Big-Red-Sat/Perovskite-Curve-Tracer/paper/Curve Tracer Hardware.pdf

## An Open Source Perovskite Solar Cell Passive Curve Tracer

Walker S. Arce

University of Nebraska-Lincoln, Department of Electrical and Computer Engineering, Lincoln, 68588, United States

E-mail: wsarcera@gmail.com

September 2025

Abstract. When developing systems for perovskite solar cells, it’s important to have a testing platform that closely resembles your deployed systems. While developing a 1U CubeSat, the Big Red Sat-1, at the University of Nebraska-Lincoln, we found a lack of passive curve tracing instrumentation, which we needed for our mission. To that end, we developed a benchtop passive curve tracer that leverages the Ossila Solar Simulator as an AM1.0 light source. This device utilizes a ladder of switched resistors and a precision voltage and current measurement to achieve the curve tracing. It also integrates a common-anode multiplexer to switch through multi-pixel perovskite solar cells. Finally, the solar cell holder is separate from the main measurement system, so various substrates sizes and pixel counts can be supported. This system is tested using various perovskite solar cells. It has been open sourced to enable reuse in future systems that may benefit from the lower power consumption and flight heritage.

REFERENCES | 2
20 | Introduction
21 | Methods
22 | Results
23 | Discussion
24 | Conclusions
25 | Acknowledgments
26 | Author contributions statement
27 | Competing interests
28 | References
29 | [1] Walker Arce. “Unobtrusive Data Collection in Clinical Settings for Advanced
30 | Patient Monitoring and Machine Learning”. MA thesis. University of Nebraska-
31 | Lincoln, 2023.
32 | [2] Walker Arce and James Gehringer. “Biosensor framework: AC# library for
33 | affective computing”. In: Journal of Open Source Software 6.64 (2021), p. 3455.
34 | [3] Walker S Arce et al. “Detecting aggression in clinical treatment videos”. In:
35 | Machine Learning with Applications 14 (2023), p. 100515.
36 | [4] Mathias Benedek and Christian Kaernbach. “A continuous measure of phasic
37 | electrodermal activity”. In: Journal of neuroscience methods 190.1 (2010), pp. 80–
38 | 91.
39 | [5] Marc G Berman, John Jonides, and Stephen Kaplan. “The cognitive benefits of
40 | interacting with nature”. In: Psychological science 19.12 (2008), pp. 1207–1212.
41 | [6] L Breiman. “Random forests-random features Technical Report 576”. In: Statistical
42 | Department, UC Berkeley, USA (1999).
43 | [7] Leo Breiman and Ross Ihaka. Nonlinear discriminant analysis via scaling and
44 | ACE. Department of Statistics, University of California Davis One Shields
45 | Avenue . . ., 1984.
46 | [8] David F Cella and Samuel W Perry. “Reliability and concurrent validity of three
47 | visual-analogue mood scales”. In: Psychological reports 59.2 (1986), pp. 827–833.
48 | [9] Bernadine Cimprich. “Development of an intervention to restore attention in
49 | cancer patients”. In: Cancer nursing 16.2 (1993), pp. 83–92.
50 | [10] Jonathan D Cohen et al. “Activation of the prefrontal cortex in a nonspatial
51 | working memory task with functional MRI”. In: Human brain mapping 1.4 (1994),
52 | pp. 293–304.

REFERENCES | 3
[11] Christian Collet et al. “Autonomic nervous system response patterns specificity to basic emotions”. In: Journal of the autonomic nervous system 62.1-2 (1997), pp. 45–57.
[12] Sidney D’Mello, Arvid Kappas, and Jonathan Gratch. “The affective computing approach to affect measurement”. In: Emotion Review 10.2 (2018), pp. 174–183.
[13] Jia Deng et al. “Imagenet: A large-scale hierarchical image database”. In: 2009 IEEE conference on computer vision and pattern recognition. Ieee. 2009, pp. 248– 255.
[14] Deniz Ekiz et al. “Can a smartband be used for continuous implicit authentication in real life”. In: IEEE Access 8 (2020), pp. 59402–59411.
[15] Vahid Farrahi et al. “Evaluating and enhancing the generalization performance of machine learning models for physical activity intensity prediction from raw acceleration data”. In: IEEE journal of biomedical and health informatics 24.1 (2019), pp. 27–38.
[16] Simon Föll et al. “FLIRT: A feature generation toolkit for wearable data”. In: Computer Methods and Programs in Biomedicine 212 (2021), p. 106461.
[17] Martin Gjoreski et al. “Datasets for cognitive load inference using wearable sensors and psychological traits”. In: Applied Sciences 10.11 (2020), p. 3843.
[18] Matthew S Goodwin et al. “Predicting aggression to others in youth with autism using a wearable biosensor”. In: Autism research 12.8 (2019), pp. 1286–1296.
[19] Alberto Greco et al. “cvxEDA: A convex optimization approach to electrodermal activity processing”. In: IEEE transactions on biomedical engineering 63.4 (2015), pp. 797–804.
[20] Linda Handlin et al. “Short-term interaction between dogs and their owners: effects on oxytocin, cortisol, insulin and heart rate—an exploratory study”. In: Anthrozoös 24.3 (2011), pp. 301–315.
[21] Trevor Hastie et al. The elements of statistical learning: data mining, inference, and prediction. Vol. 2. Springer, 2009.
[22] Jennifer A Healey and Rosalind W Picard. “Detecting stress during real-world driving tasks using physiological sensors”. In: IEEE Transactions on intelligent transportation systems 6.2 (2005), pp. 156–166.
[23] Geoffrey E Hinton. “Connectionist learning procedures”. In: Machine learning. Elsevier, 1990, pp. 555–610.
[24] Seyedmajid Hosseini et al. “A multimodal sensor dataset for continuous stress detection of nurses in a hospital”. In: Scientific Data 9.1 (2022), p. 255.
[25] Palanisamy Karthikeyan, Murugappan Murugappan, and Sazali Yaacob. “Descriptive analysis of skin temperature variability of sympathetic nervous system activity in stress”. In: Journal of Physical Therapy Science 24.12 (2012), pp. 1341–1344.
[26] Diederik P Kingma and Jimmy Ba. “Adam: A method for stochastic optimization”. In: arXiv preprint arXiv:1412.6980 (2014).

REFERENCES | 4
93 | [27] Sylvia D Kreibig. “Autonomic nervous system activity in emotion: A review”. In:
94 | Biological psychology 84.3 (2010), pp. 394–421.
95 | [28] Qiang Li and Kunio Doi. “Reduction of bias and variance for evaluation of
96 | computer-aided diagnostic schemes”. In: Medical physics 33.4 (2006), pp. 868–
97 | 875.
98 | [29] Brian Mac Namee et al. “The problem of bias in training data in regression
99 | problems in medical decision support”. In: Artificial intelligence in medicine 24.1
100 | (2002), pp. 51–70.
101 | [30] Cathy L McEvoy, Douglas L Nelson, and Takako Komatsu. “What is the
102 | connection between true and false memories? The differential roles of interitem
103 | associations in recall and recognition.” In: Journal of Experimental Psychology:
104 | Learning, Memory, and Cognition 25.5 (1999), p. 1177.
105 | [31] J Orbach, Dan Ehrlich, and Helen A Heath. “Reversibility of the Necker cube: I.
106 | An examination of the concept of “satiation of orientation””. In: Perceptual and
107 | motor skills 17.2 (1963), pp. 439–458.
108 | [32] Fabian Pedregosa et al. “Scikit-learn: Machine learning in Python”. In: the Journal
109 | of machine Learning research 12 (2011), pp. 2825–2830.
110 | [33] Jonathan Peirce et al. “PsychoPy2: Experiments in behavior made easy”. In:
111 | Behavior research methods 51 (2019), pp. 195–203.
112 | [34] Laura E Phipps et al. “Assessing physiological arousal and emotional valence
113 | during behavioral intervention for pediatric feeding difficulties: A pilot study”.
114 | In: Mental Health Science (2024), e74.
115 | [35] Rosalind W Picard. Affective computing. MIT press, 2000.
116 | [36] Ming-Zher Poh, Nicholas C Swenson, and Rosalind W Picard. “A wearable
117 | sensor for unobtrusive, long-term assessment of electrodermal activity”. In: IEEE
118 | transactions on Biomedical engineering 57.5 (2010), pp. 1243–1252.
119 | [37] Society for Psychophysiological Research Ad Hoc Committee on Electrodermal
120 | Measures et al. “Publication recommendations for electrodermal measurements”.
121 | In: Psychophysiology 49.8 (2012), pp. 1017–1034.
122 | [38] Nishkam Ravi et al. “Activity recognition from accelerometer data”. In: Aaai.
123 | Vol. 5. Pittsburgh, PA. 2005, pp. 1541–1546.
124 | [39] Debra Lynn Rich. “Effects of exposure to nature and plants on cognition and
125 | mood: A cognitive psychology perspective”. PhD thesis. Cornell University, 2007.
126 | [40] Henry L Roediger and Kathleen B McDermott. “Creating false memories:
127 | Remembering words not presented in lists.” In: Journal of experimental psychology:
128 | Learning, Memory, and Cognition 21.4 (1995), p. 803.
129 | [41] Eva Sahlin et al. “The influence of the environment on directed attention, blood
130 | pressure and heart rate—An experimental study using a relaxation intervention”.
131 | In: Landscape Research 41.1 (2016), pp. 7–25.

REFERENCES | 5
[42] E Salazar-López et al. “The mental and subjective skin: Emotion, empathy, feelings and thermography”. In: Consciousness and cognition 34 (2015), pp. 149–162.
[43] Philip Schmidt et al. “Introducing wesad, a multimodal dataset for wearable stress and affect detection”. In: Proceedings of the 20th ACM international conference on multimodal interaction. 2018, pp. 400–408.
[44] Fred Shaffer and Jay P Ginsberg. “An overview of heart rate variability metrics and norms”. In: Frontiers in public health 5 (2017), p. 258.
[45] Karan Sharma et al. “A dataset of continuous affect annotations and physiological signals for emotion analysis”. In: Scientific data 6.1 (2019), p. 196.
[46] Dimitris Spathis et al. “Learning generalizable physiological representations from large-scale wearable data”. In: arXiv preprint arXiv:2011.04601 (2020).
[47] Charles D Spielberger et al. Measuring anxiety and anger with the State-Trait Anxiety Inventory (STAI) and the State-Trait Anger Expression Inventory (STAXI). Lawrence Erlbaum Associates Publishers, 1999.
[48] Jeffrey R. Stevens and Elise R. Thayer. “Effects of human-animal interactions on affect and cognition”. In: Human-animal interaction bulletin (2020). url: https: //api.semanticscholar.org/CorpusID:225526352.
[49] Mohammed Taj-Eldin et al. “A review of wearable solutions for physiological and emotional monitoring for use by people with autism spectrum disorder and their caregivers”. In: Sensors 18.12 (2018), p. 4271.
[50] Hoang Minh Thang et al. “Gait identification using accelerometer on mobile phone”. In: 2012 International Conference on Control, Automation and Information Sciences (ICCAIS). IEEE. 2012, pp. 344–348.
[51] Elise R Thayer and Jeffrey R Stevens. “Effects of human-animal interactions on affect and cognition”. In: Human-Animal Interaction Bulletin 2022 (2022).
[52] Paul Van Gent et al. “HeartPy: A novel heart rate algorithm for the analysis of noisy signals”. In: Transportation research part F: traffic psychology and behaviour 66 (2019), pp. 368–378.
[53] David Watson, Lee Anna Clark, and Auke Tellegen. “Development and validation of brief measures of positive and negative affect: the PANAS scales.” In: Journal of personality and social psychology 54.6 (1988), p. 1063.
[54] Debra Wetcher-Hendricks. Analyzing quantitative data: An introduction for social researchers. John Wiley & Sons, 2011.
