Big-Red-Sat/Perovskite-Curve-Tracer/software/curves/1. Round One/1763_Again2/1763_Again2_plotted.png

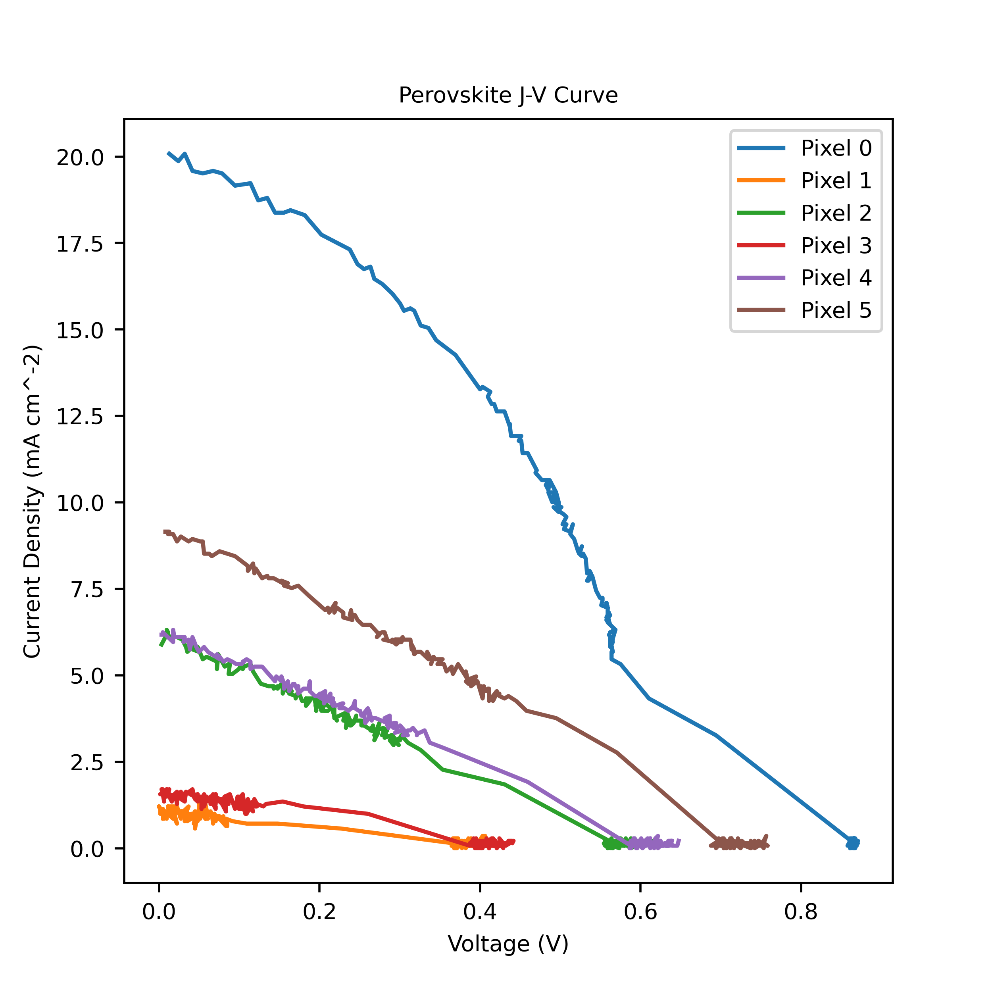
software/curves/1. Round One/1763_Again2/1763_Again2_plotted.png
