Big-Red-Sat/Perovskite-Curve-Tracer/software/curves/1. Round One/1763_Again/1763_Again_plotted.png

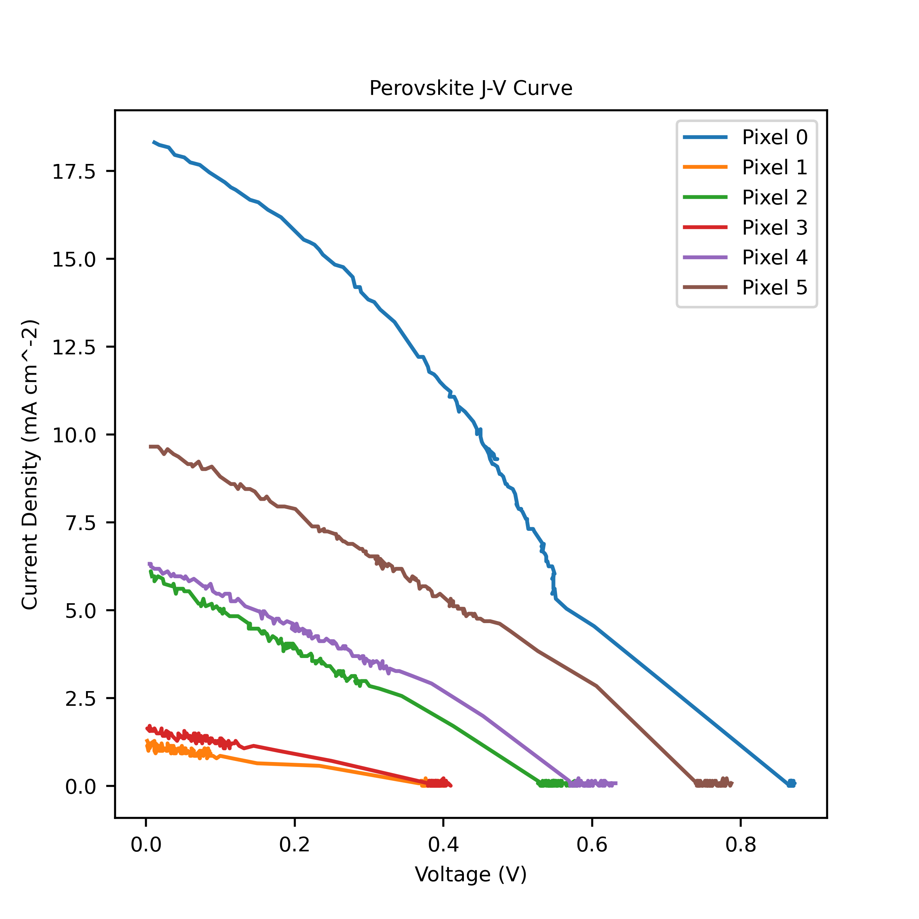
software/curves/1. Round One/1763_Again/1763_Again_plotted.png
