Big-Red-Sat/Perovskite-Curve-Tracer/software/curves/1. Round One/1764_Degradation/1764_08222023/1764_08222023_plotted.png

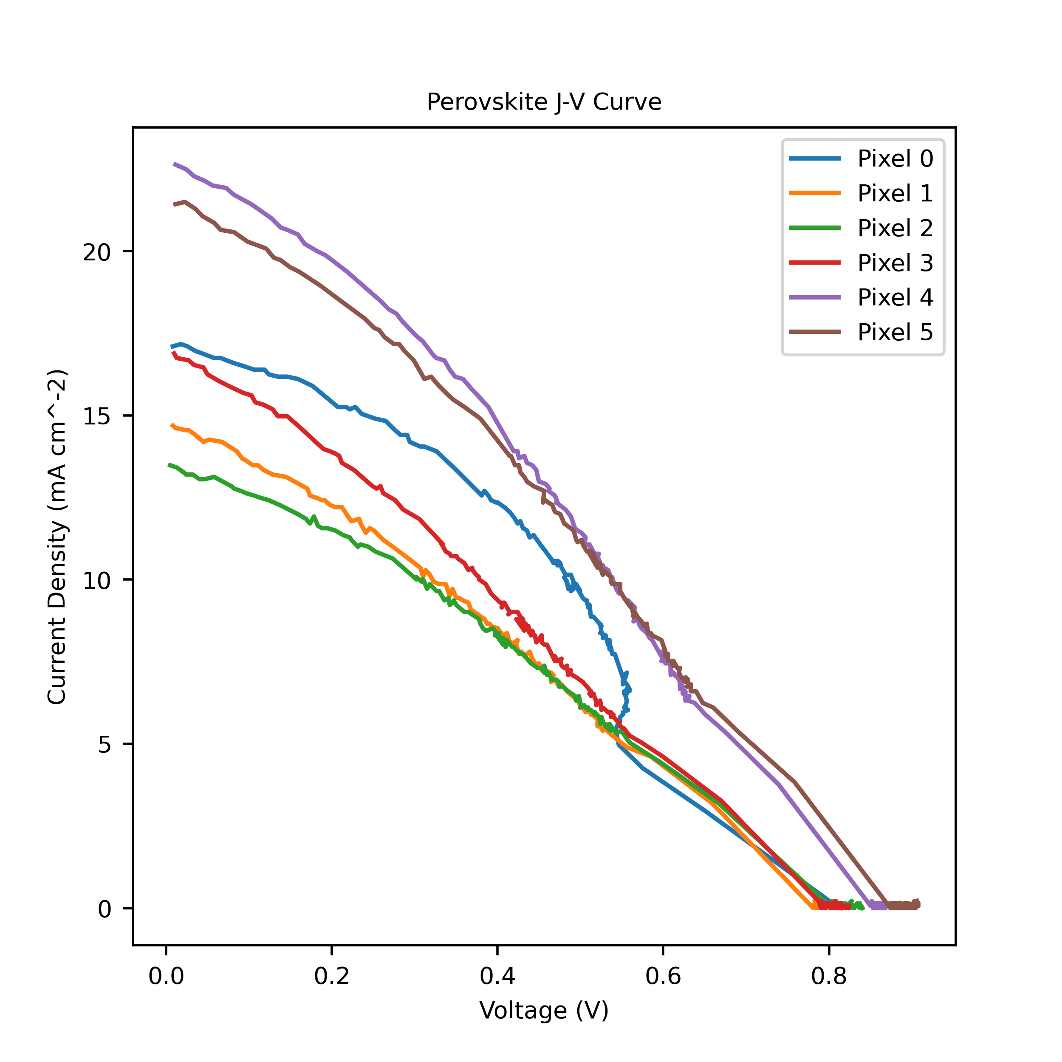
software/curves/1. Round One/1764_Degradation/1764_08222023/1764_08222023_plotted.png
