Big-Red-Sat/Perovskite-Curve-Tracer/software/curves/1. Round One/1764_Degradation/1764_08232023_2/1764_08232023_2_plotted.png

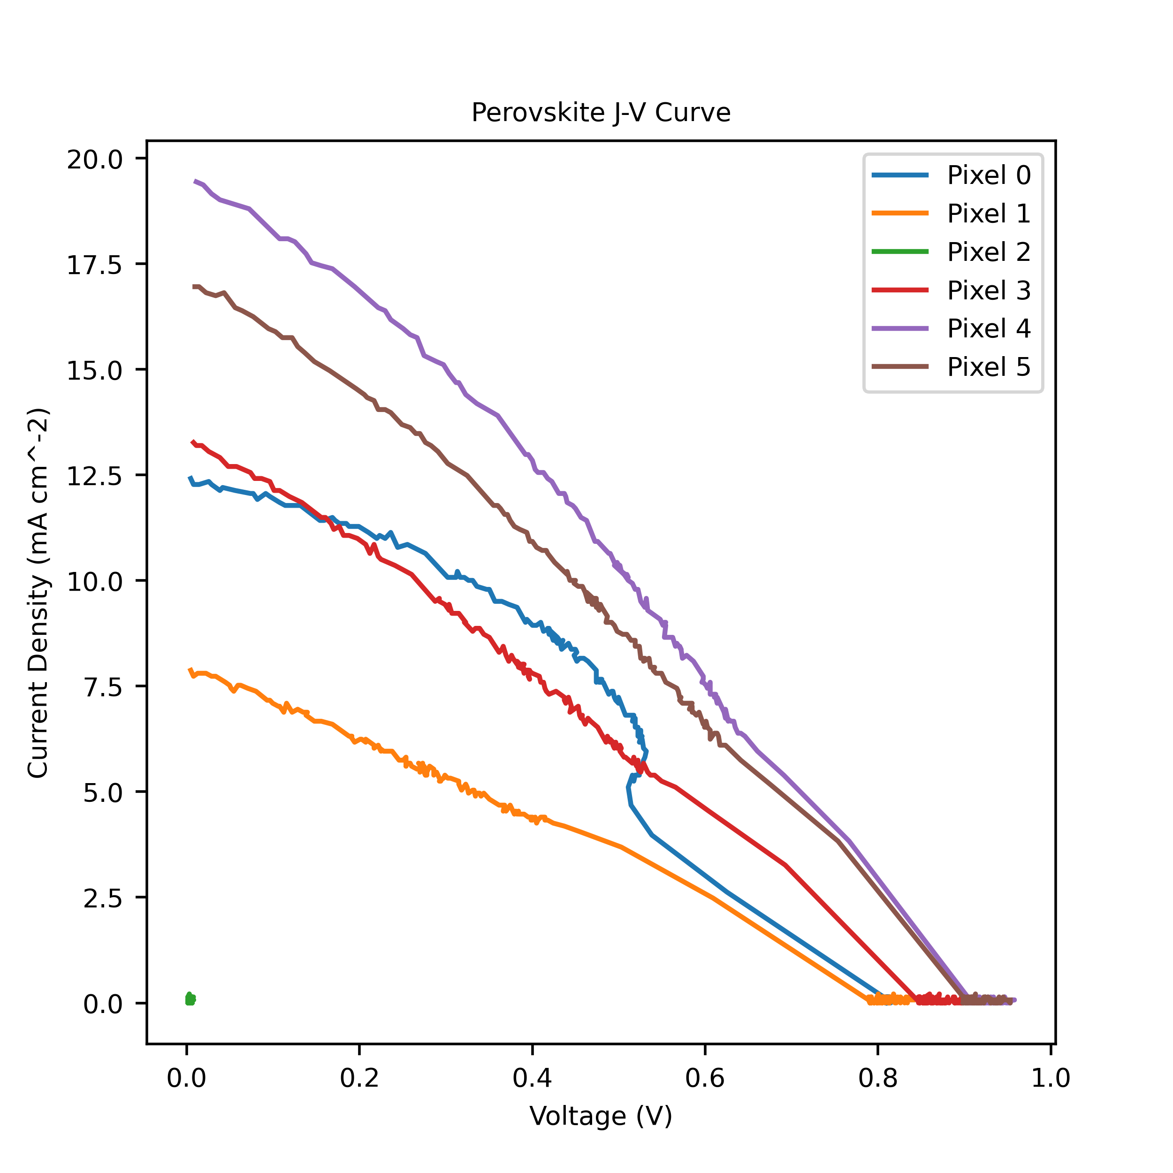
software/curves/1. Round One/1764_Degradation/1764_08232023_2/1764_08232023_2_plotted.png
