Big-Red-Sat/Perovskite-Curve-Tracer/software/curves/1. Round One/1764_Degradation/1764_08242023_LM/1764_08242023_LM_plotted.png

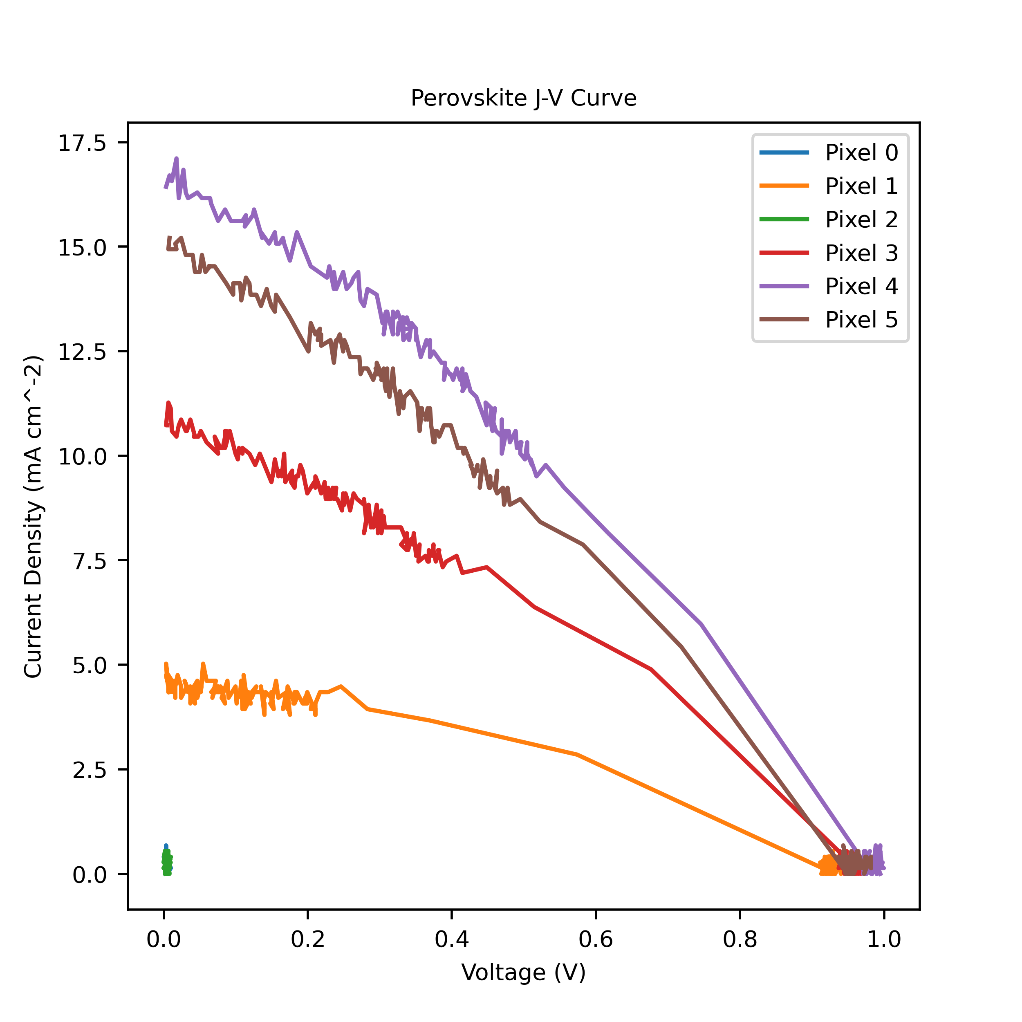
software/curves/1. Round One/1764_Degradation/1764_08242023_LM/1764_08242023_LM_plotted.png
