Big-Red-Sat/Perovskite-Curve-Tracer/software/curves/1. Round One/1764_Degradation/1764_Again/1764_Again_plotted.png

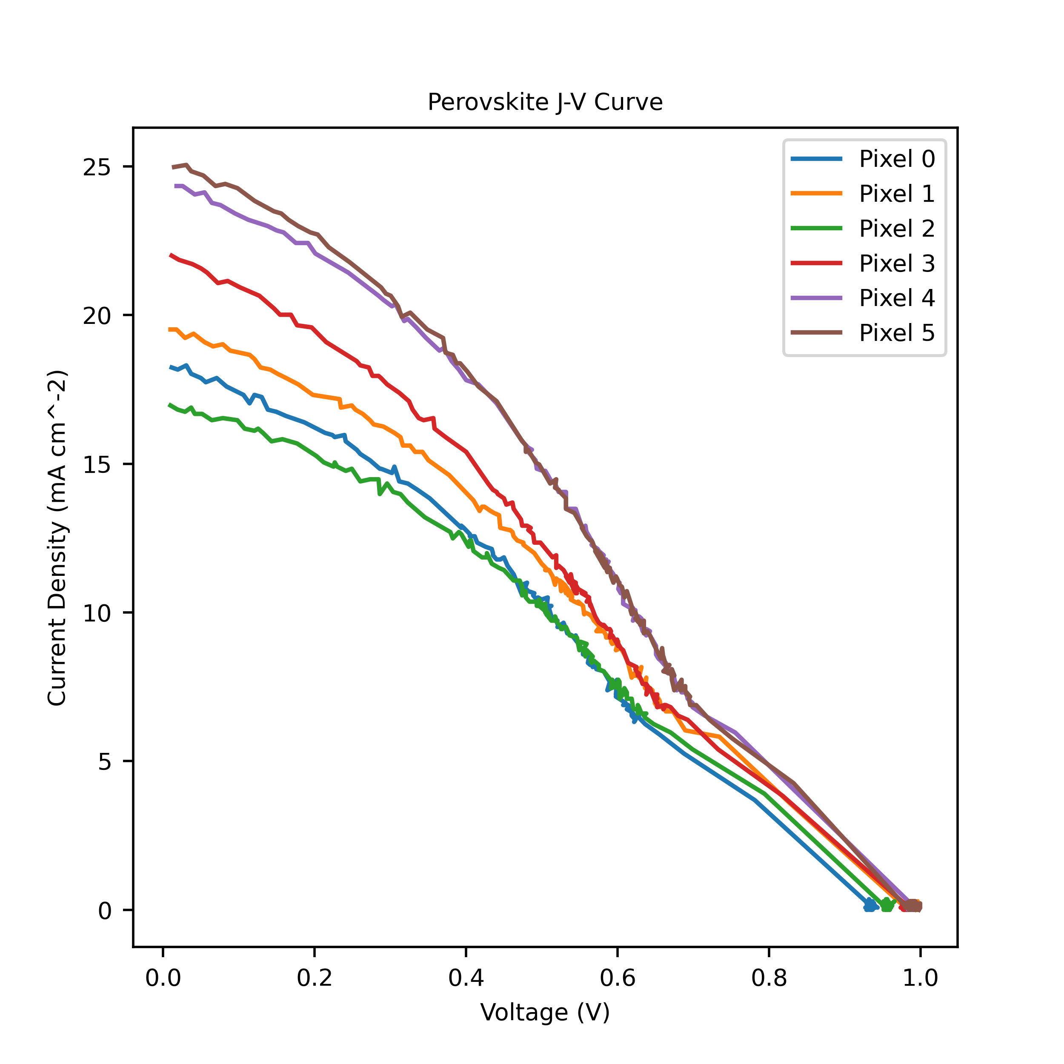
software/curves/1. Round One/1764_Degradation/1764_Again/1764_Again_plotted.png
