Big-Red-Sat/Perovskite-Curve-Tracer/software/curves/1. Round One/1765_Again/1765_Again_plotted.png

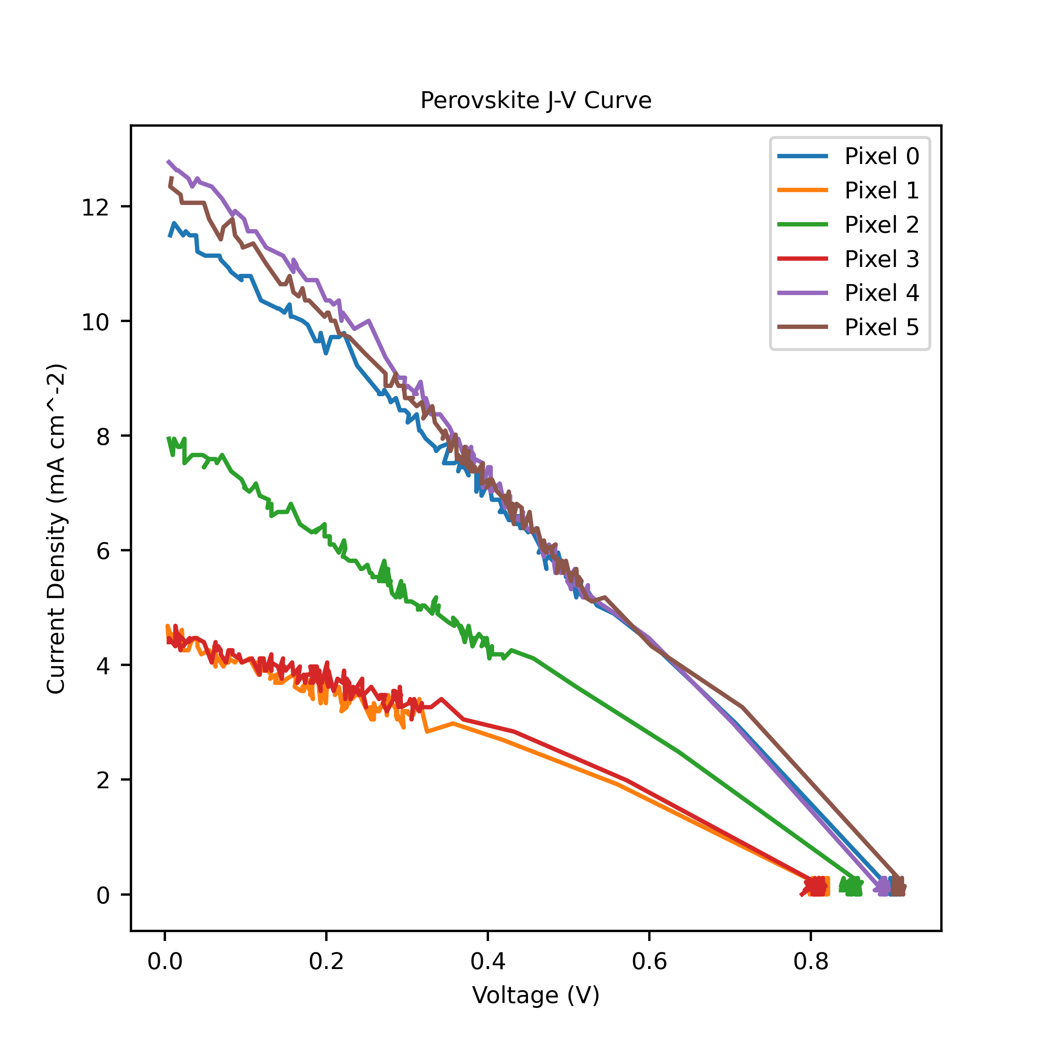
software/curves/1. Round One/1765_Again/1765_Again_plotted.png
