Big-Red-Sat/Perovskite-Curve-Tracer/software/curves/1. Round One/1770_Again/1770_Again_plotted.png

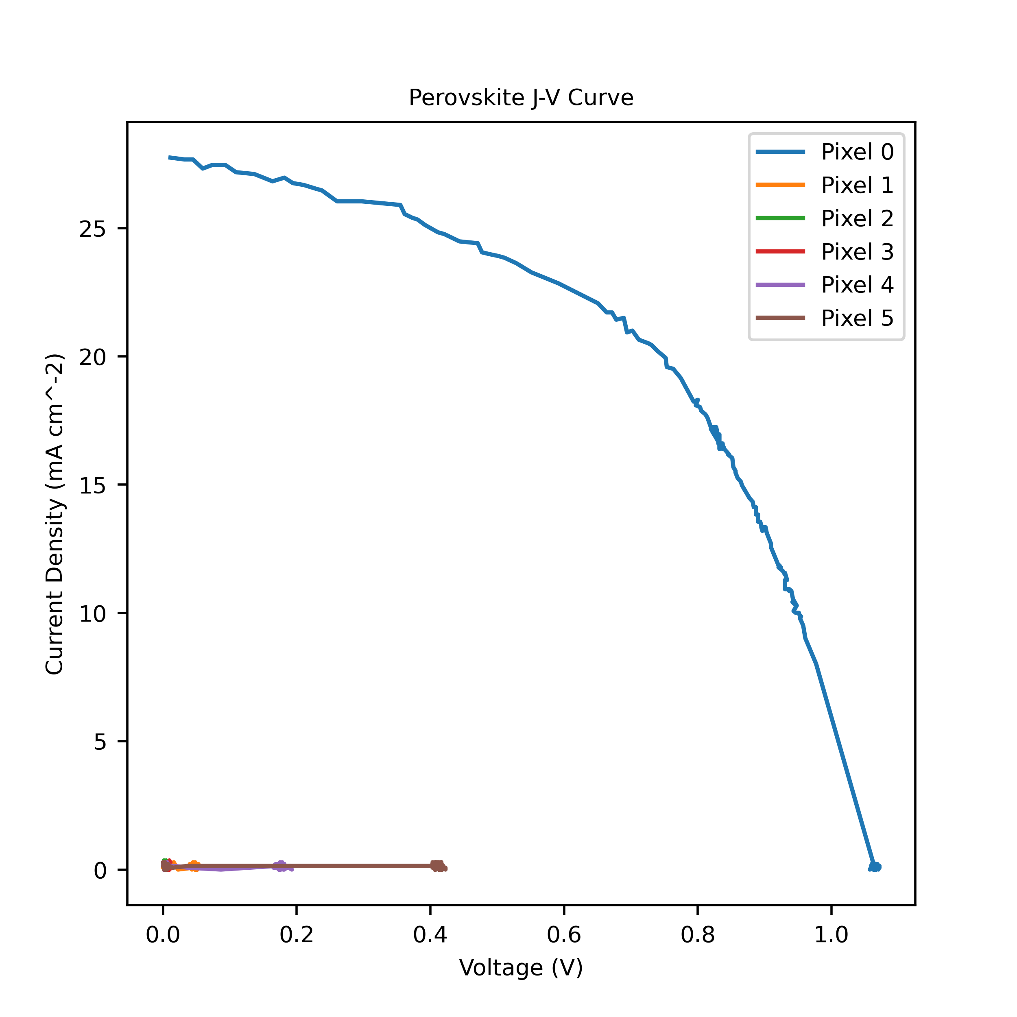
software/curves/1. Round One/1770_Again/1770_Again_plotted.png
