Big-Red-Sat/Perovskite-Curve-Tracer/software/curves/1. Round One/1773_Again/1773_Again_plotted.png

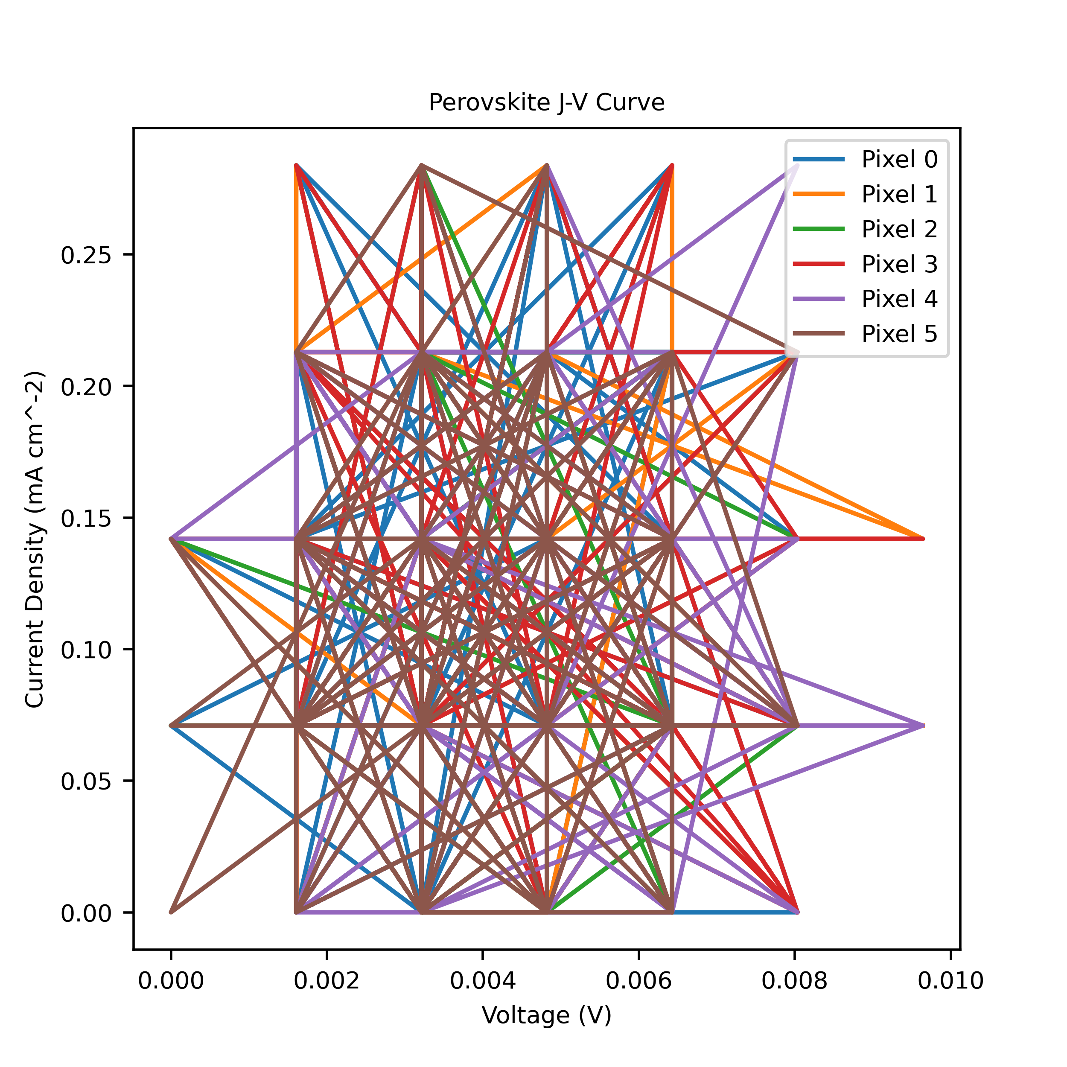
software/curves/1. Round One/1773_Again/1773_Again_plotted.png
