Big-Red-Sat/Perovskite-Curve-Tracer/software/curves/1. Round One/1775_Again/1775_Again_plotted.png

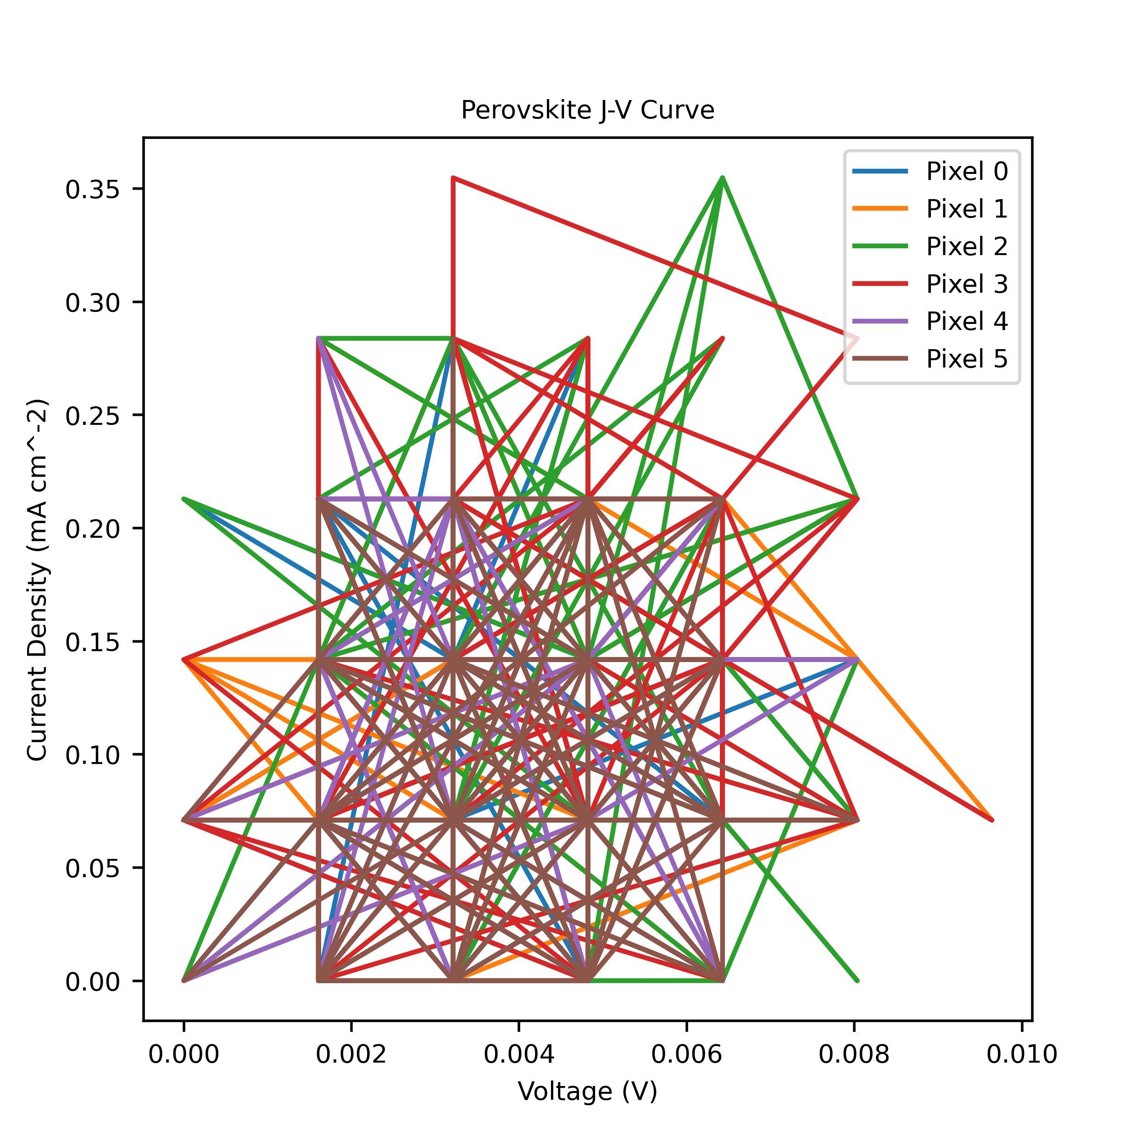
software/curves/1. Round One/1775_Again/1775_Again_plotted.png
