Big-Red-Sat/Perovskite-Curve-Tracer/software/curves/1. Round One/1776 Degradation/1776_08192023/1776_08192023.png

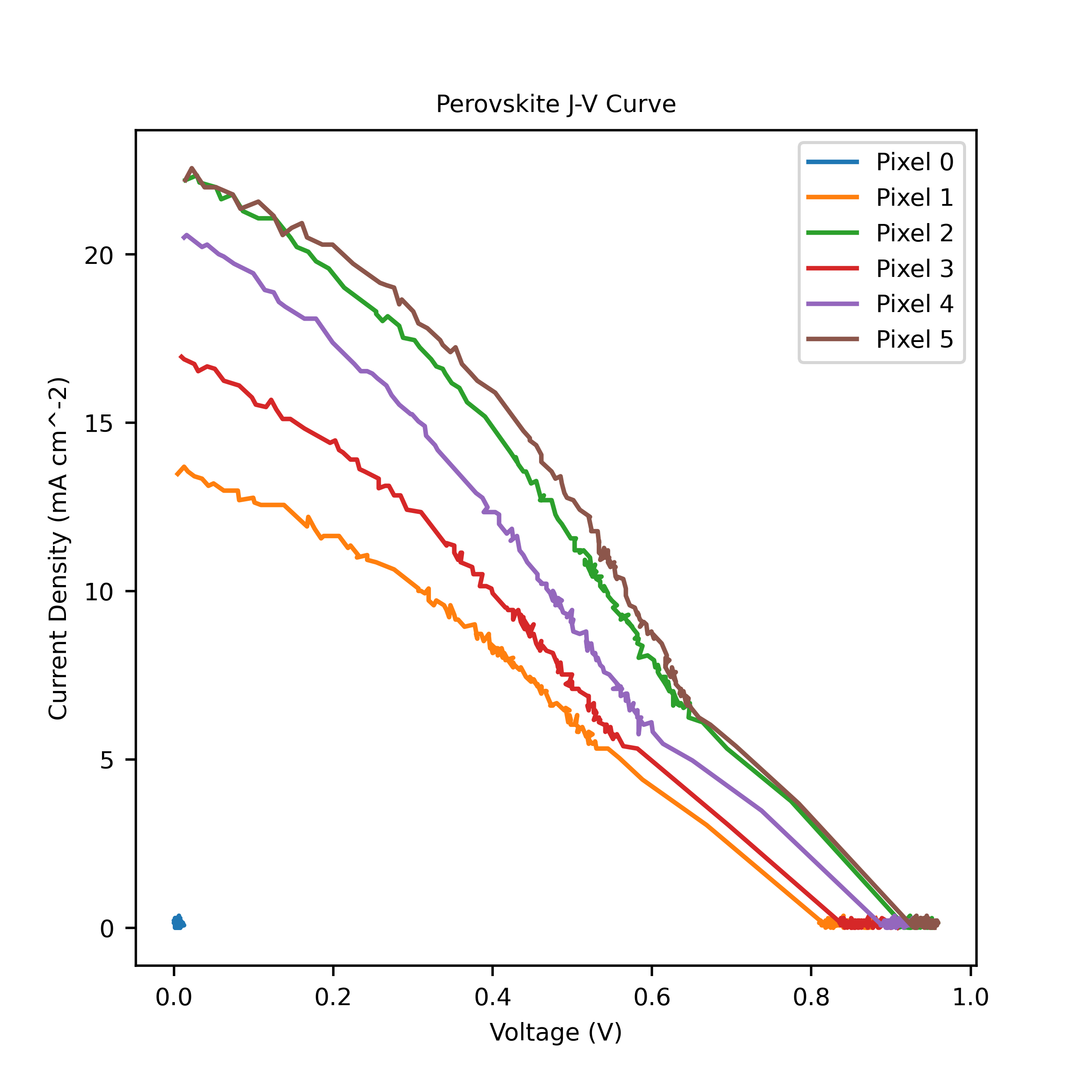
software/curves/1. Round One/1776 Degradation/1776_08192023/1776_08192023.png
