Big-Red-Sat/Perovskite-Curve-Tracer/software/curves/1. Round One/1776 Degradation/1776_08192023_2/1776_Again2_plotted.png

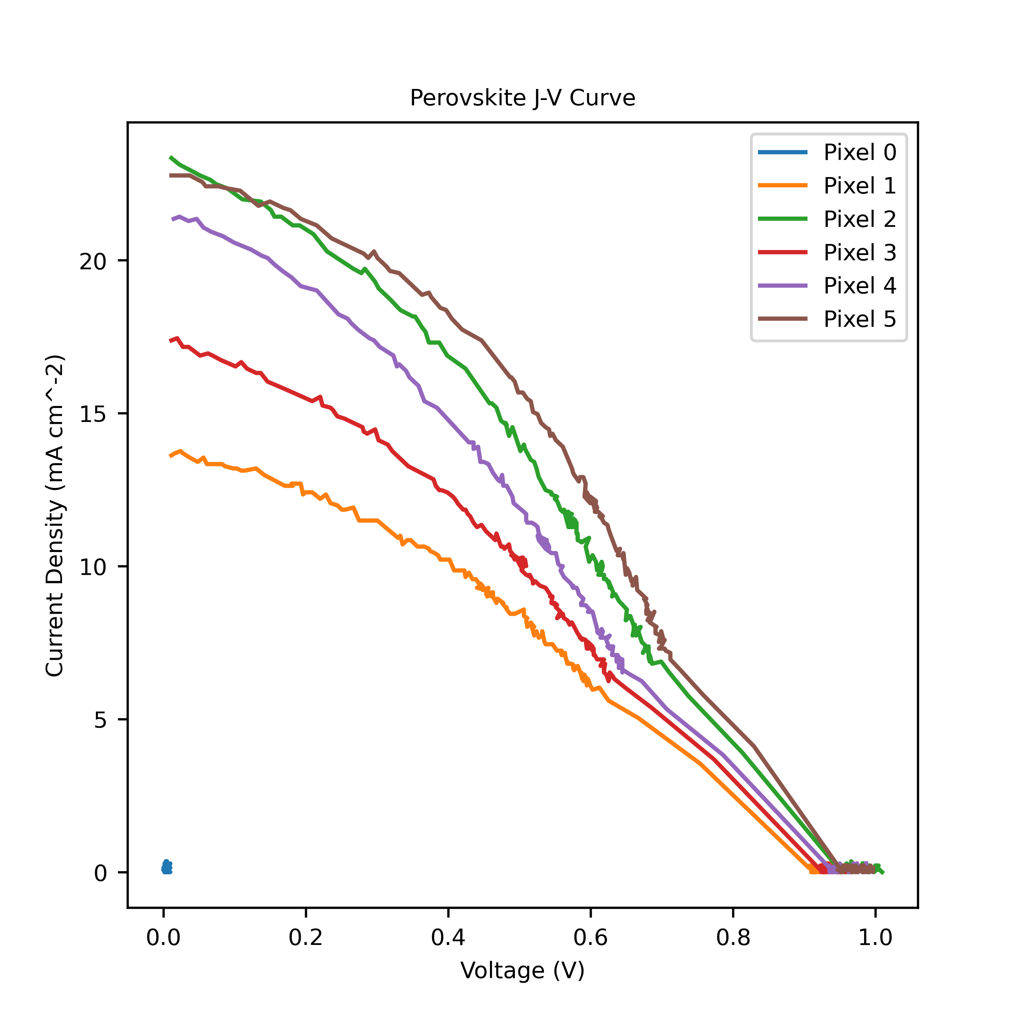
software/curves/1. Round One/1776 Degradation/1776_08192023_2/1776_Again2_plotted.png
