Big-Red-Sat/Perovskite-Curve-Tracer/software/curves/1. Round One/1776 Degradation/1776_08212023_3/1776_08212023_plotted.png

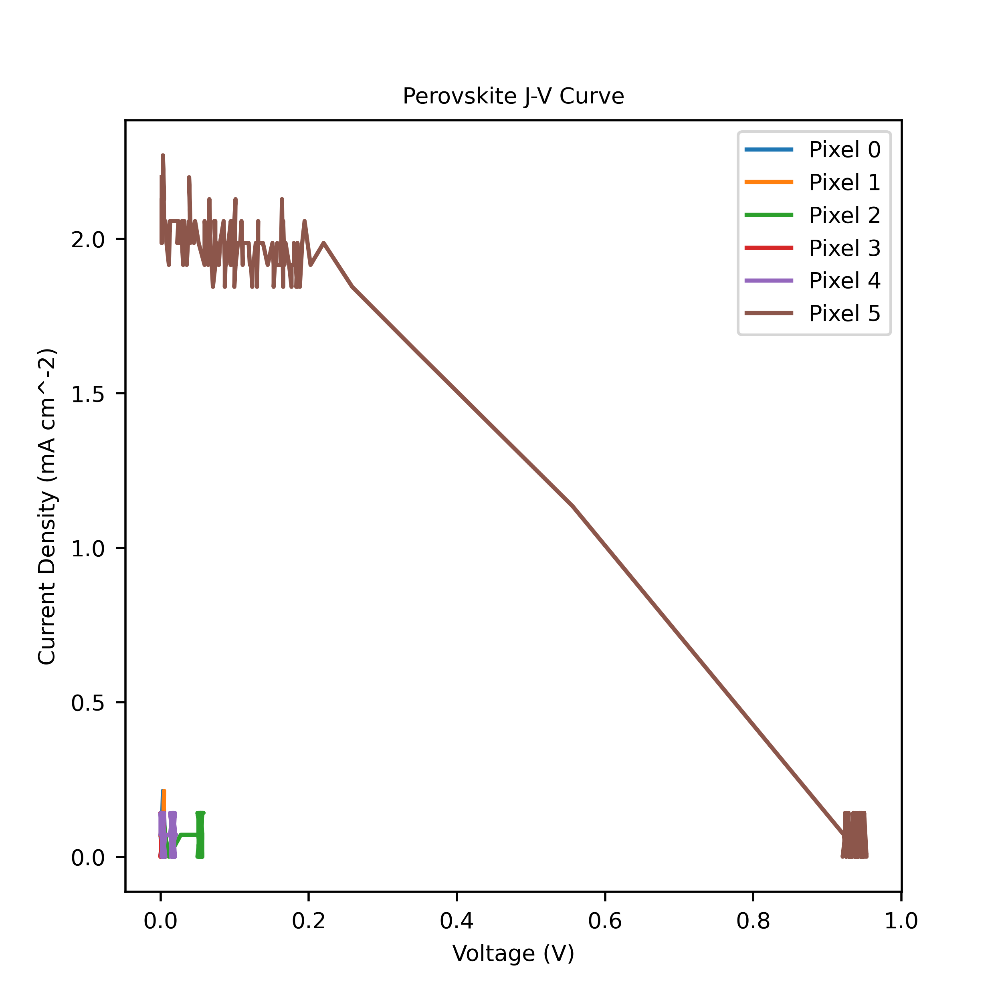
software/curves/1. Round One/1776 Degradation/1776_08212023_3/1776_08212023_plotted.png
