Big-Red-Sat/Perovskite-Curve-Tracer/software/curves/1. Round One/1776 Degradation/1776_08222023_R/1776_08222023_R_plotted.png

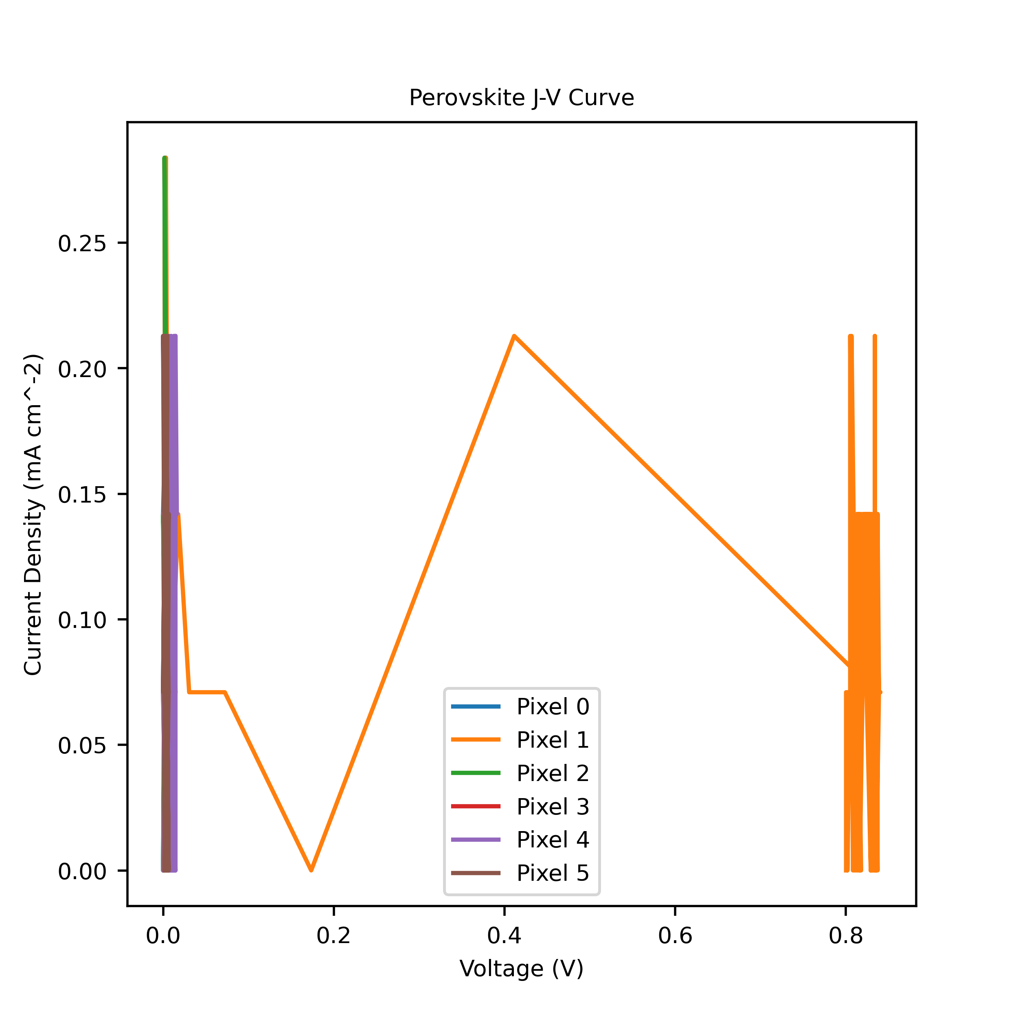
software/curves/1. Round One/1776 Degradation/1776_08222023_R/1776_08222023_R_plotted.png
