Big-Red-Sat/Perovskite-Curve-Tracer/software/curves/2. Round Two/1008_21_15_degredation/1008_21_15_degredation_plotted_Reverse.png

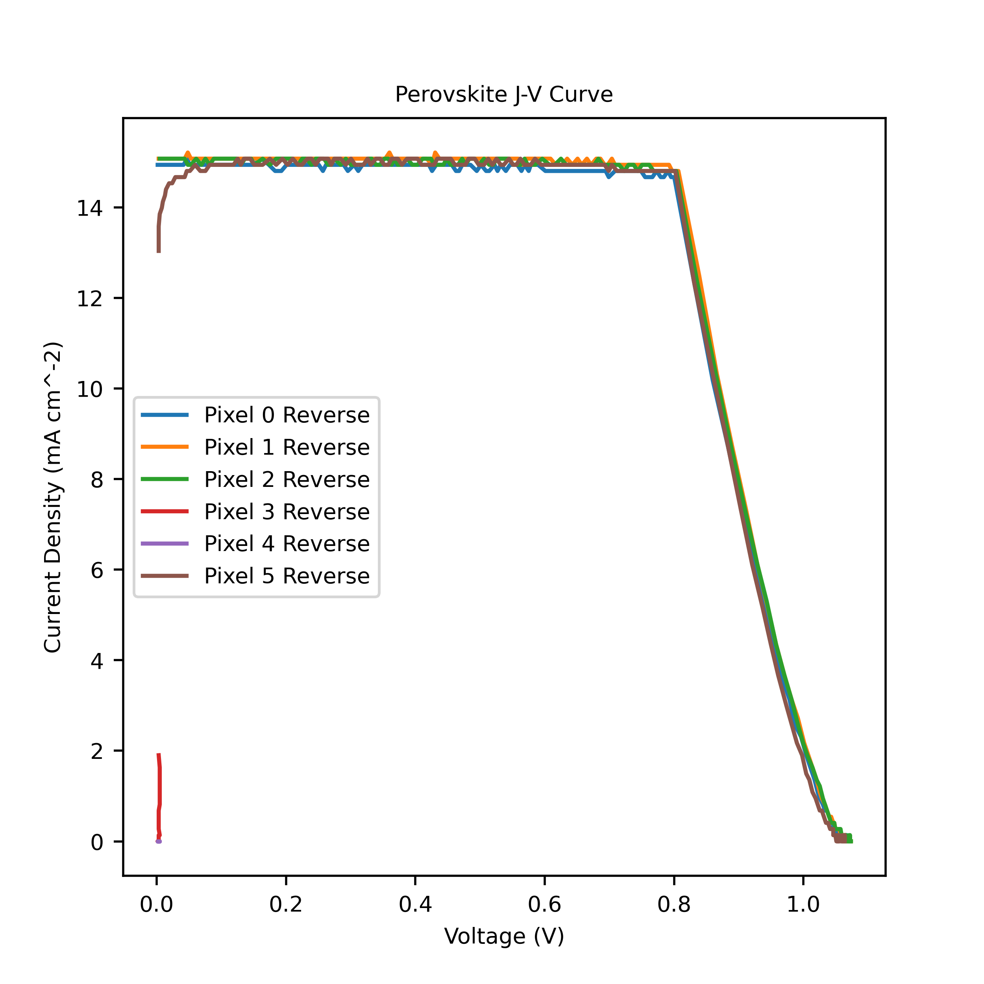
software/curves/2. Round Two/1008_21_15_degredation/1008_21_15_degredation_plotted_Reverse.png
