Big-Red-Sat/Perovskite-Curve-Tracer/software/curves/2. Round Two/100623_14_44_degredations/100623_14_44_degredations_plotted_Forward.png

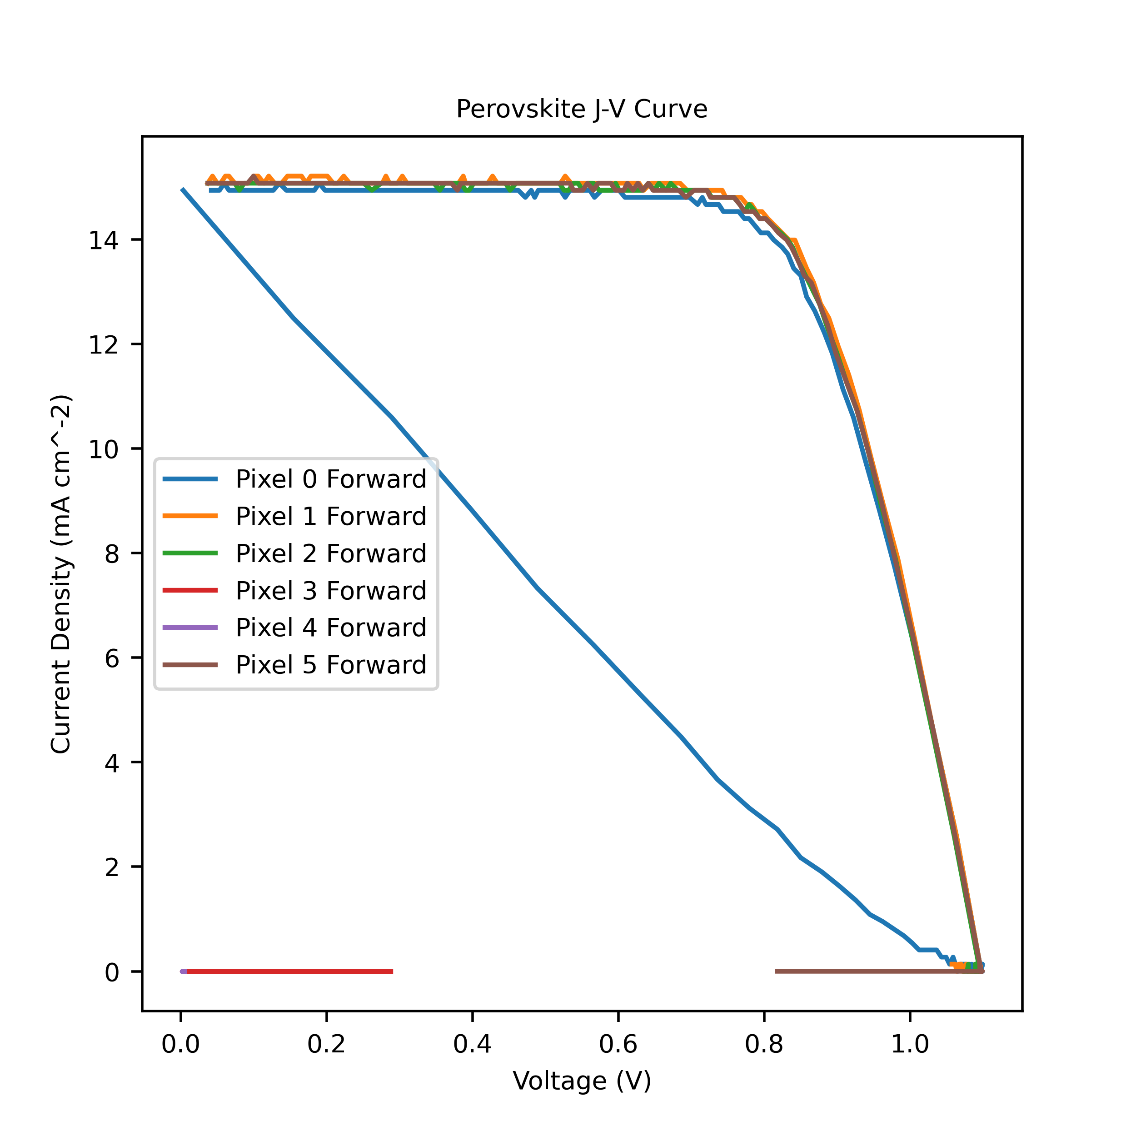
software/curves/2. Round Two/100623_14_44_degredations/100623_14_44_degredations_plotted_Forward.png
