Big-Red-Sat/Perovskite-Curve-Tracer/software/curves/2. Round Two/A48_I2C disconect/A48_I2C disconect_plotted_Forward.png

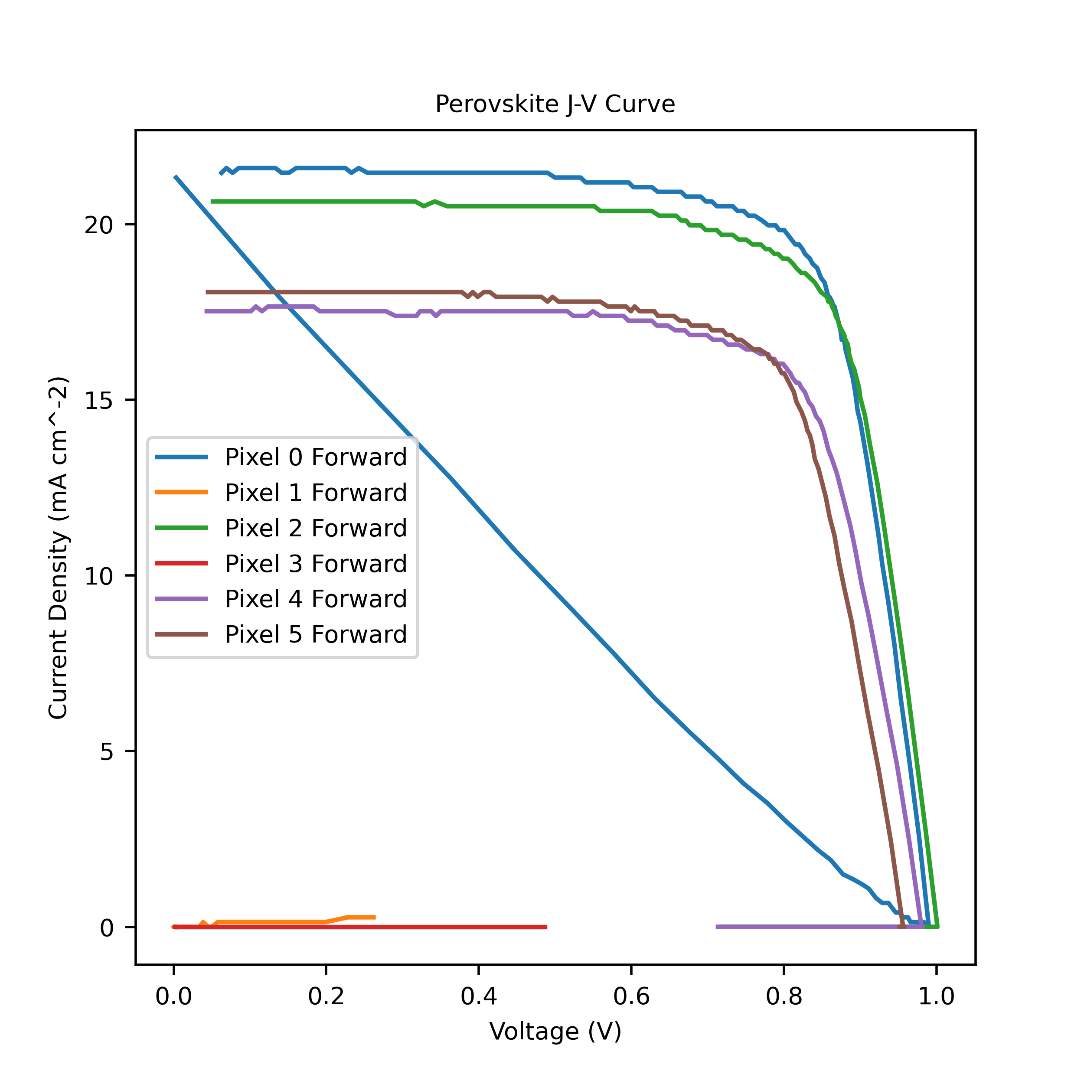
software/curves/2. Round Two/A48_I2C disconect/A48_I2C disconect_plotted_Forward.png
