Big-Red-Sat/Perovskite-Curve-Tracer/software/curves/2. Round Two/A48_I2C disconect_NO_light/A48_I2C disconect_NO_light_plotted_Forward.png

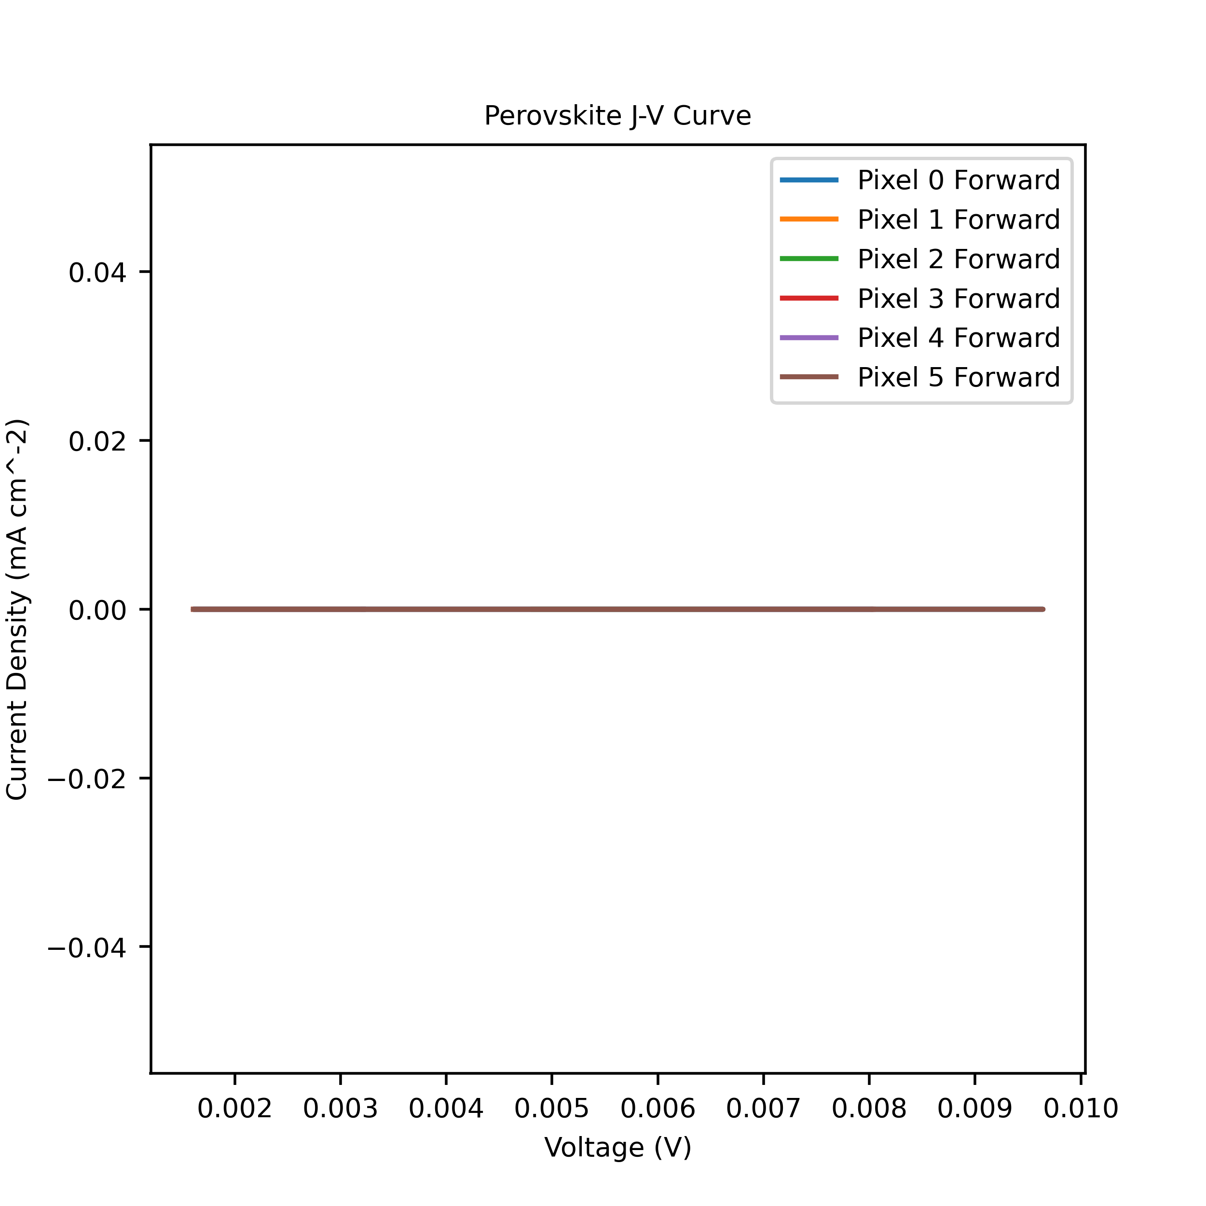
software/curves/2. Round Two/A48_I2C disconect_NO_light/A48_I2C disconect_NO_light_plotted_Forward.png
