Big-Red-Sat/Perovskite-Curve-Tracer/software/curves/2. Round Two/Just Bias/A48_plotted_Reverse.png

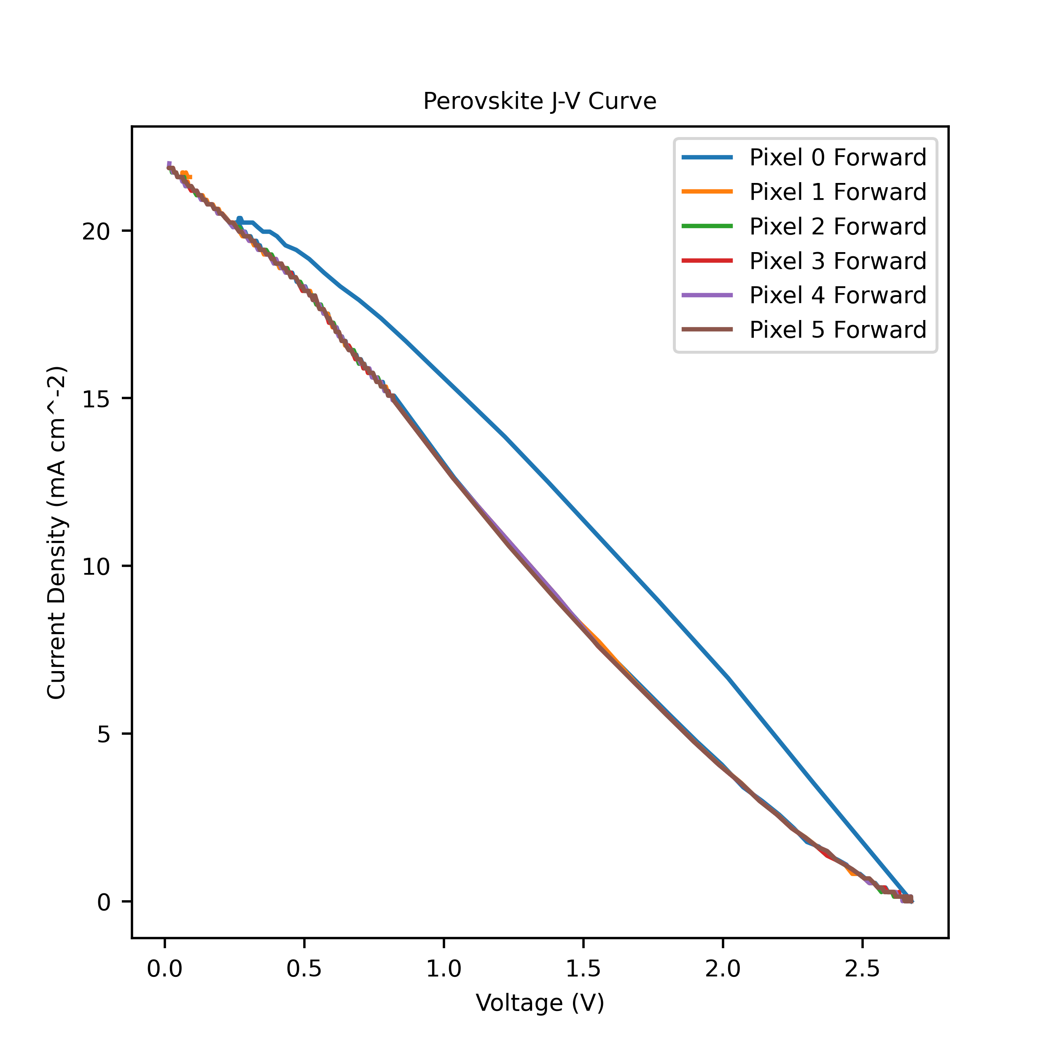
software/curves/2. Round Two/Just Bias/A48_plotted_Reverse.png
