Big-Red-Sat/Perovskite-Curve-Tracer/software/curves/2. Round Two/N001_08272023_LM_2/N001_08272023_LM_2_plotted.png

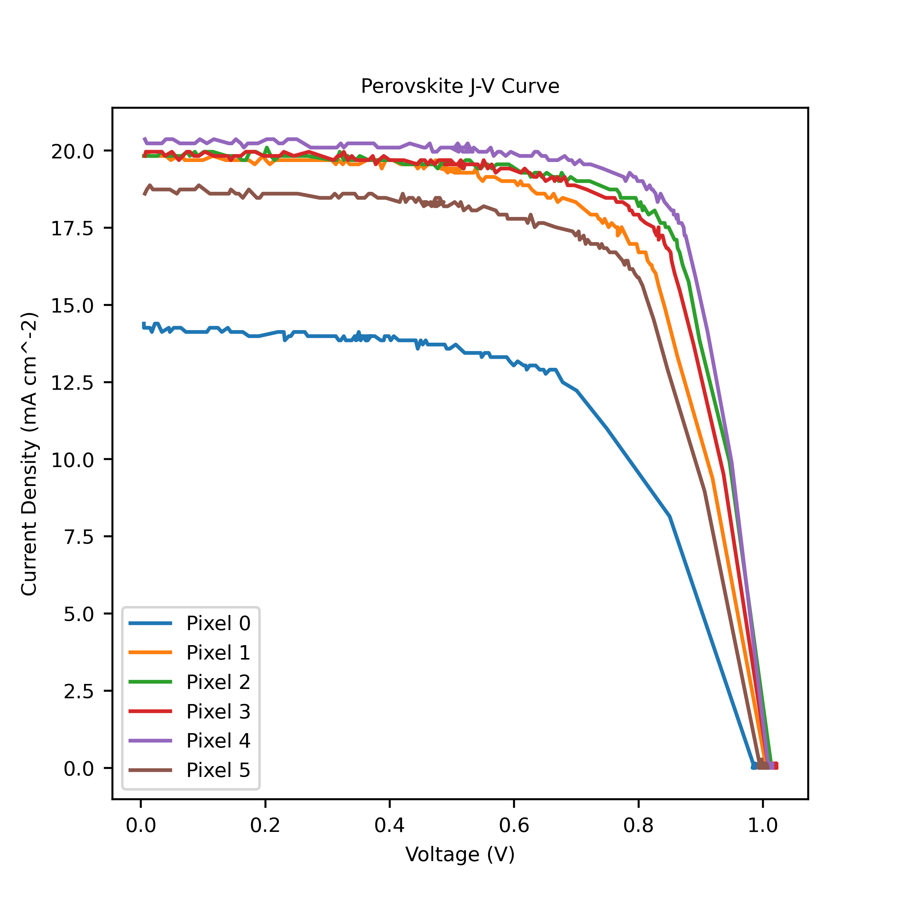
software/curves/2. Round Two/N001_08272023_LM_2/N001_08272023_LM_2_plotted.png
