Big-Red-Sat/Perovskite-Curve-Tracer/software/curves/2. Round Two/N001_08272023_LM_3/N001_08272023_LM_3_plotted.png

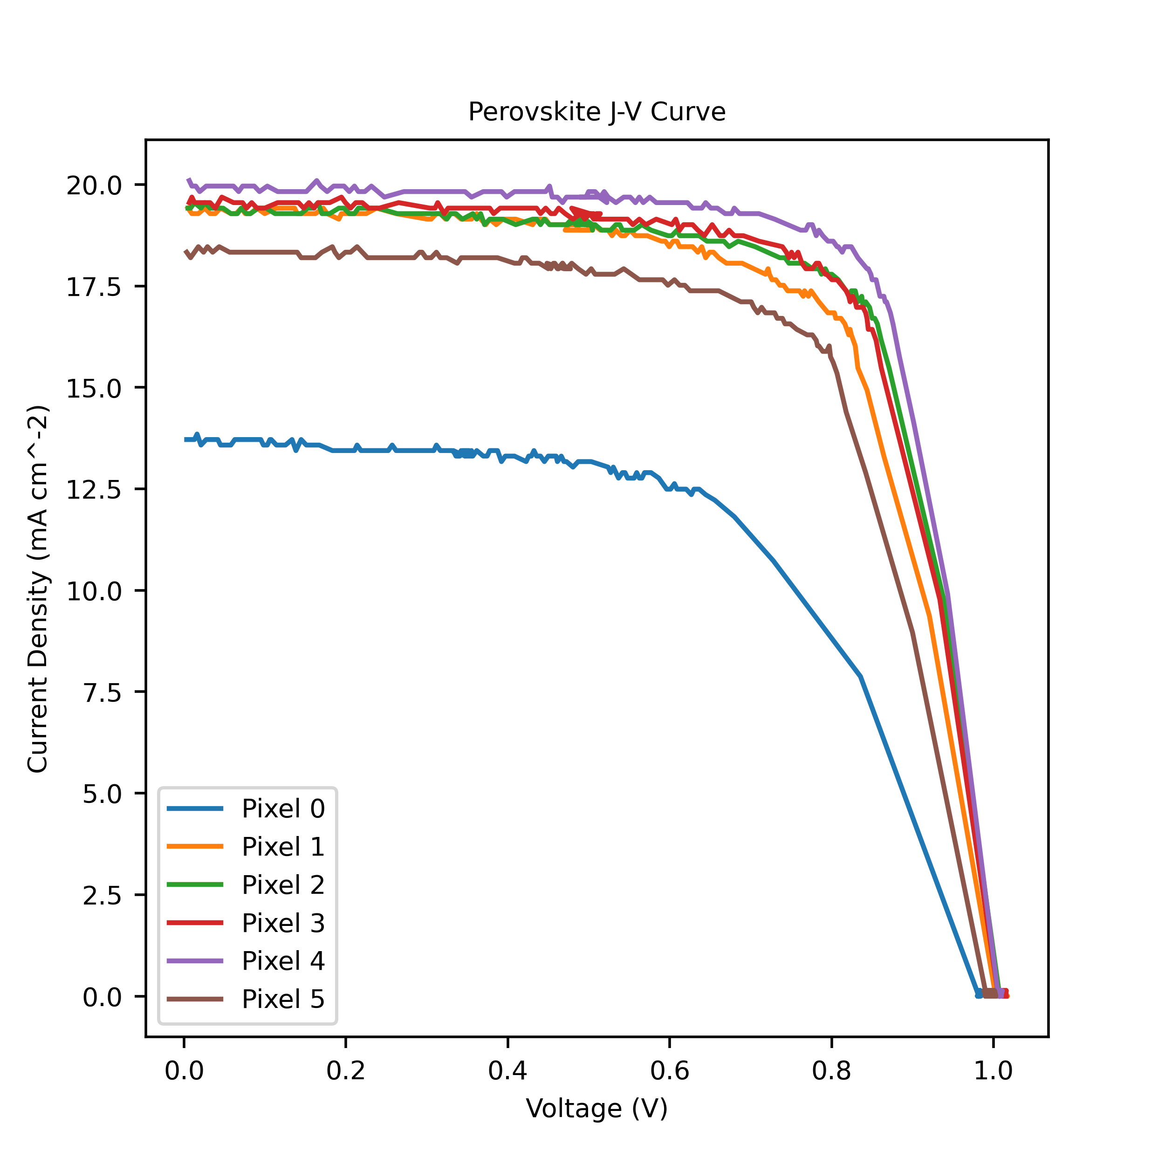
software/curves/2. Round Two/N001_08272023_LM_3/N001_08272023_LM_3_plotted.png
