Big-Red-Sat/Perovskite-Curve-Tracer/software/curves/2. Round Two/N001_Again/curve.png

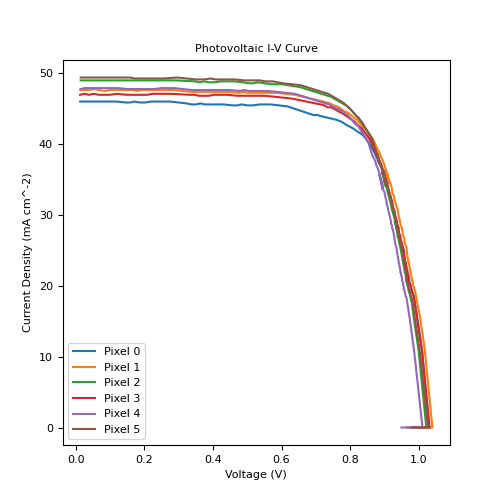
software/curves/2. Round Two/N001_Again/curve.png
