Big-Red-Sat/Perovskite-Curve-Tracer/software/curves/2. Round Two/N002_08272023_LM_2/N002_08272023_LM_2_plotted.png

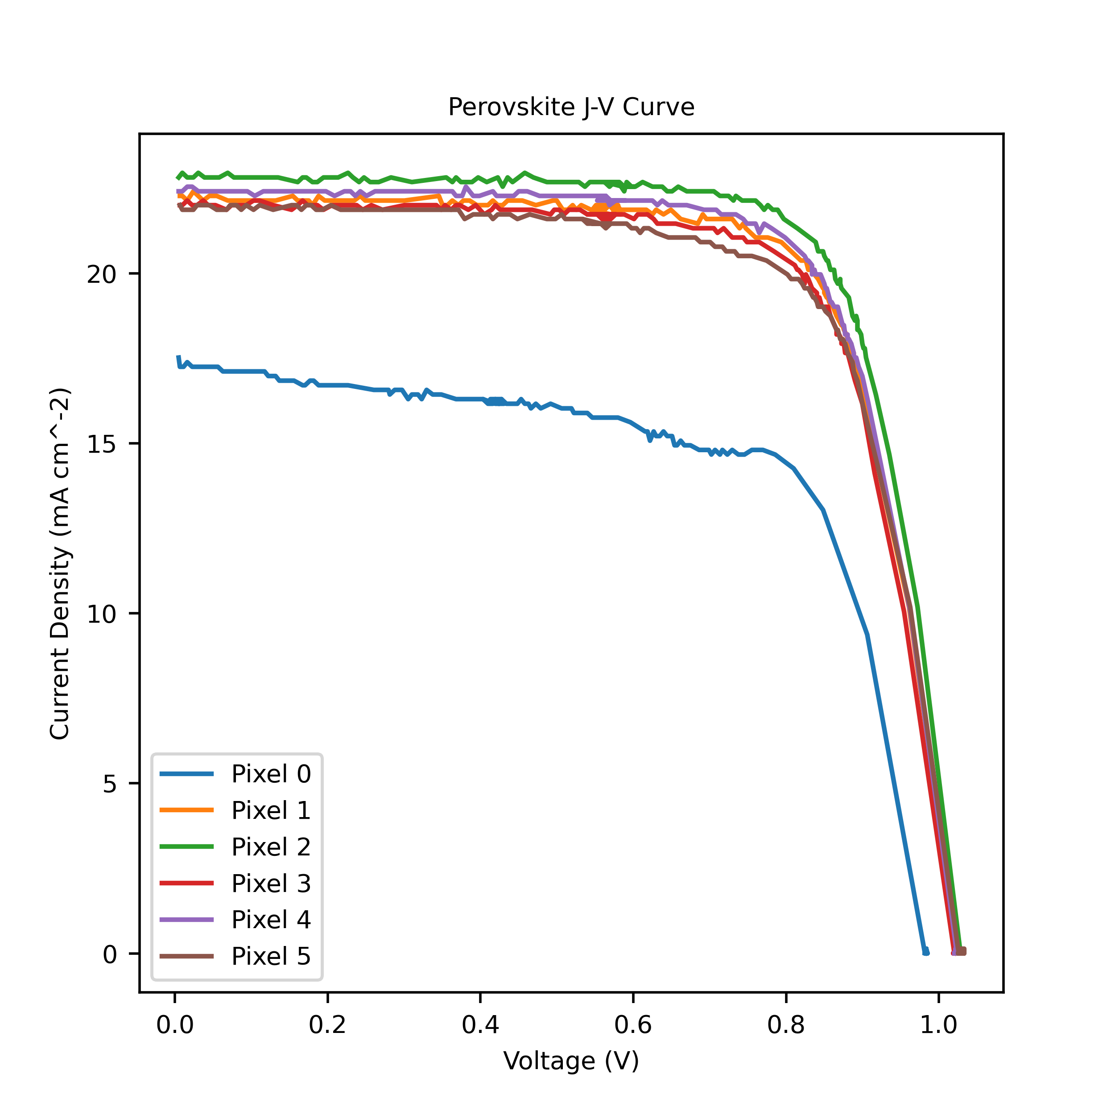
software/curves/2. Round Two/N002_08272023_LM_2/N002_08272023_LM_2_plotted.png
