Big-Red-Sat/Perovskite-Curve-Tracer/software/curves/2. Round Two/N003/curve.png

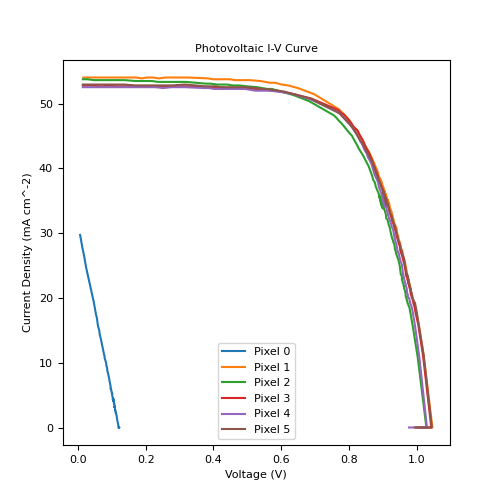
software/curves/2. Round Two/N003/curve.png
