Big-Red-Sat/Perovskite-Curve-Tracer/software/curves/2. Round Two/N003_08272023_LM/N003_08272023_LM_plotted.png

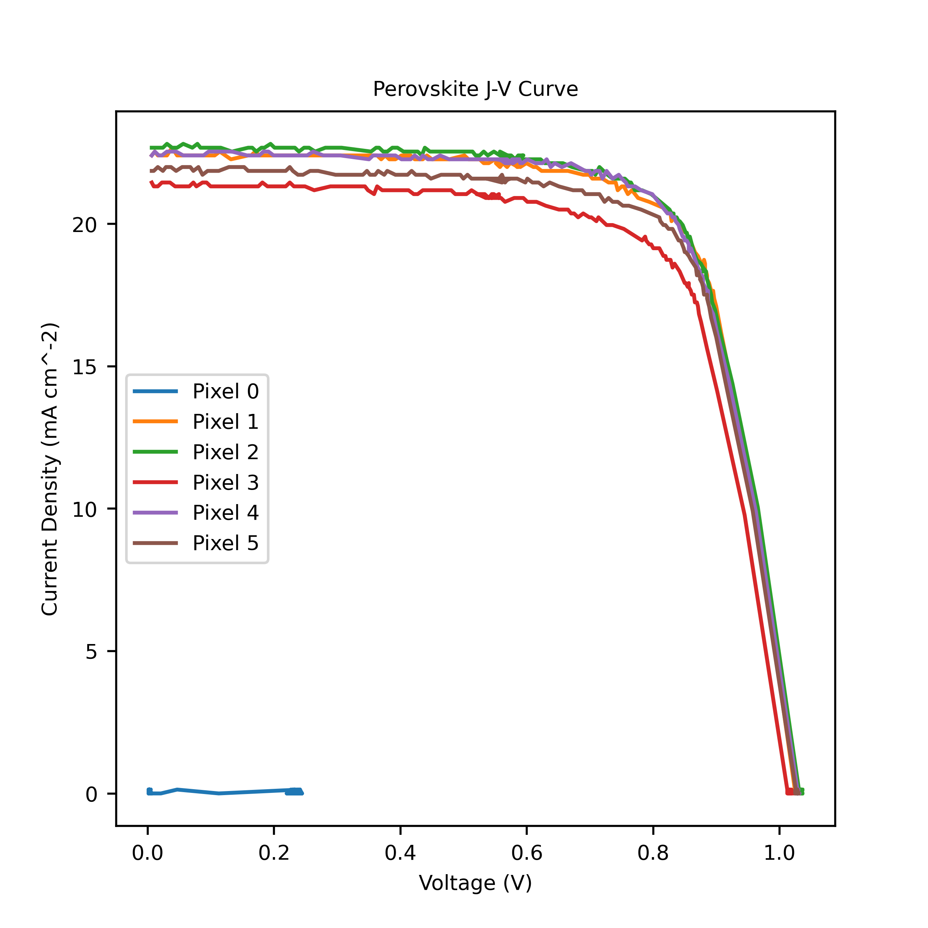
software/curves/2. Round Two/N003_08272023_LM/N003_08272023_LM_plotted.png
