Big-Red-Sat/Perovskite-Curve-Tracer/software/curves/2. Round Two/N003_08272023_LM_2/N003_08272023_LM_2_plotted.png

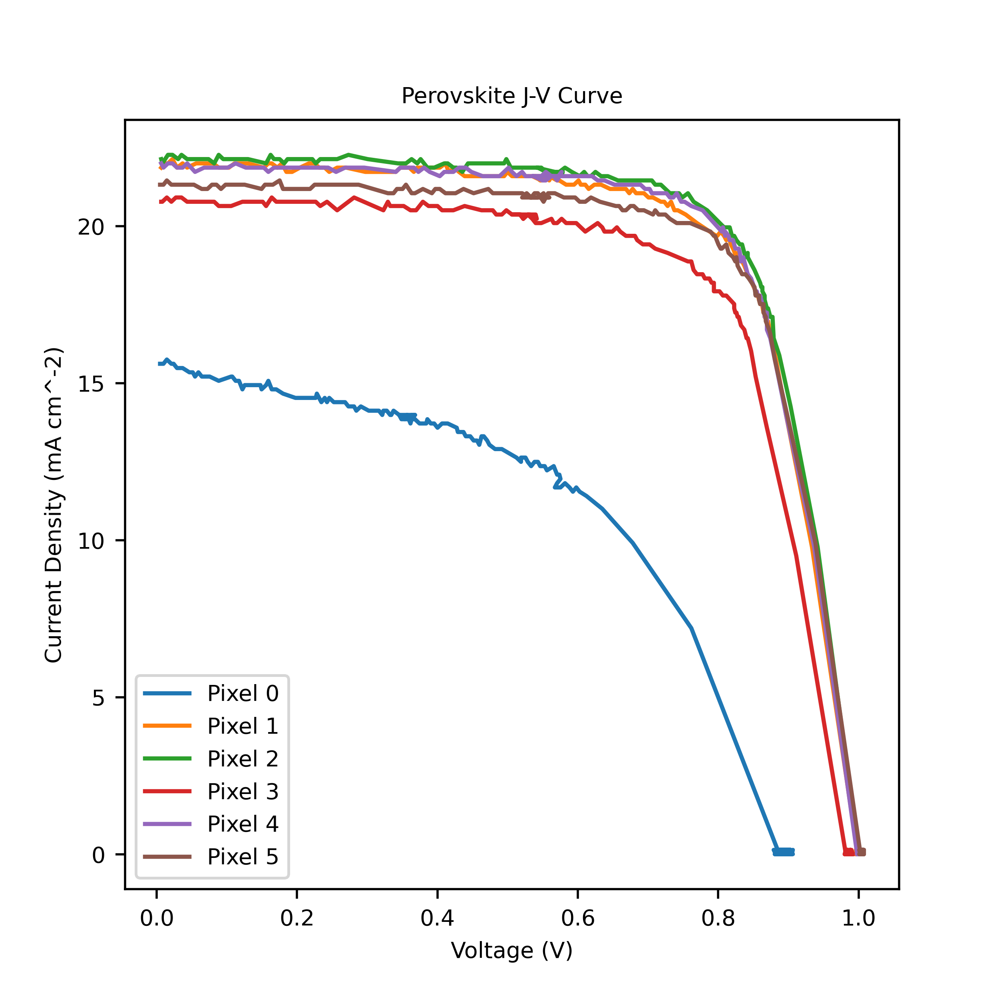
software/curves/2. Round Two/N003_08272023_LM_2/N003_08272023_LM_2_plotted.png
