Big-Red-Sat/Perovskite-Curve-Tracer/software/curves/2. Round Two/pogopinpostvibe/pogopinpostvibe_plotted.png

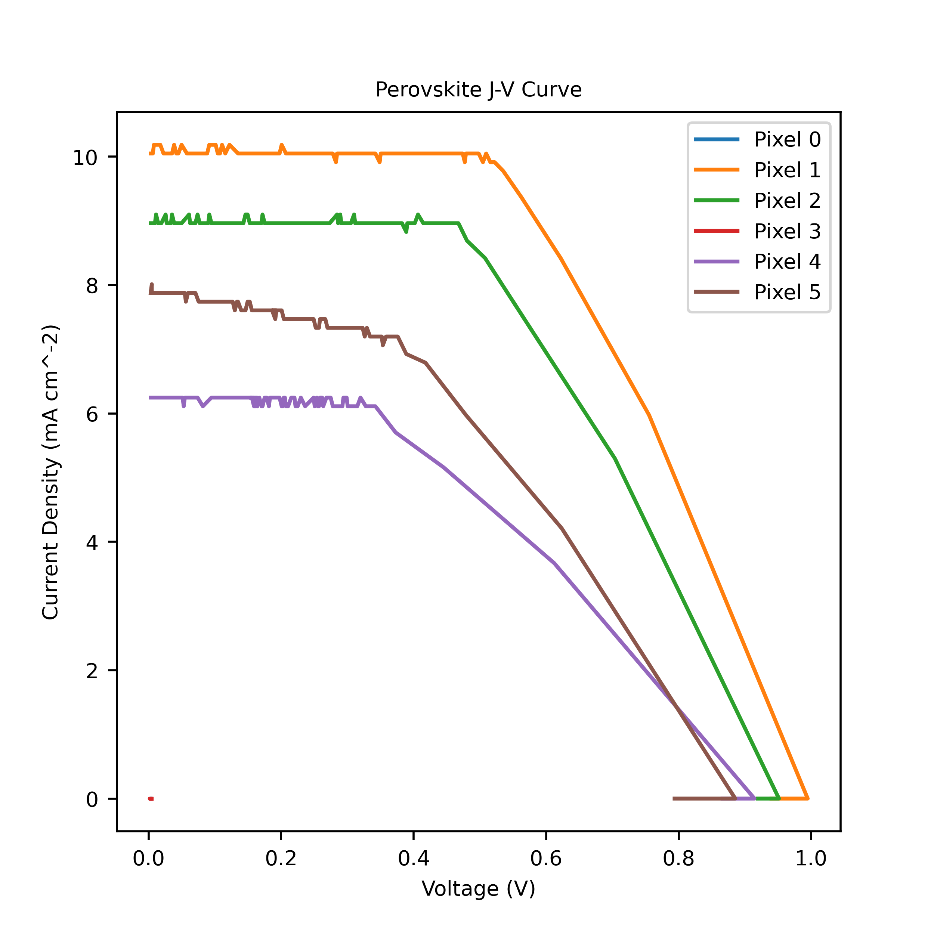
software/curves/2. Round Two/pogopinpostvibe/pogopinpostvibe_plotted.png
