Big-Red-Sat/Perovskite-Curve-Tracer/software/curves/2. Round Two/Pogopintest2/Pogopintest2_plotted.png

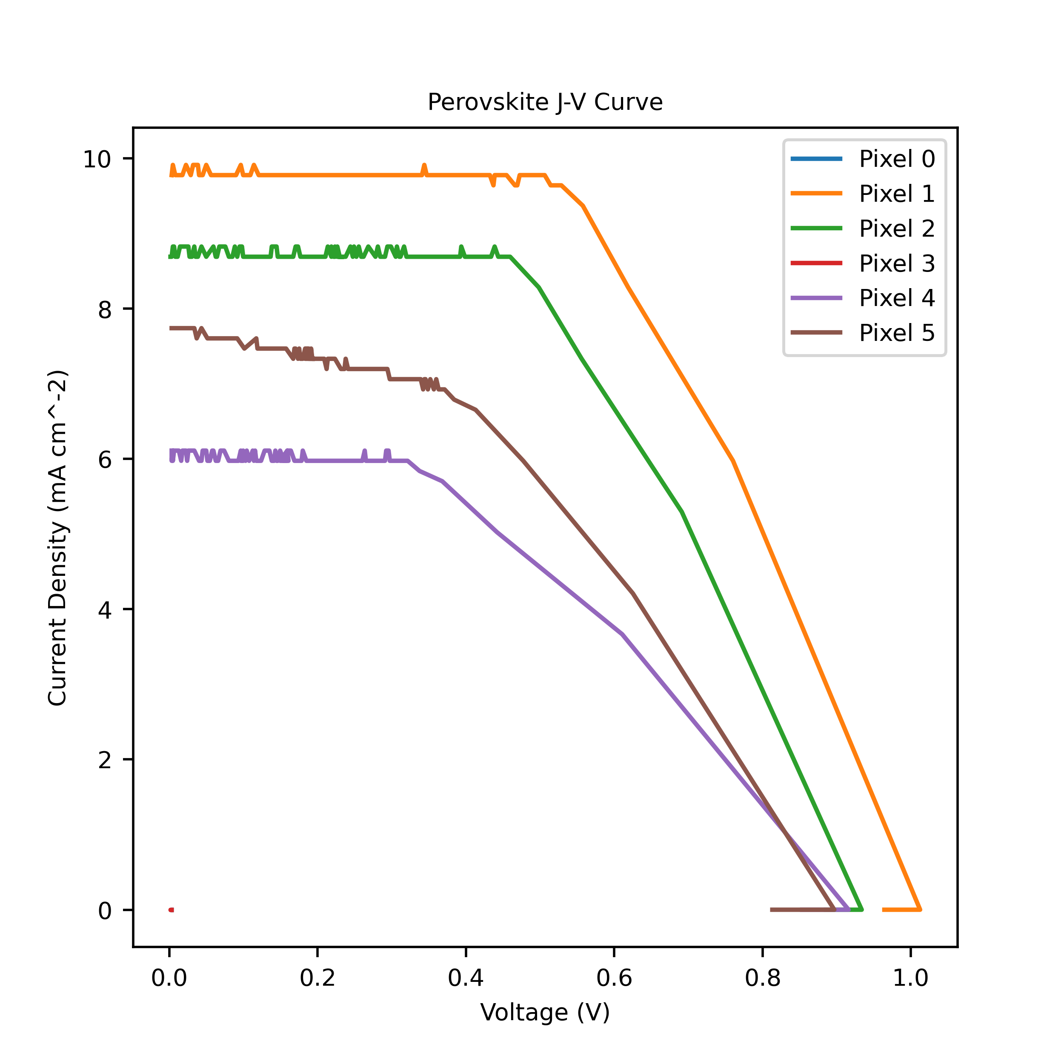
software/curves/2. Round Two/Pogopintest2/Pogopintest2_plotted.png
