Big-Red-Sat/Perovskite-Curve-Tracer/software/curves/2. Round Two/Pogopintest/Pogopintest_plotted.png

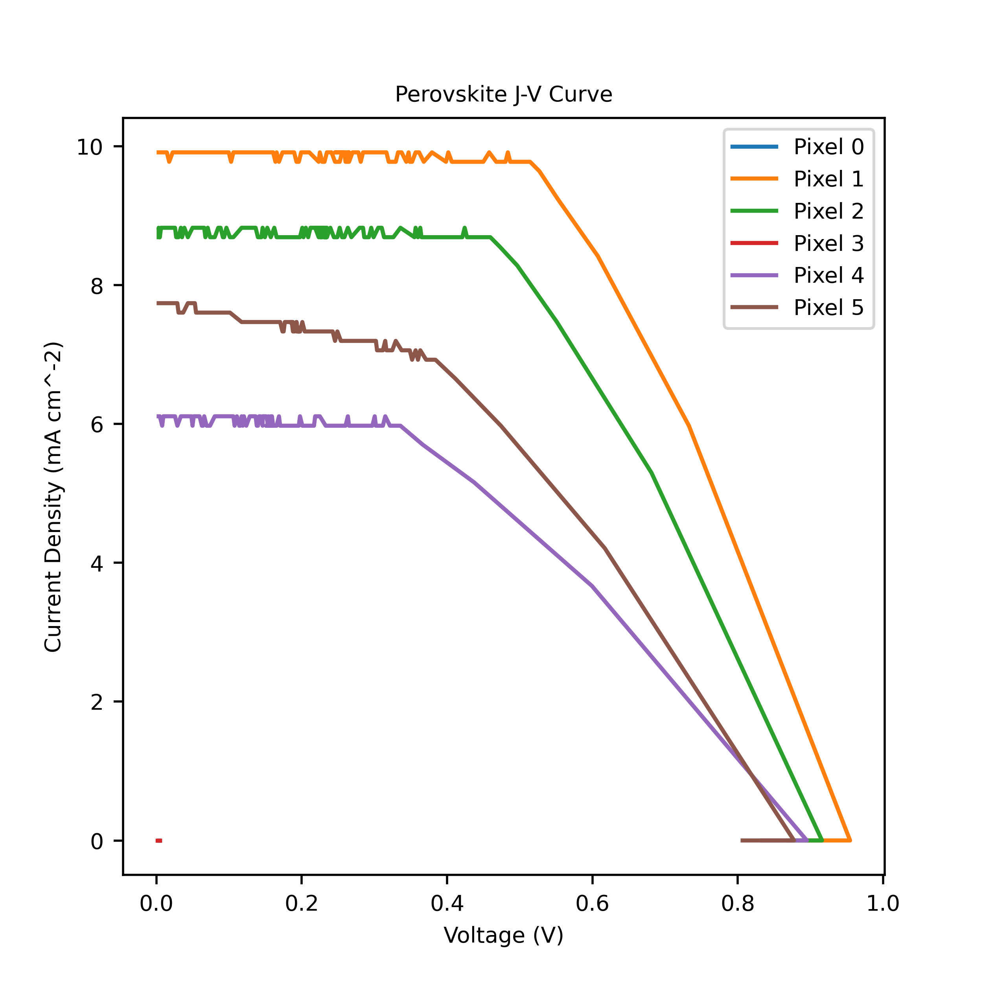
software/curves/2. Round Two/Pogopintest/Pogopintest_plotted.png
