Big-Red-Sat/Perovskite-Curve-Tracer/software/curves/2. Round Two/torque.3_GB_LM_A33/torque.3_GB_LM_A33_plotted_Reverse.png

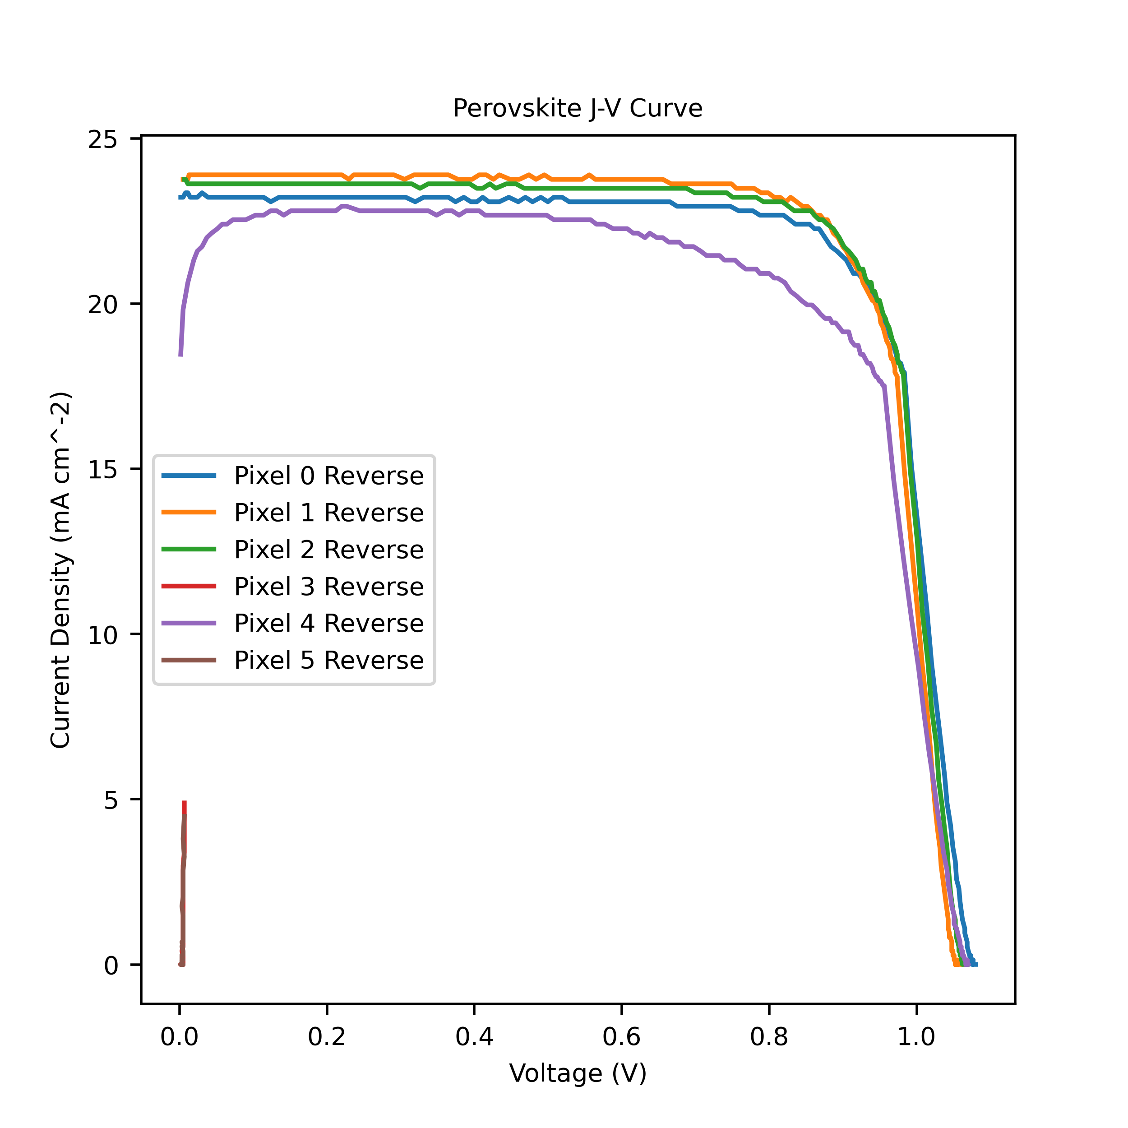
software/curves/2. Round Two/torque.3_GB_LM_A33/torque.3_GB_LM_A33_plotted_Reverse.png
