Big-Red-Sat/Perovskite-Curve-Tracer/software/curves/2. Round Two/torque.3_GB_LM_A48/torque.3_GB_LM_A48_plotted_Forward.png

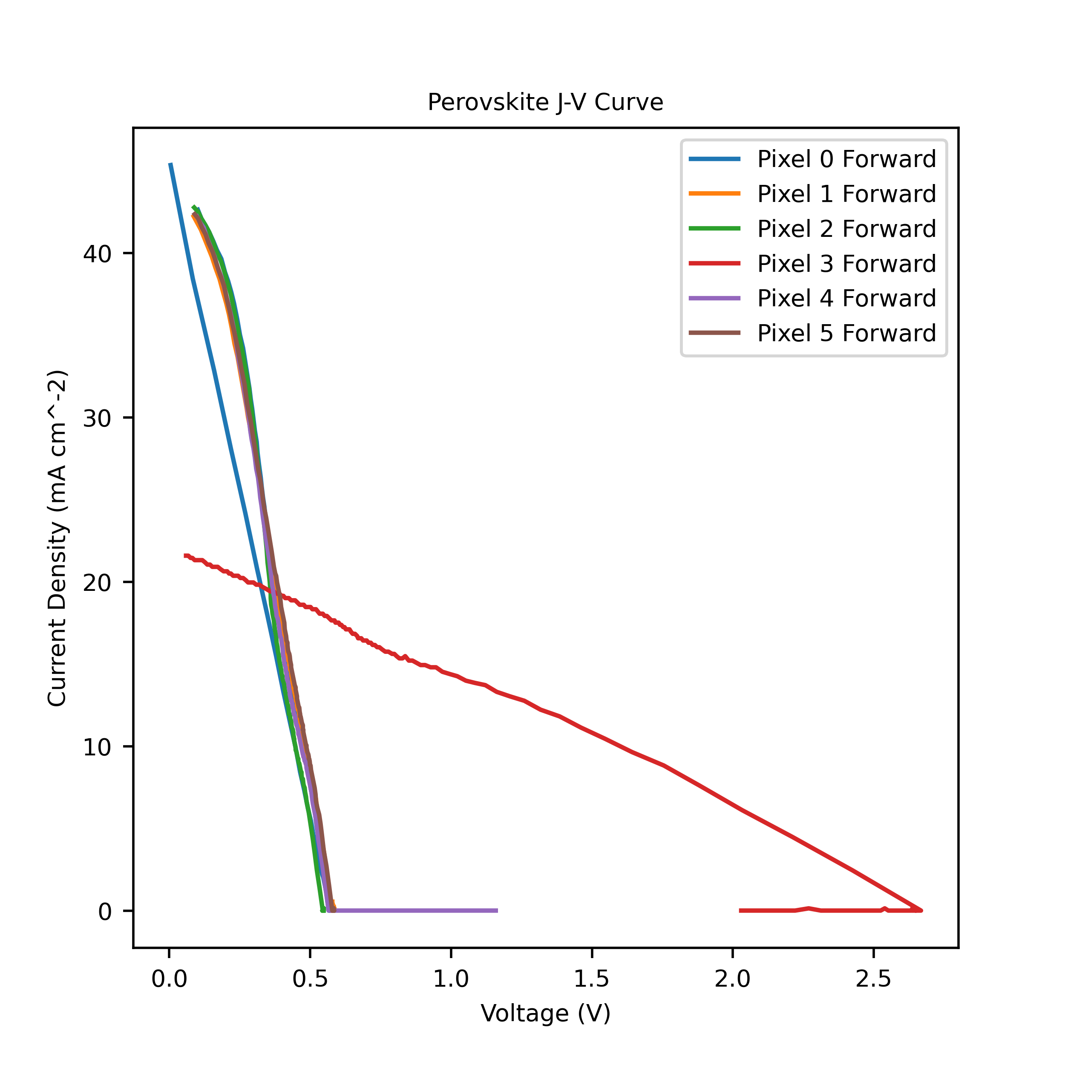
software/curves/2. Round Two/torque.3_GB_LM_A48/torque.3_GB_LM_A48_plotted_Forward.png
