Big-Red-Sat/Perovskite-Curve-Tracer/software/curves/2. Round Two/torque.7_GB_LM_A35/torque.7_GB_LM_A35_plotted_Reverse.png

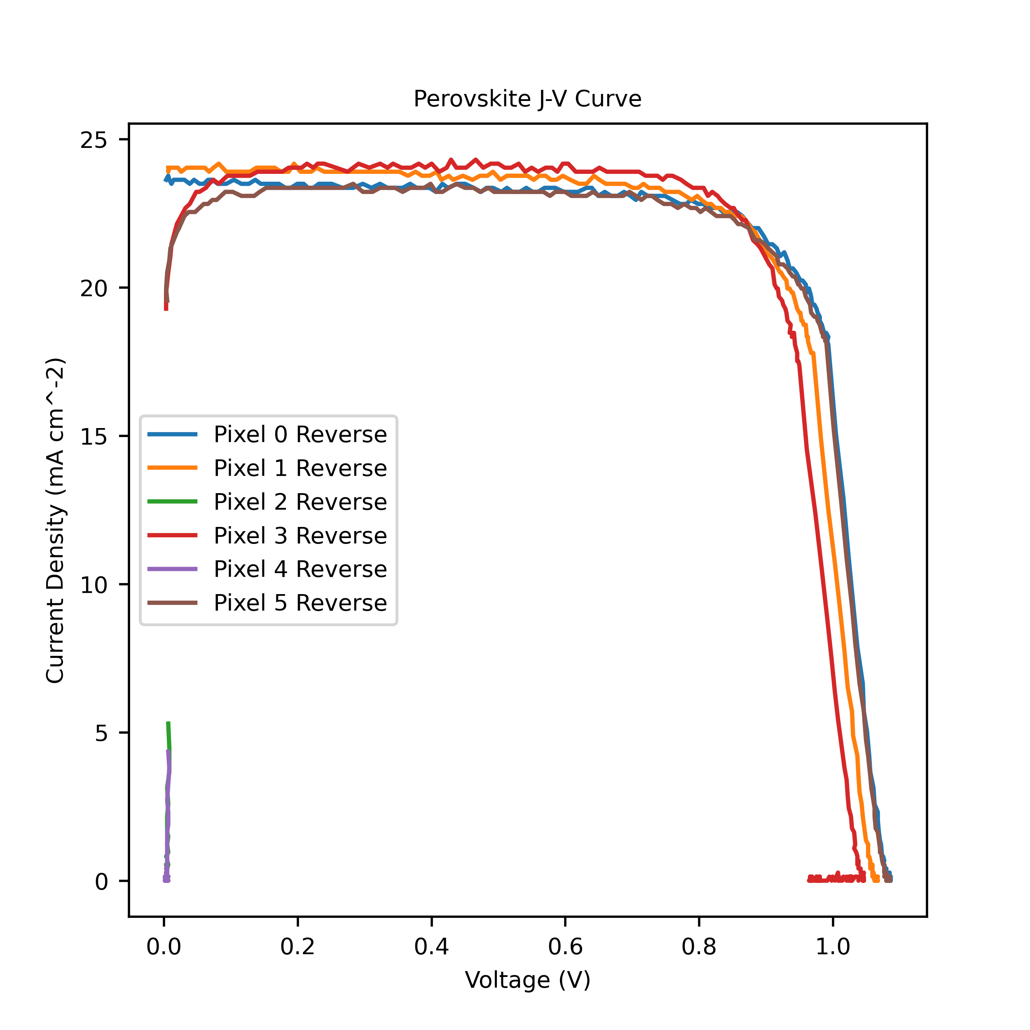
software/curves/2. Round Two/torque.7_GB_LM_A35/torque.7_GB_LM_A35_plotted_Reverse.png
