Big-Red-Sat/Perovskite-Curve-Tracer/software/curves/3. Final Round/X001_LM/X001_LM_plotted_Forward.png

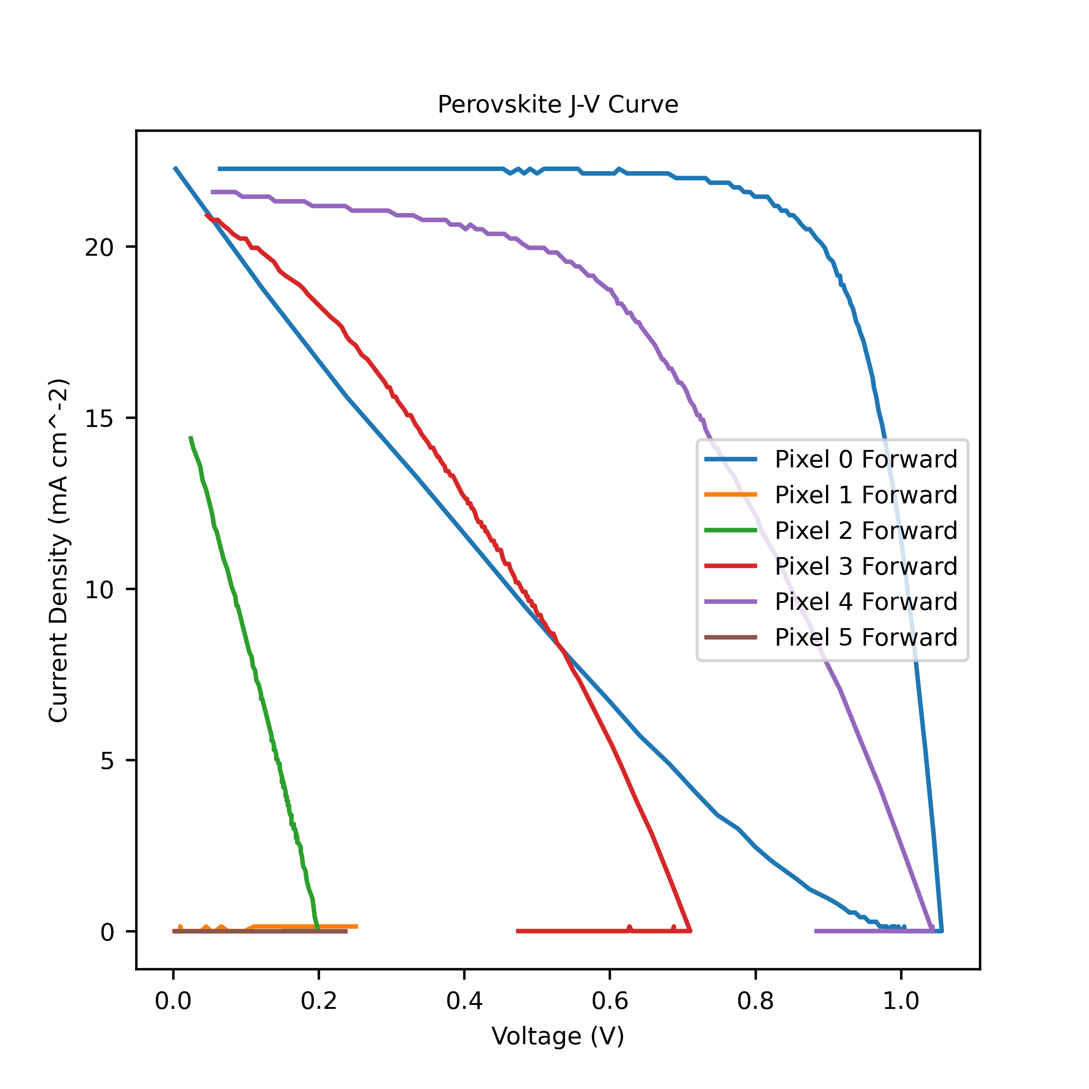
software/curves/3. Final Round/X001_LM/X001_LM_plotted_Forward.png
