Big-Red-Sat/Perovskite-Curve-Tracer/software/curves/3. Final Round/X001_LM/X001_LM_plotted_Reverse.png

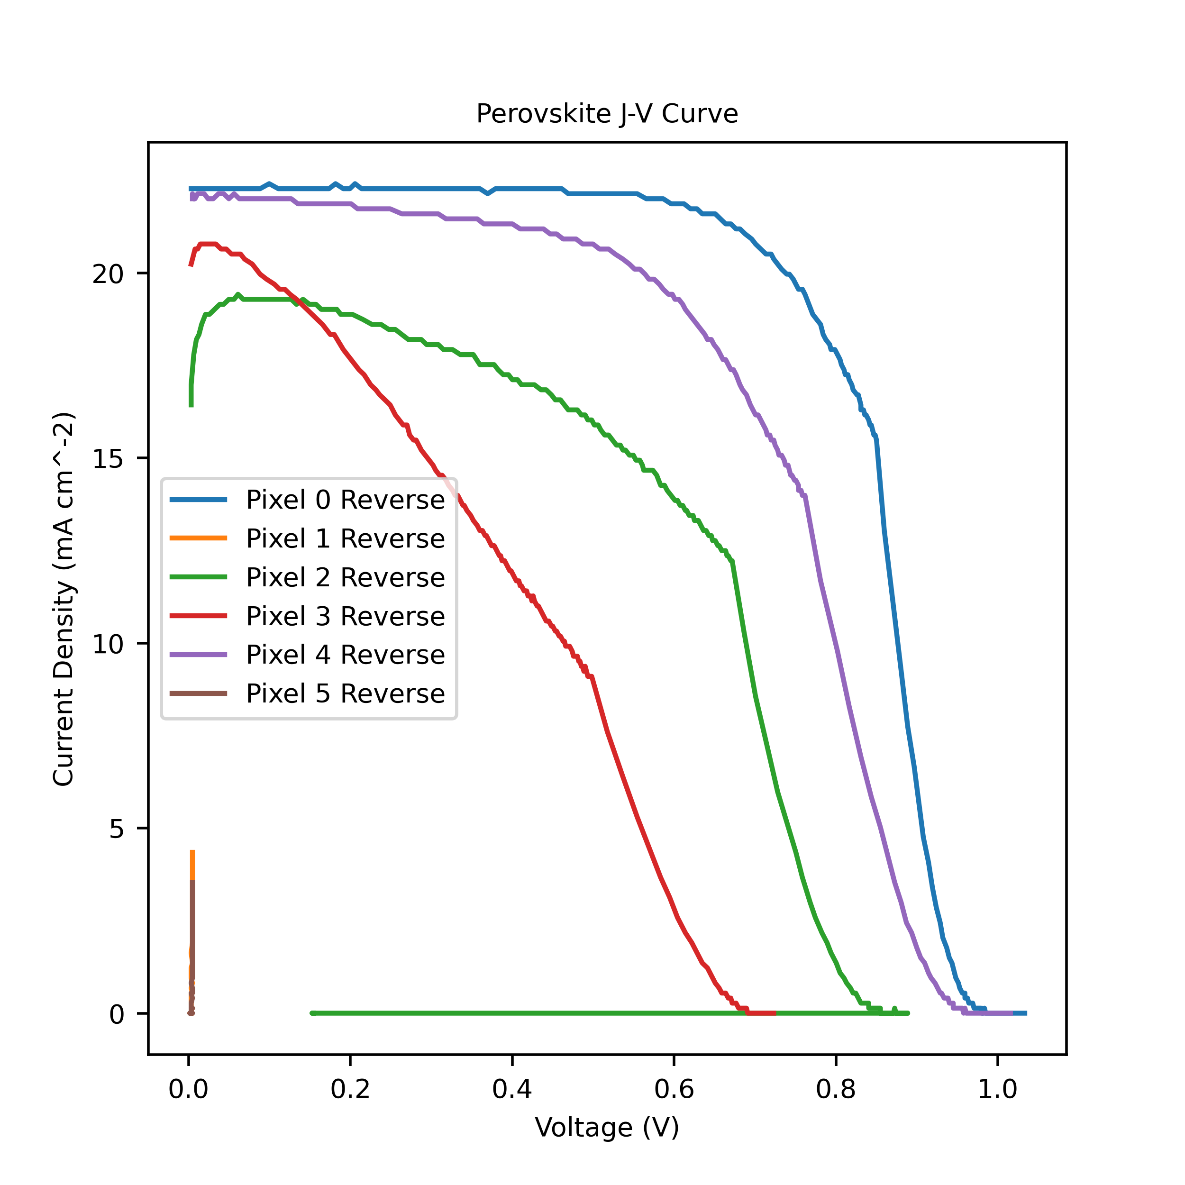
software/curves/3. Final Round/X001_LM/X001_LM_plotted_Reverse.png
