Big-Red-Sat/Perovskite-Curve-Tracer/software/curves/3. Final Round/X002_LM/X002_LM_plotted_Forward.png

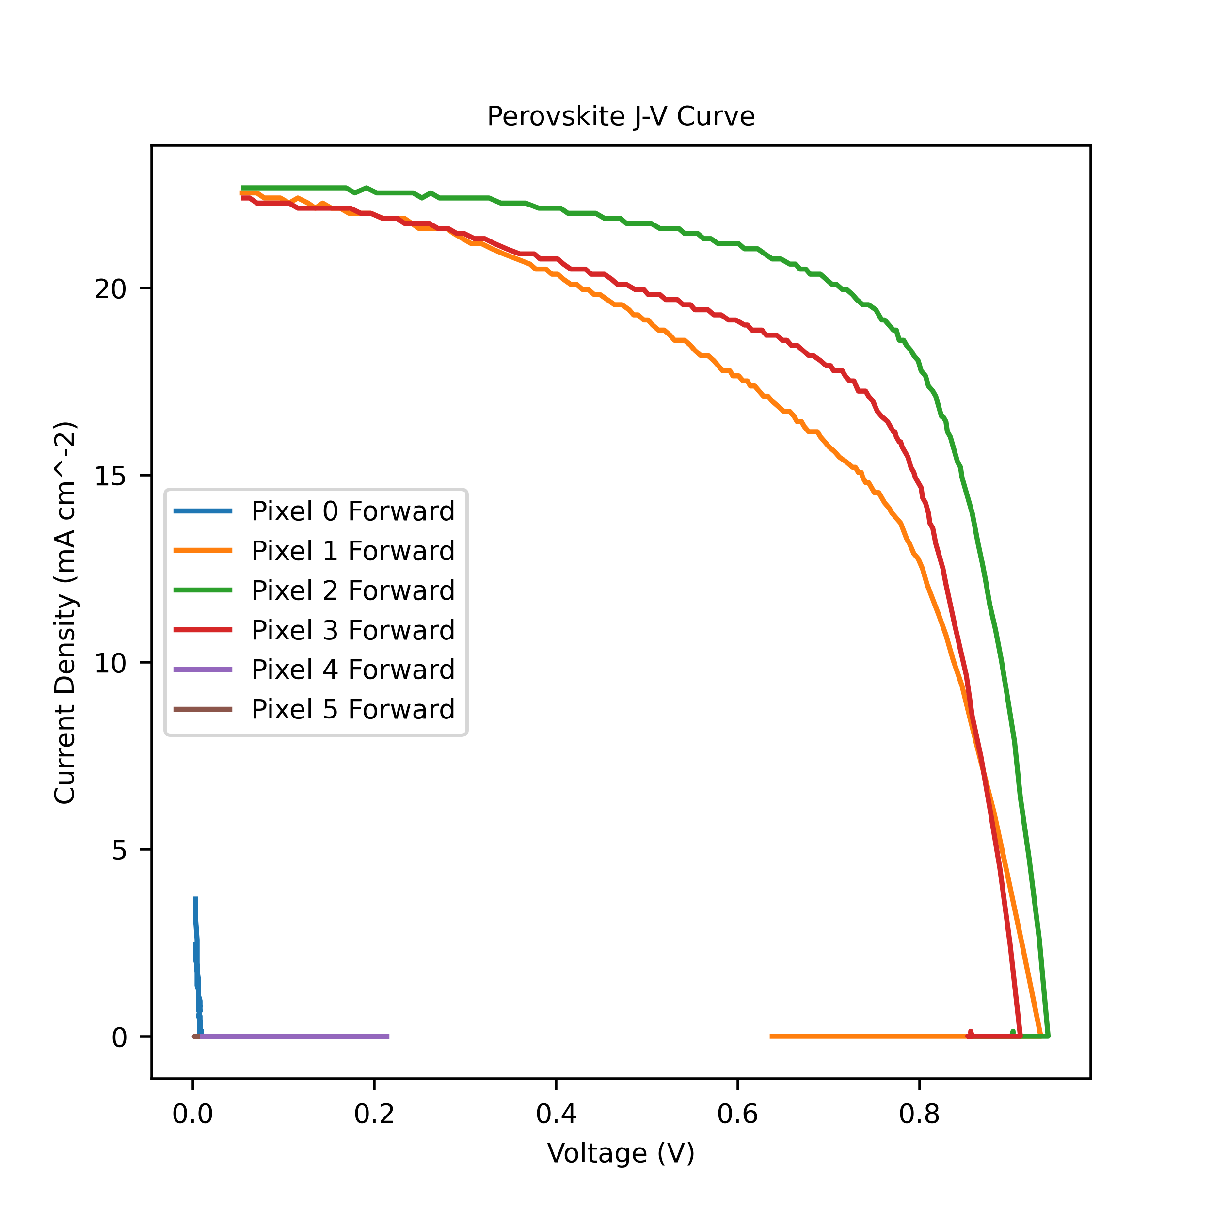
software/curves/3. Final Round/X002_LM/X002_LM_plotted_Forward.png
