Big-Red-Sat/Perovskite-Curve-Tracer/software/curves/3. Final Round/X002_LM/X002_LM_plotted_Reverse.png

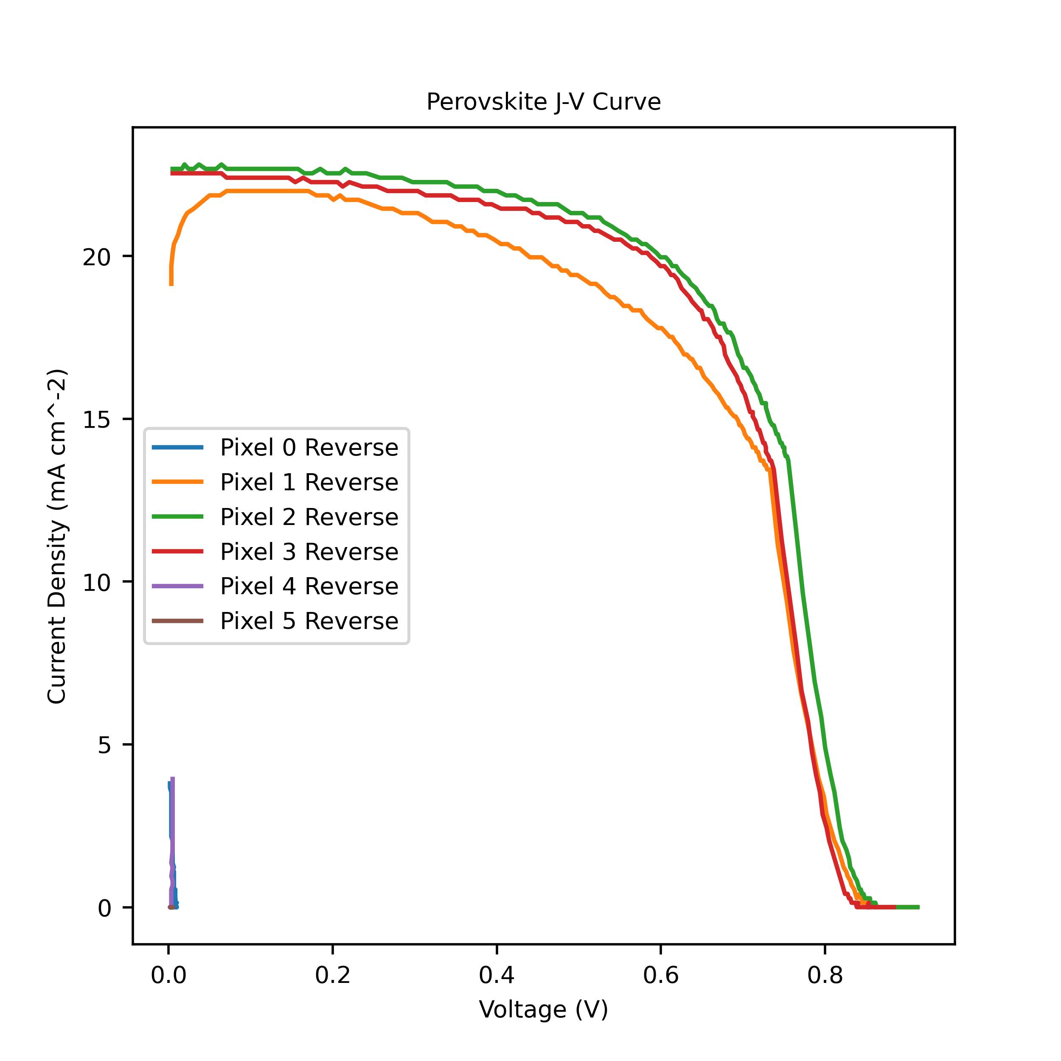
software/curves/3. Final Round/X002_LM/X002_LM_plotted_Reverse.png
