Big-Red-Sat/Perovskite-Curve-Tracer/software/curves/3. Final Round/X005_LM/X---_LM_plotted_Reverse.png

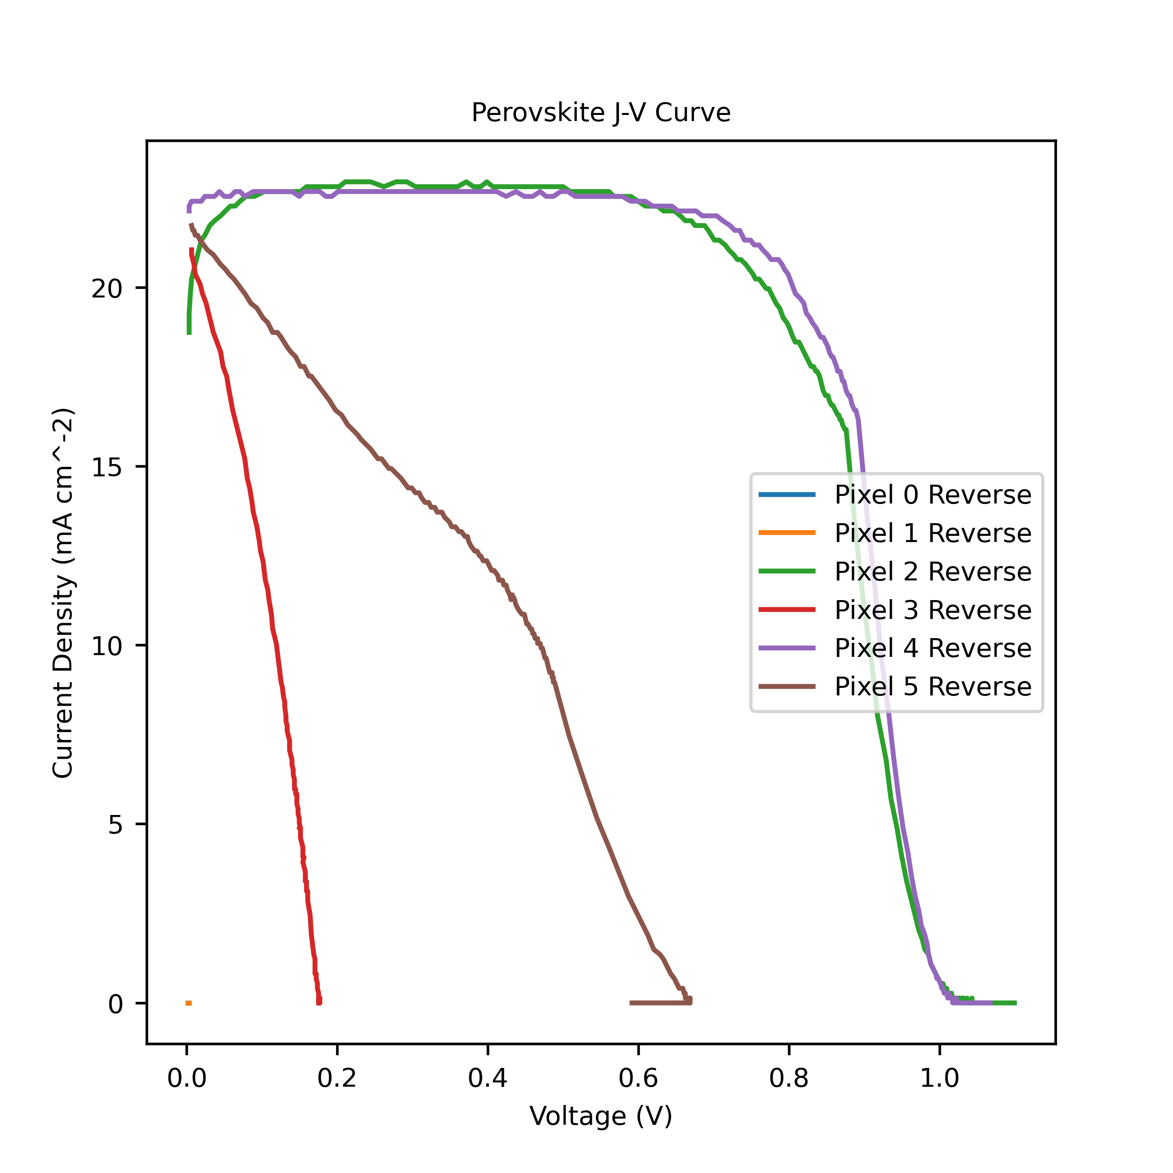
software/curves/3. Final Round/X005_LM/X---_LM_plotted_Reverse.png
