Big-Red-Sat/Perovskite-Curve-Tracer/software/curves/3. Final Round/X006_LM/X006_LM_plotted_Reverse.png

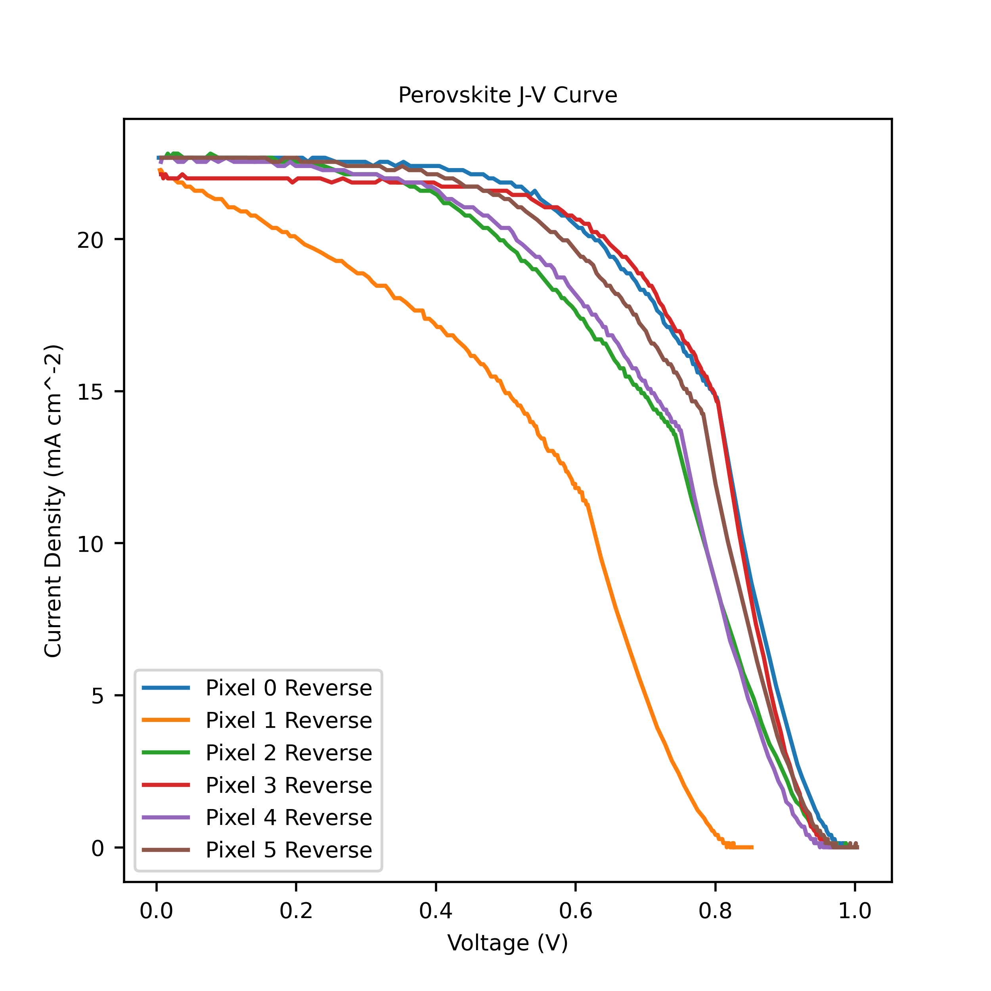
software/curves/3. Final Round/X006_LM/X006_LM_plotted_Reverse.png
