Big-Red-Sat/Perovskite-Curve-Tracer/software/curves/3. Final Round/X007_LM/X007_LM_plotted_Forward.png

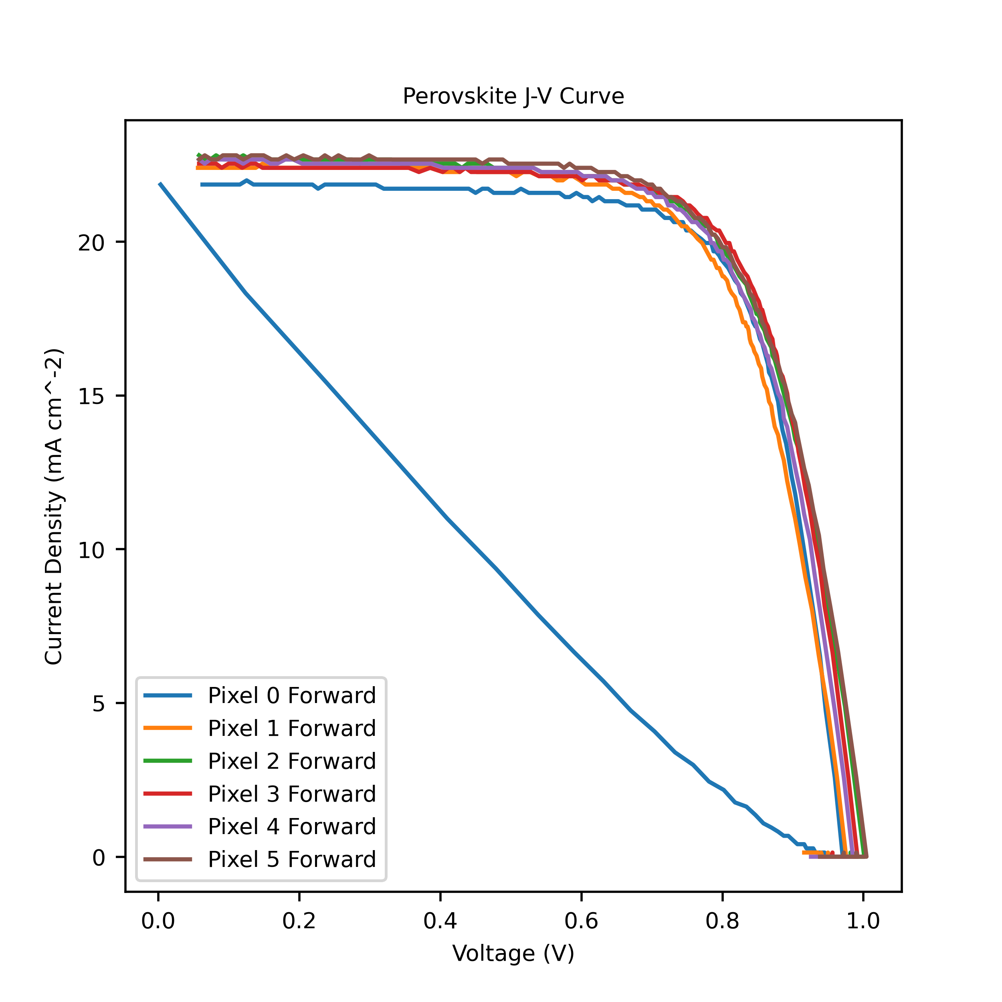
software/curves/3. Final Round/X007_LM/X007_LM_plotted_Forward.png
