Big-Red-Sat/Perovskite-Curve-Tracer/software/curves/3. Final Round/X008_LM/X008_LM_plotted_Reverse.png

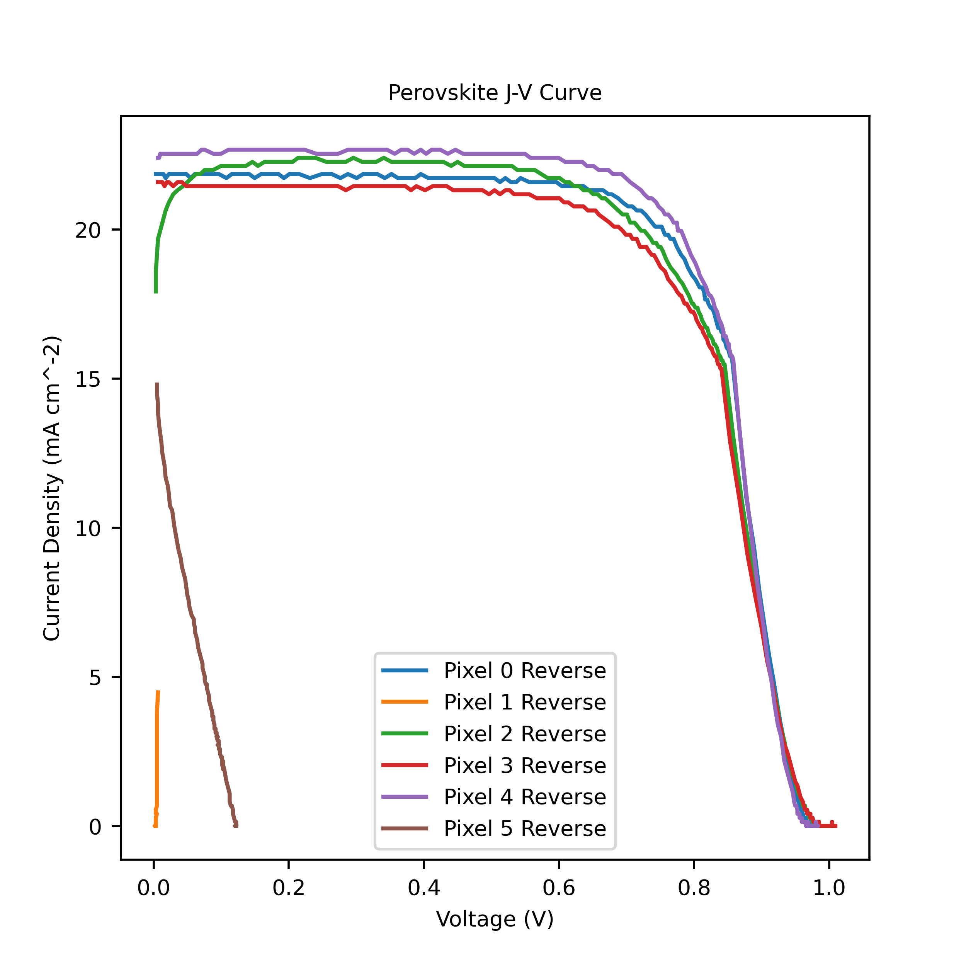
software/curves/3. Final Round/X008_LM/X008_LM_plotted_Reverse.png
