Big-Red-Sat/Perovskite-Curve-Tracer/software/curves/3. Final Round/X009_LM/X009_LM_plotted_Forward.png

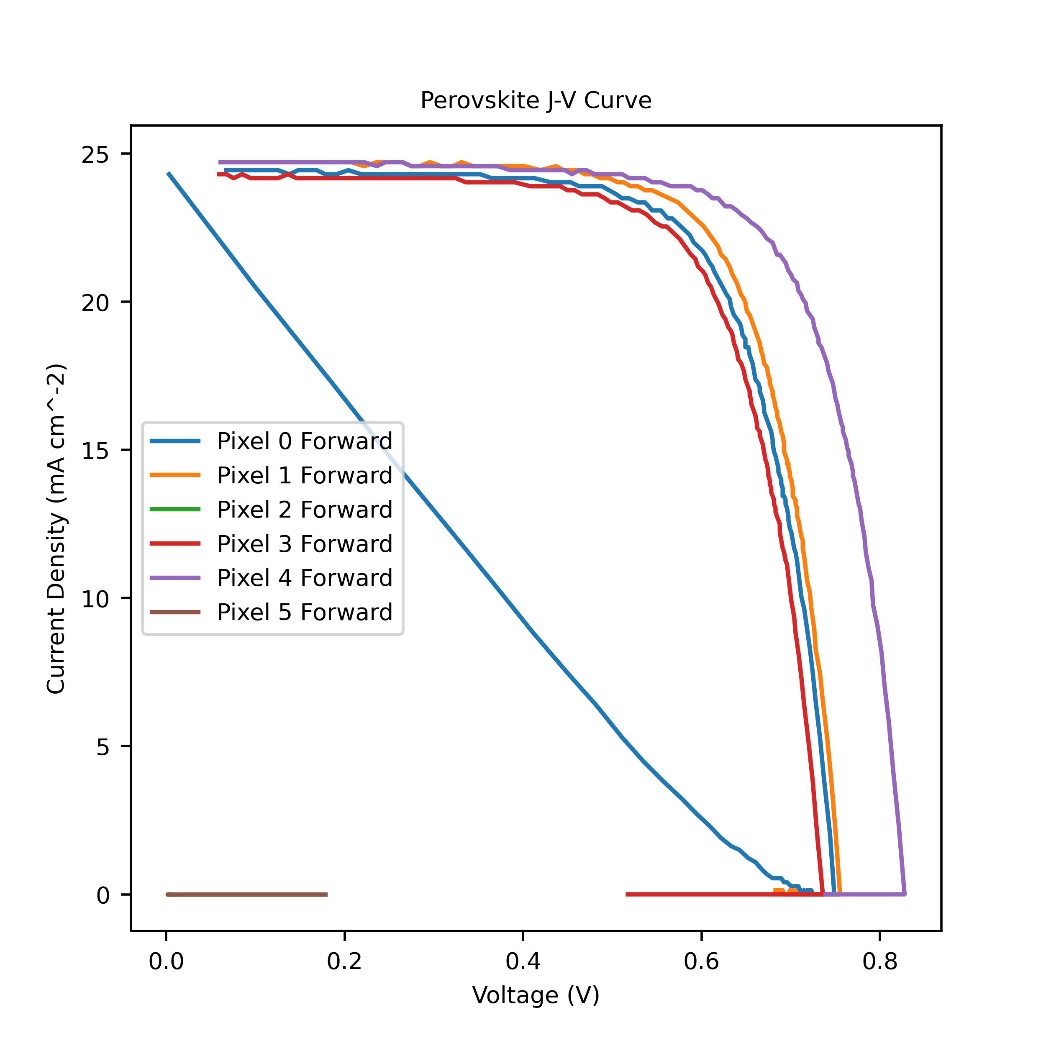
software/curves/3. Final Round/X009_LM/X009_LM_plotted_Forward.png
