Big-Red-Sat/Perovskite-Curve-Tracer/software/curves/3. Final Round/X009_LM/X009_LM_plotted_Reverse.png

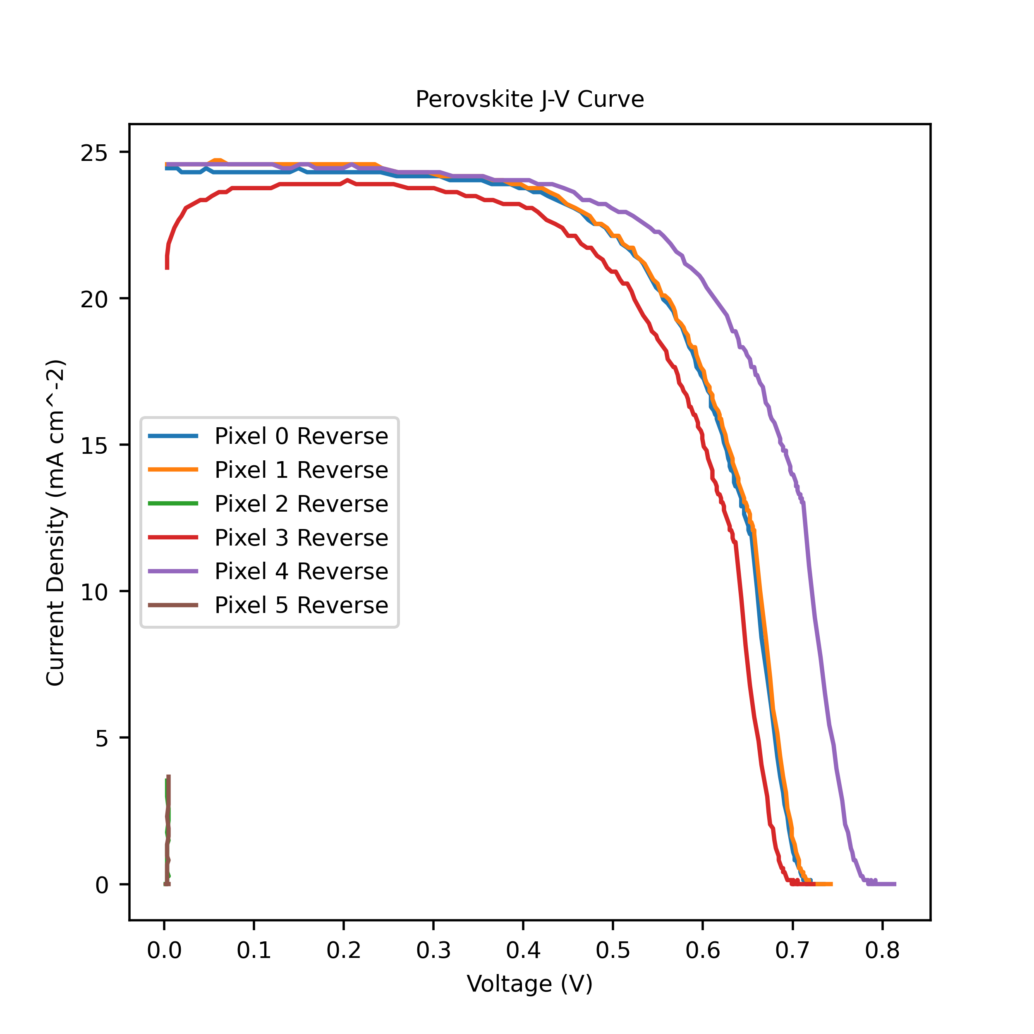
software/curves/3. Final Round/X009_LM/X009_LM_plotted_Reverse.png
