Big-Red-Sat/Perovskite-Curve-Tracer/software/curves/3. Final Round/X010_LM/X010_LM_plotted_Reverse.png

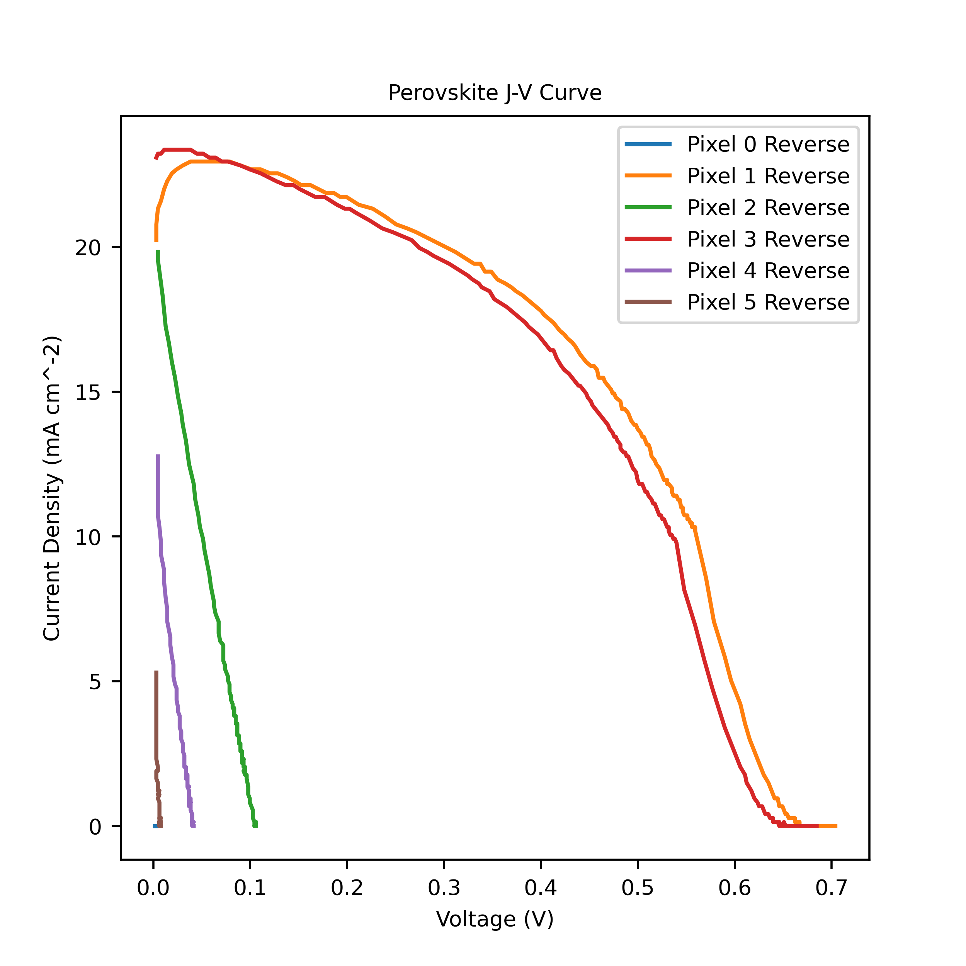
software/curves/3. Final Round/X010_LM/X010_LM_plotted_Reverse.png
