Big-Red-Sat/Perovskite-Curve-Tracer/software/curves/3. Final Round/X012_LM/X012_LM_plotted_Reverse.png

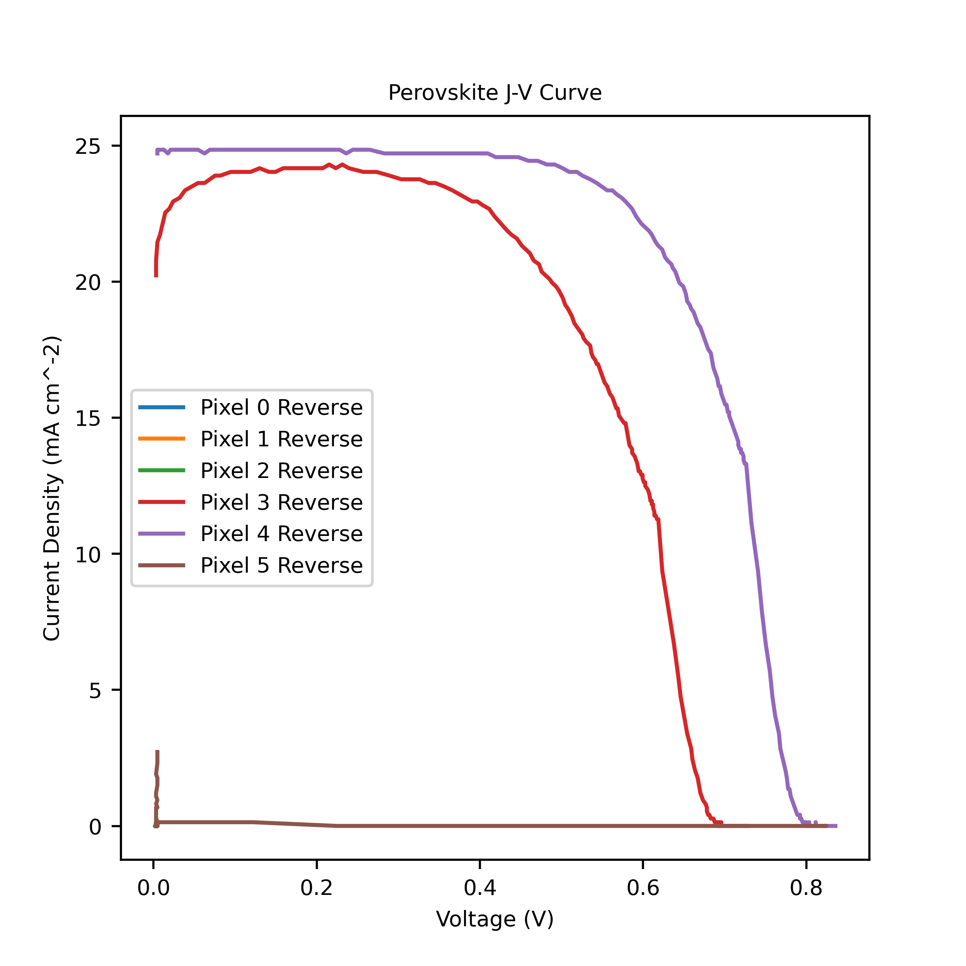
software/curves/3. Final Round/X012_LM/X012_LM_plotted_Reverse.png
