Big-Red-Sat/Perovskite-Curve-Tracer/software/curves/3. Final Round/X013_LM/X013_LM_plotted_Forward.png

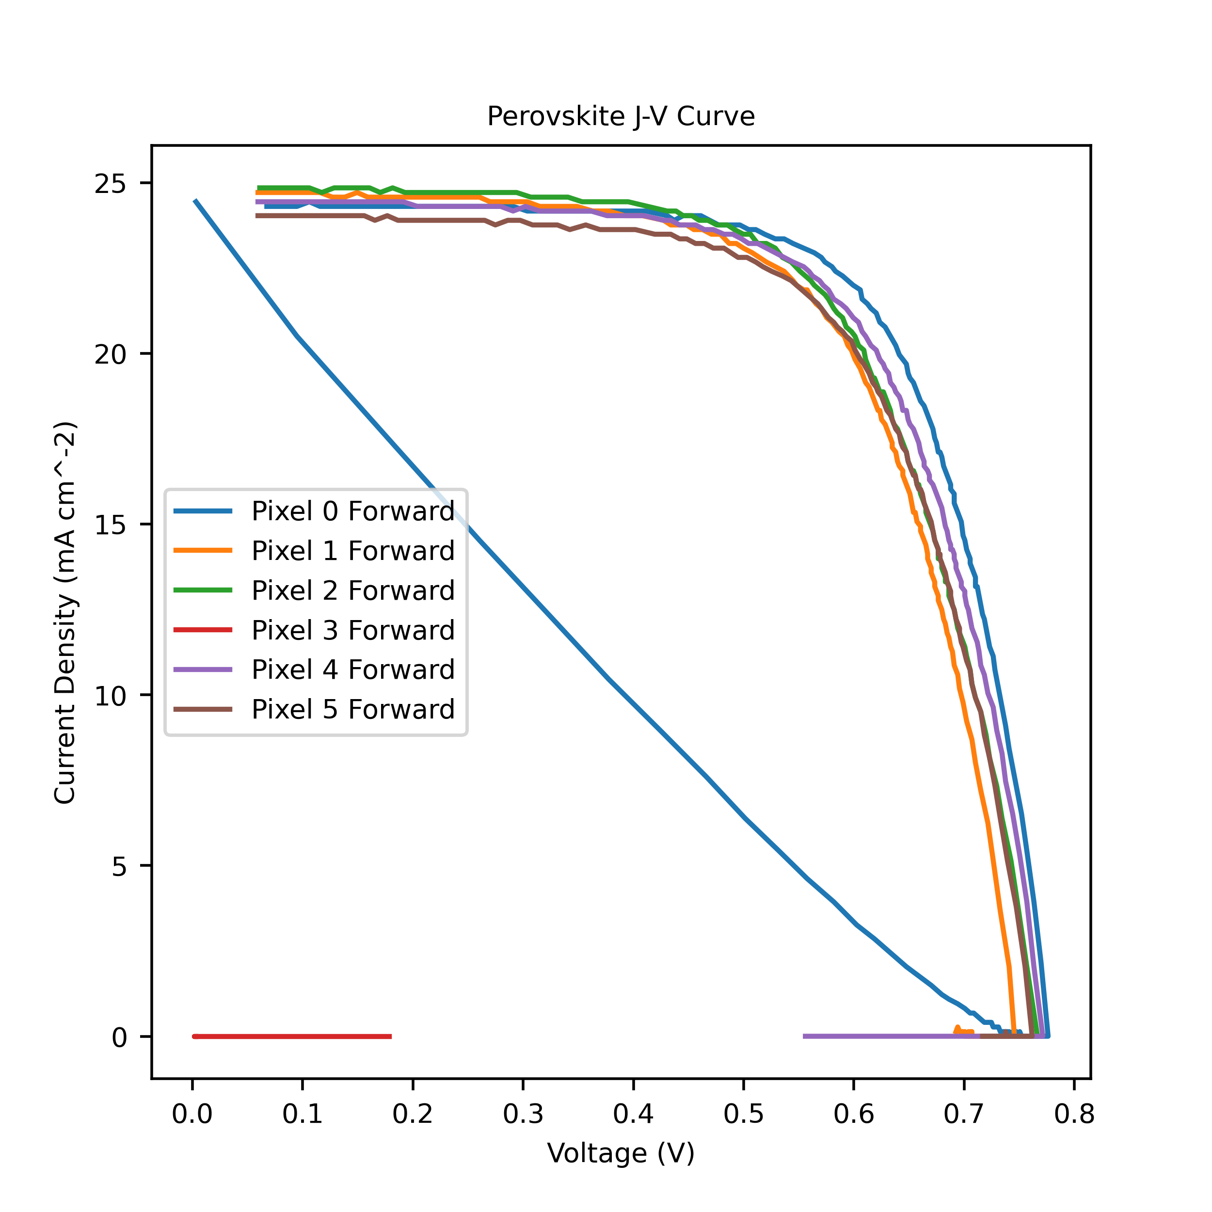
software/curves/3. Final Round/X013_LM/X013_LM_plotted_Forward.png
