Big-Red-Sat/Perovskite-Curve-Tracer/software/curves/3. Final Round/X015_LM/X---_LM_plotted_Forward.png

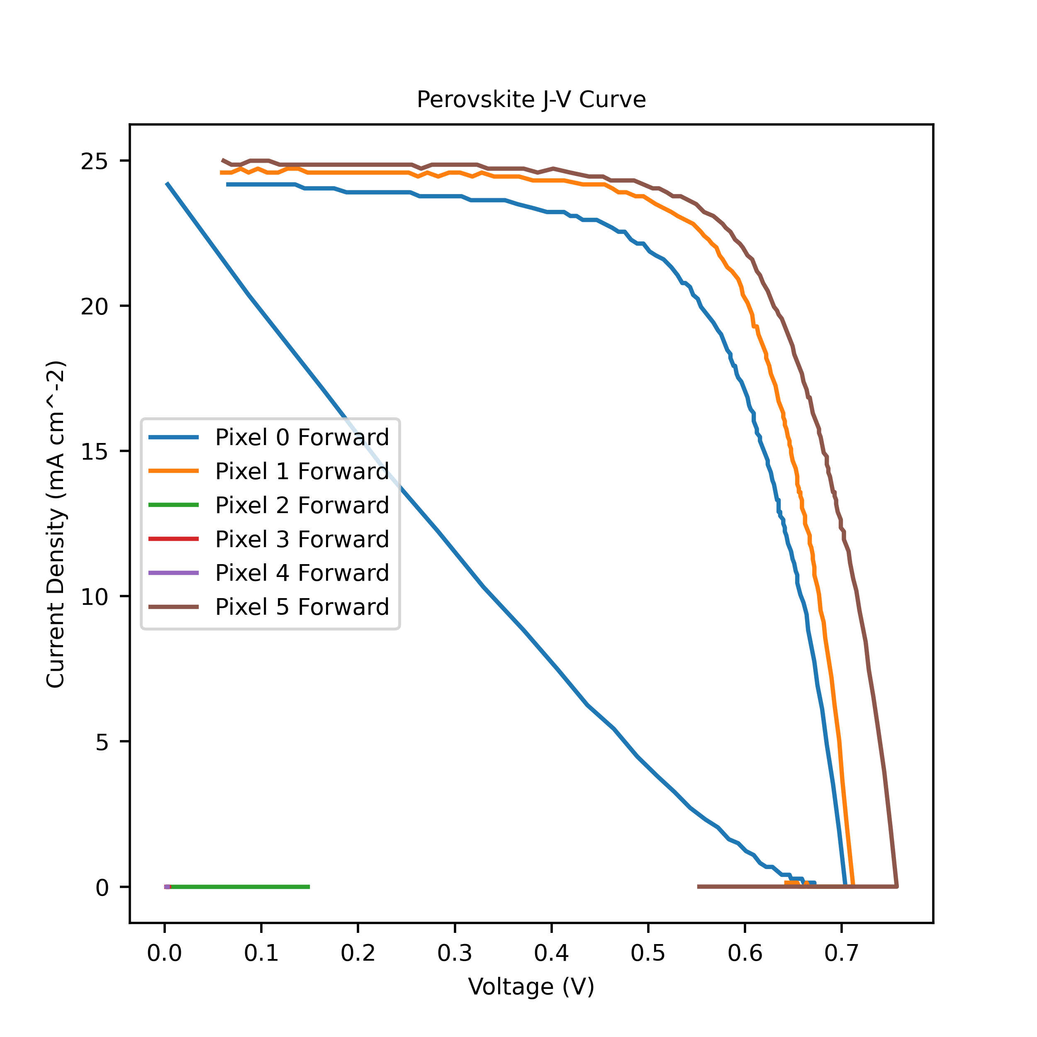
software/curves/3. Final Round/X015_LM/X---_LM_plotted_Forward.png
