Big-Red-Sat/Perovskite-Curve-Tracer/software/curves/3. Final Round/X016_LM/X016_LM_plotted_Reverse.png

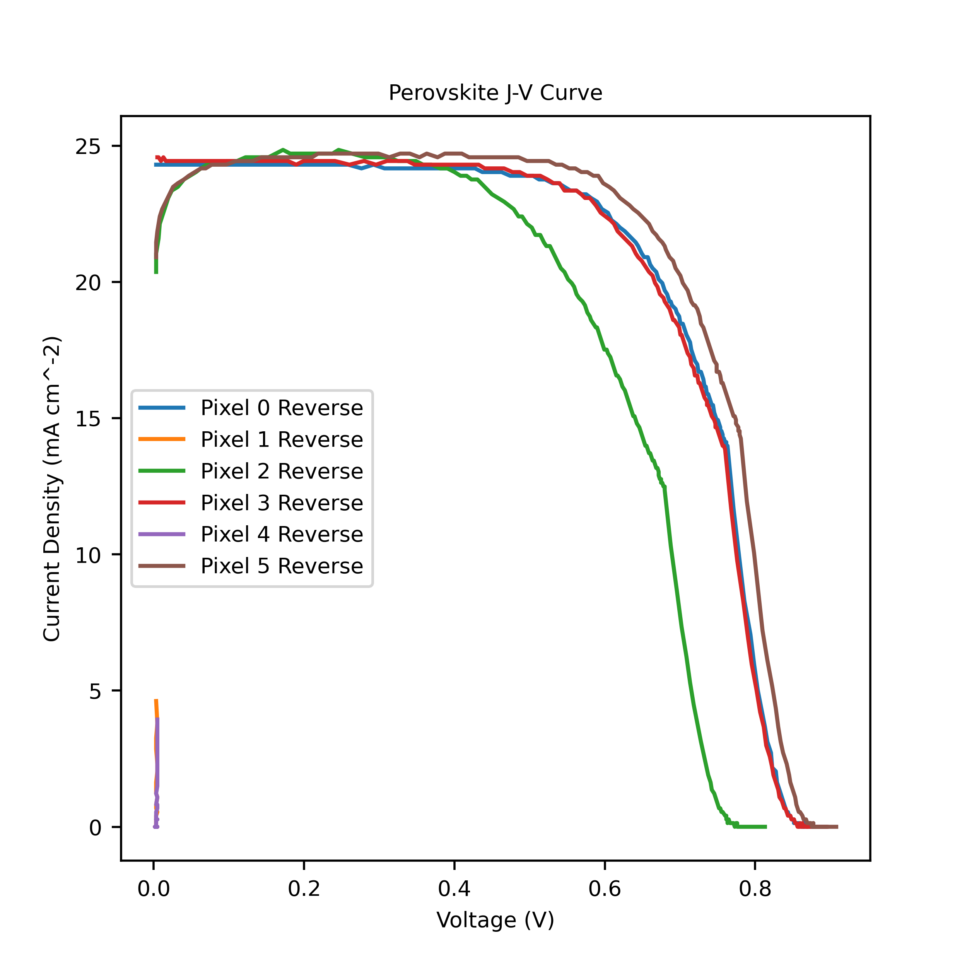
software/curves/3. Final Round/X016_LM/X016_LM_plotted_Reverse.png
