Big-Red-Sat/Perovskite-Curve-Tracer/software/curves/3. Final Round/X020_LM/X020_LM_plotted_Forward.png

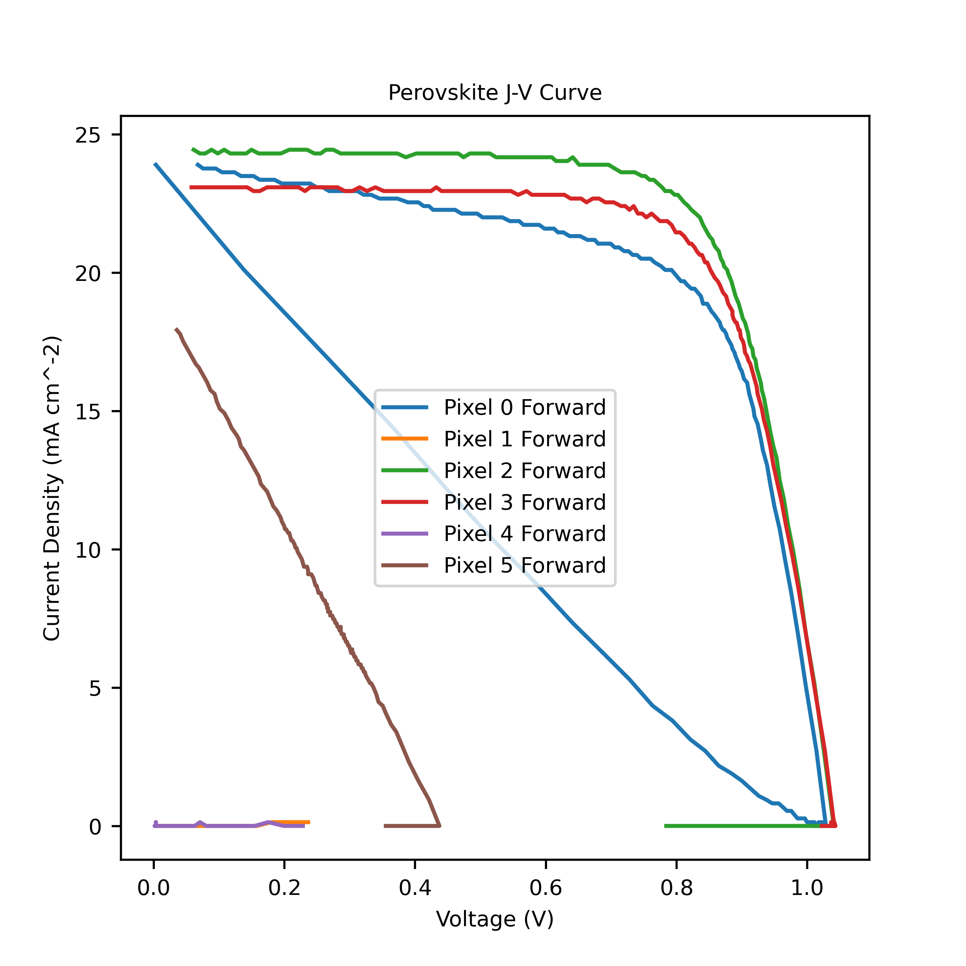
software/curves/3. Final Round/X020_LM/X020_LM_plotted_Forward.png
