Big-Red-Sat/Perovskite-Curve-Tracer/software/curves/3. Final Round/X020_LM/X020_LM_plotted_Reverse.png

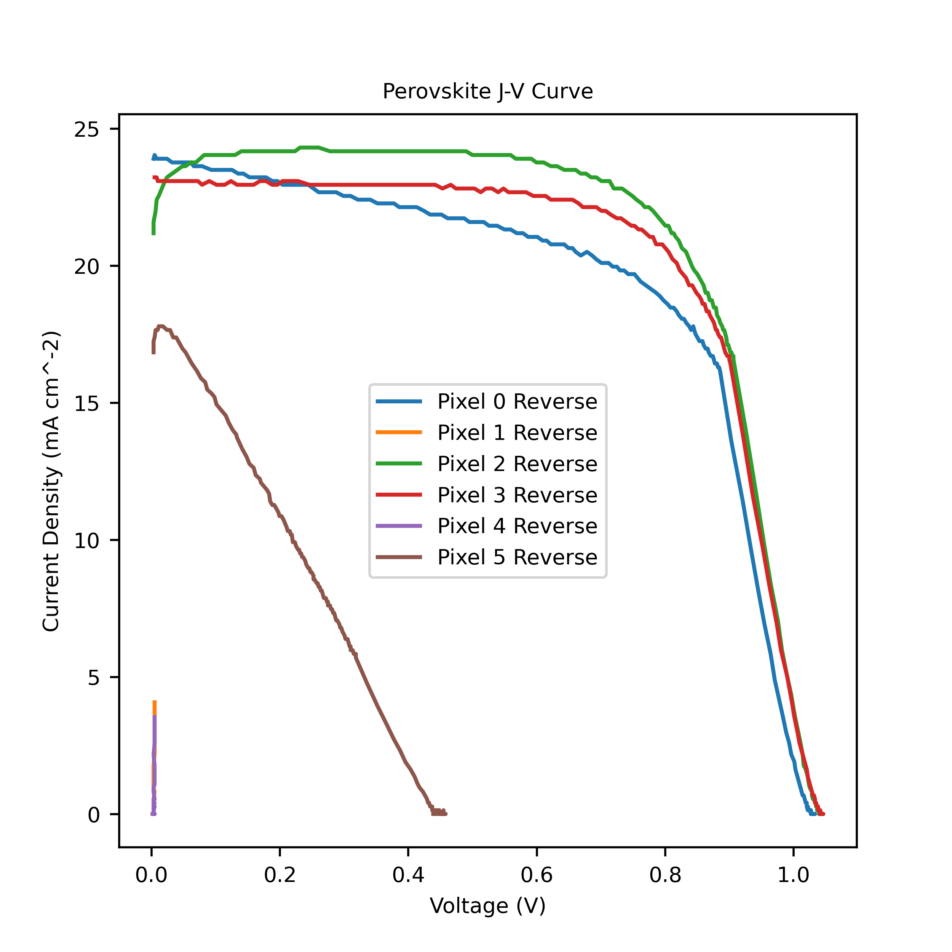
software/curves/3. Final Round/X020_LM/X020_LM_plotted_Reverse.png
