Big-Red-Sat/Perovskite-Curve-Tracer/software/curves/3. Final Round/X023_LM/X023_LM_plotted_Forward.png

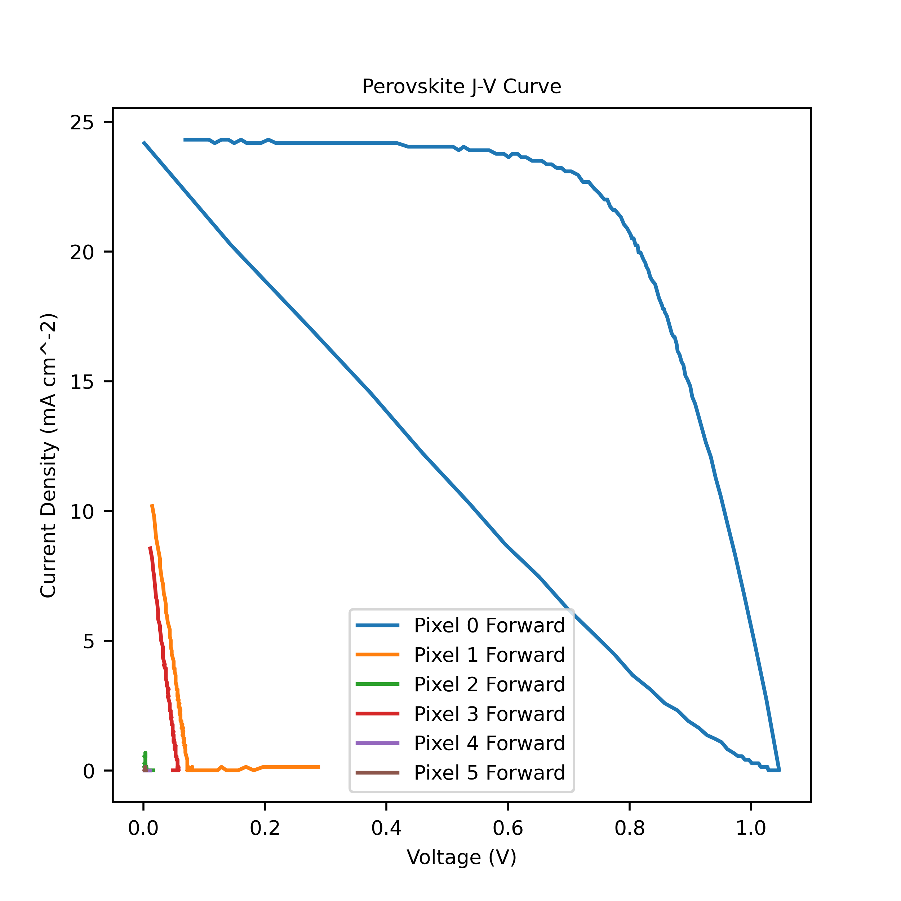
software/curves/3. Final Round/X023_LM/X023_LM_plotted_Forward.png
