Big-Red-Sat/Perovskite-Curve-Tracer/software/curves/3. Final Round/X023_LM/X023_LM_plotted_Reverse.png

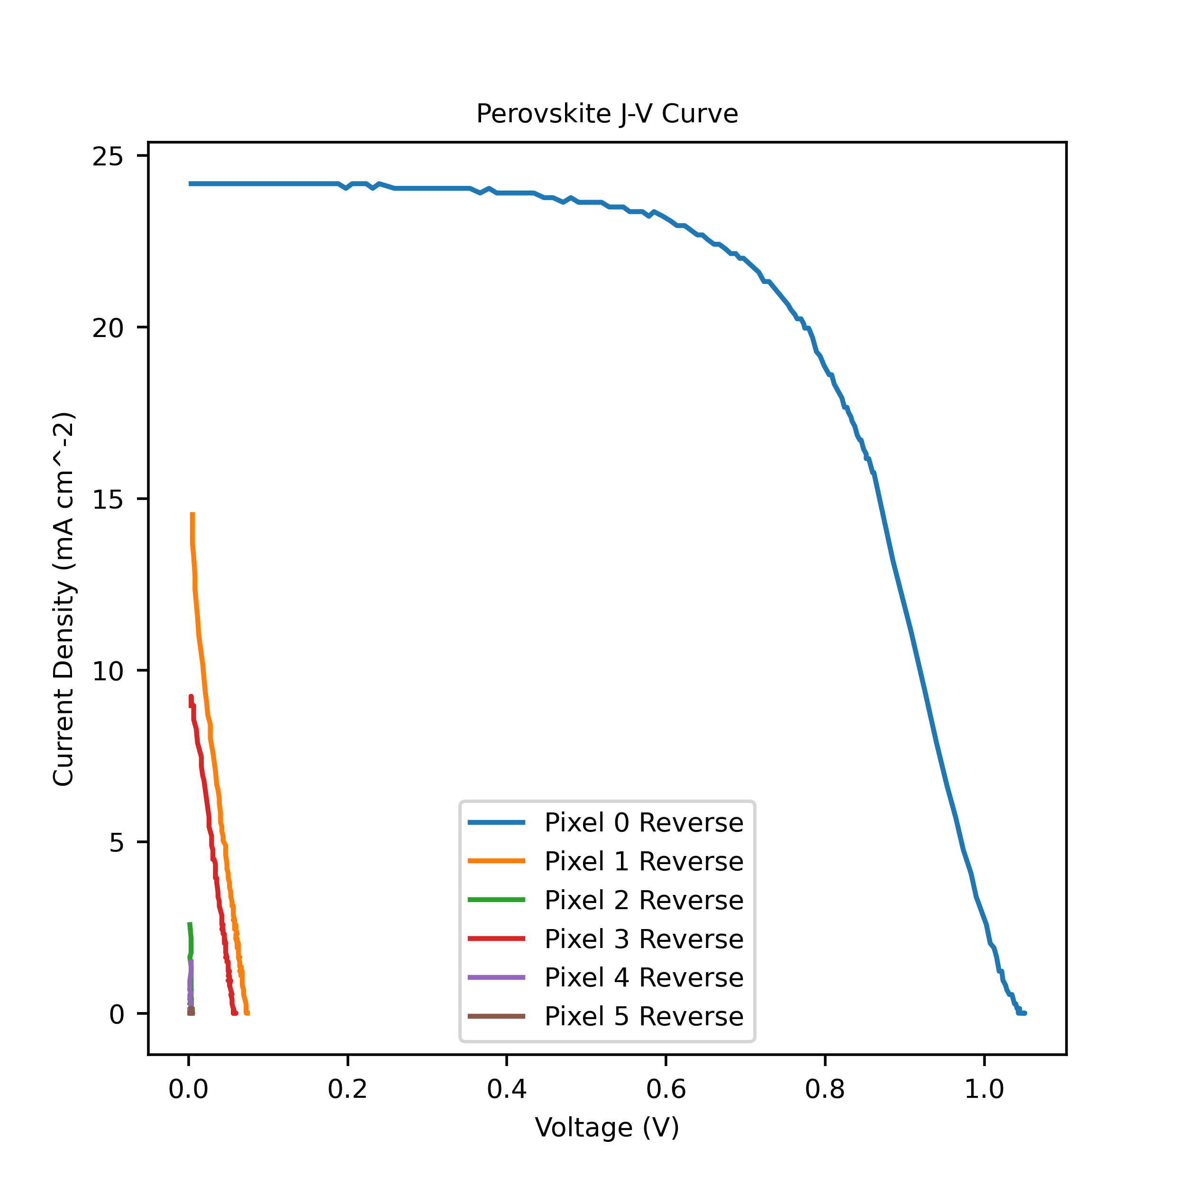
software/curves/3. Final Round/X023_LM/X023_LM_plotted_Reverse.png
