Big-Red-Sat/Perovskite-Curve-Tracer/software/curves/3. Final Round/X025_LM_UE/X---_LM_UE_plotted_Reverse.png

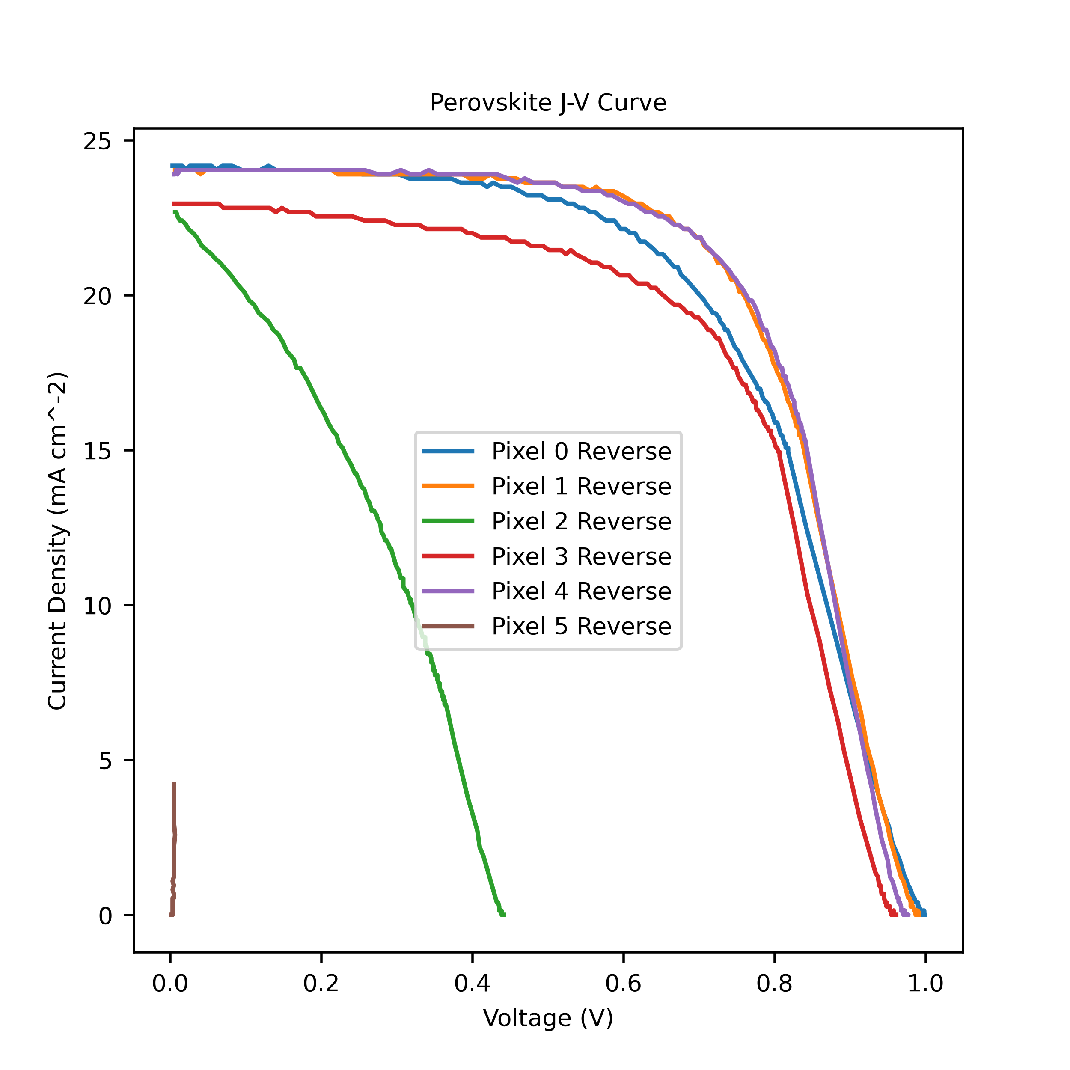
software/curves/3. Final Round/X025_LM_UE/X---_LM_UE_plotted_Reverse.png
