Big-Red-Sat/Perovskite-Curve-Tracer/software/curves/3. Final Round/X026_LM/X026_LM_plotted_Forward.png

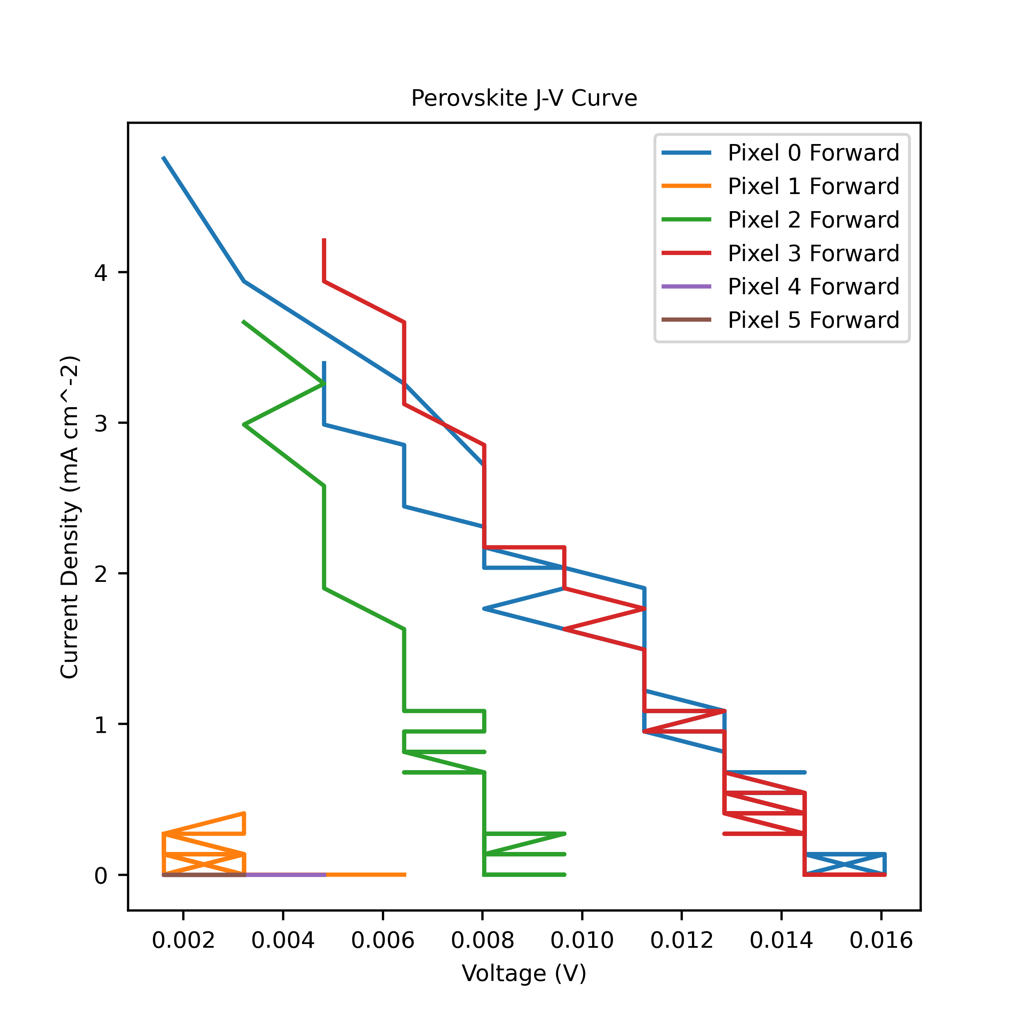
software/curves/3. Final Round/X026_LM/X026_LM_plotted_Forward.png
