Big-Red-Sat/Perovskite-Curve-Tracer/software/curves/3. Final Round/X029_LM/X029_LM_plotted_Forward.png

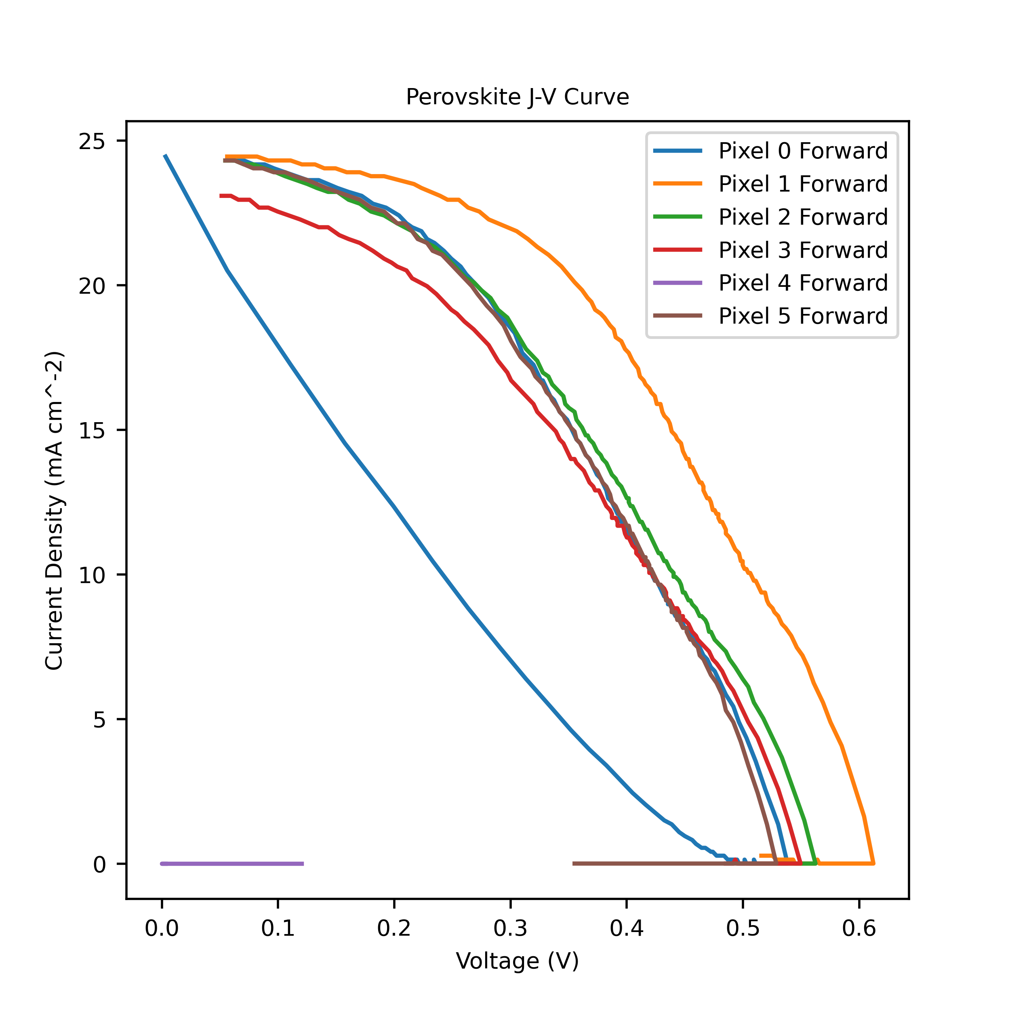
software/curves/3. Final Round/X029_LM/X029_LM_plotted_Forward.png
