Big-Red-Sat/Perovskite-Curve-Tracer/software/curves/3. Final Round/X029_LM/X029_LM_plotted_Reverse.png

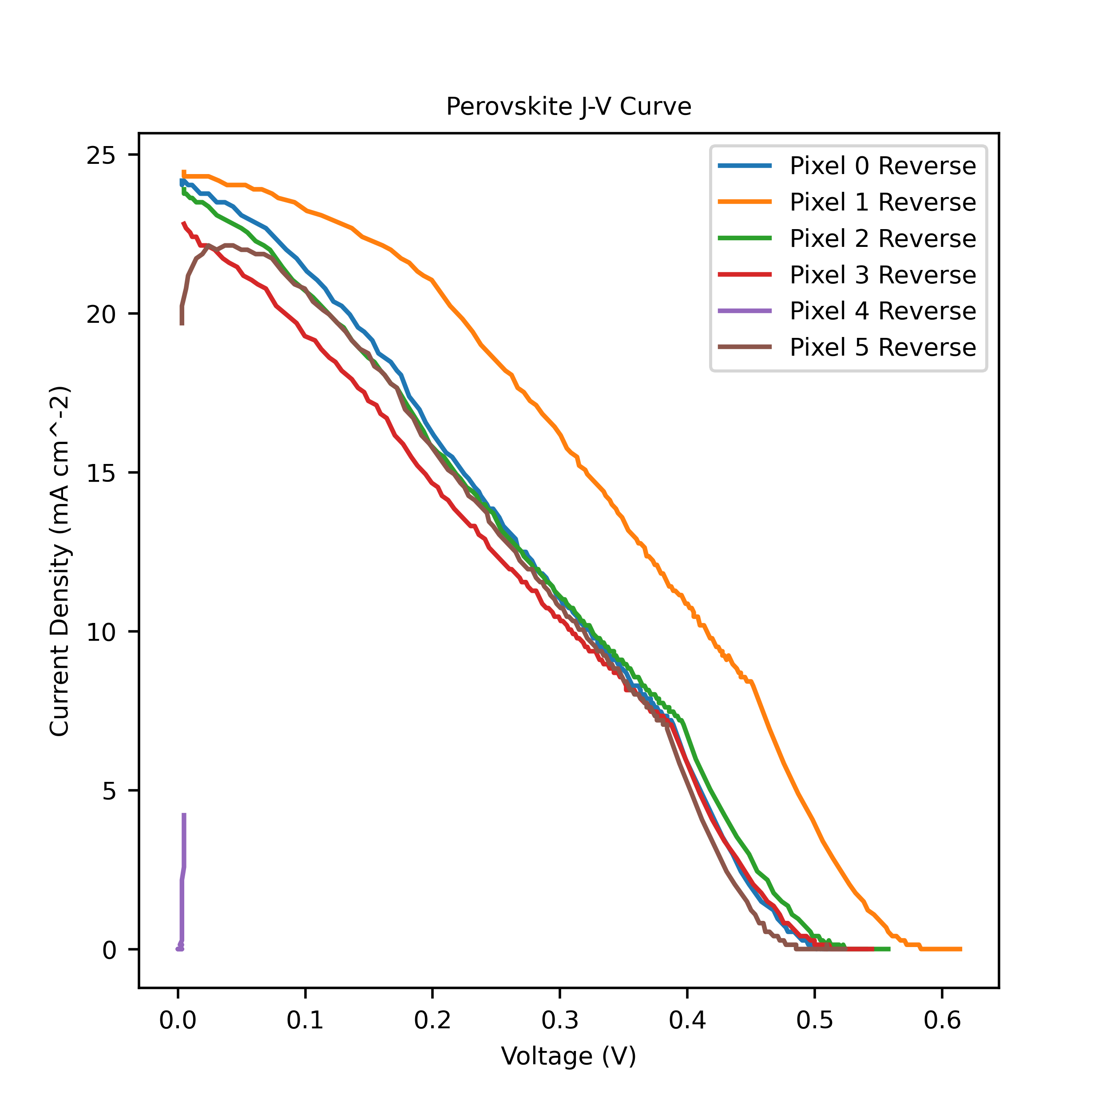
software/curves/3. Final Round/X029_LM/X029_LM_plotted_Reverse.png
