Big-Red-Sat/Perovskite-Curve-Tracer/software/curves/3. Final Round/X030_LM/X030_LM_plotted_Forward.png

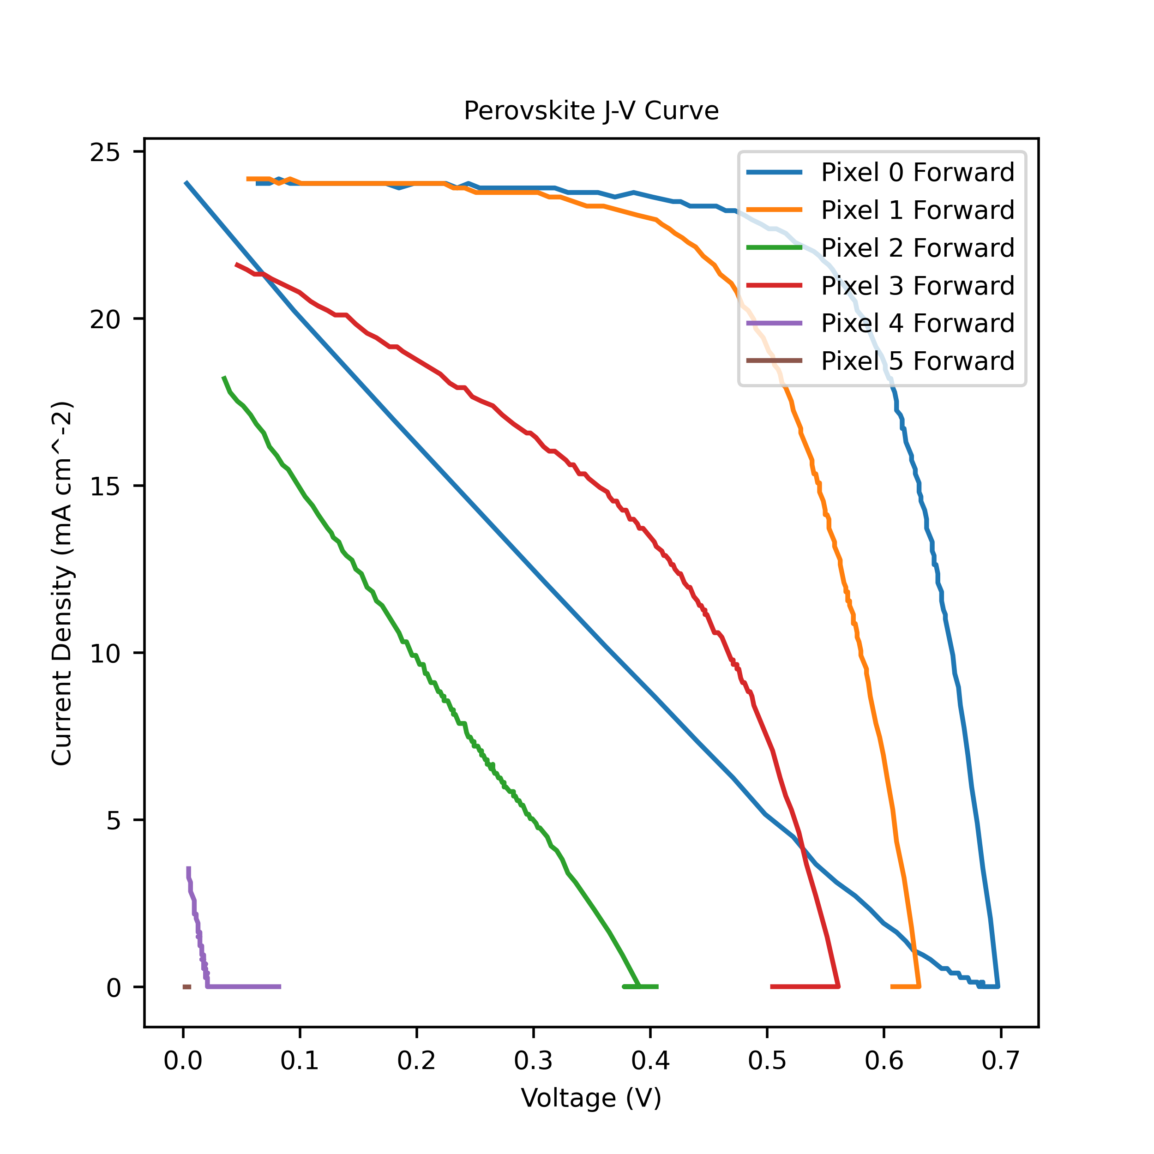
software/curves/3. Final Round/X030_LM/X030_LM_plotted_Forward.png
