Big-Red-Sat/Perovskite-Curve-Tracer/software/curves/Other/prefinal_payload/A033_LM_GB_IP/A033_LM_GB_IP_plotted_Reverse.png

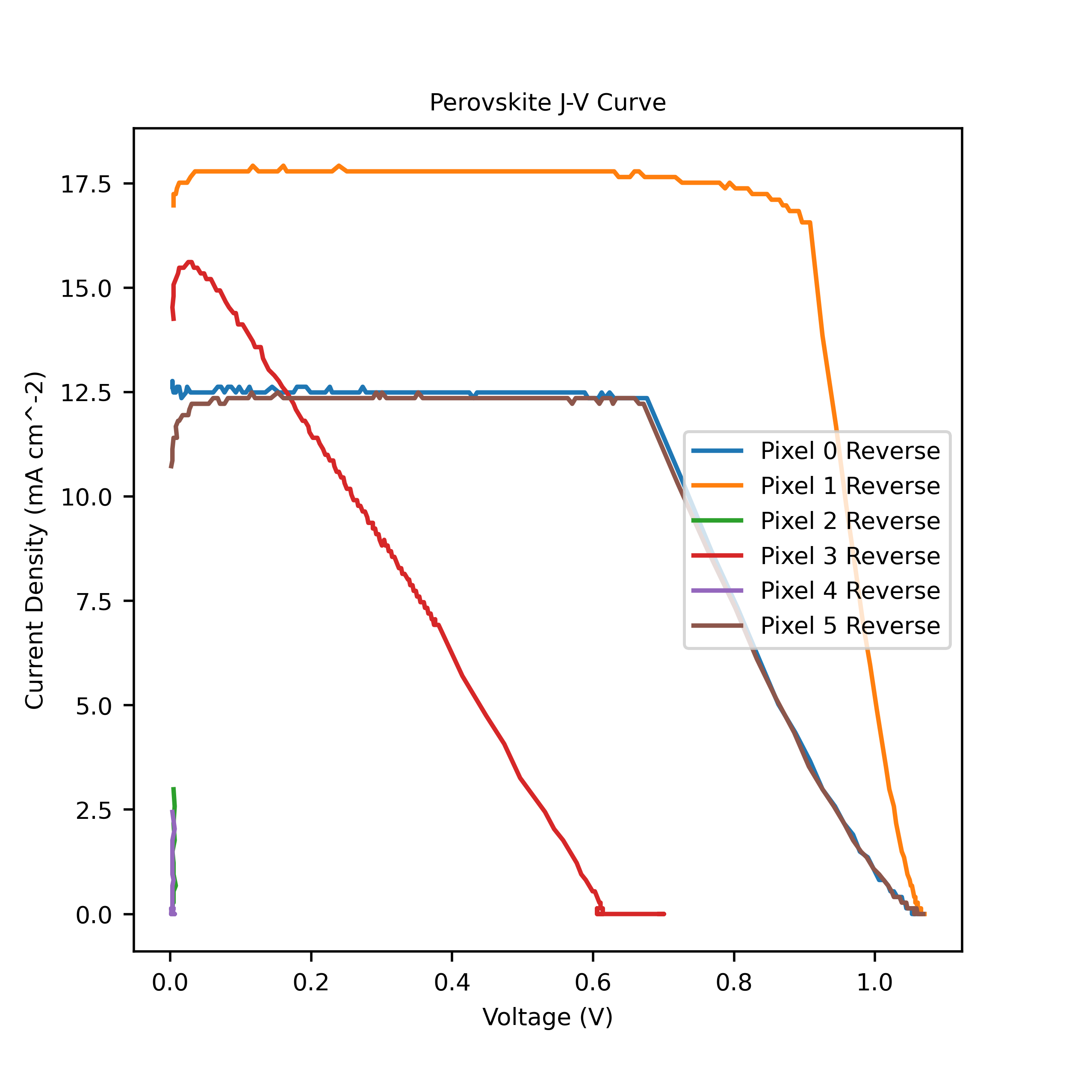
software/curves/Other/prefinal_payload/A033_LM_GB_IP/A033_LM_GB_IP_plotted_Reverse.png
