Big-Red-Sat/Perovskite-Curve-Tracer/software/curves/Other/prefinal_payload/A035_LM_GB/A035_LM_GB_plotted_Reverse.png

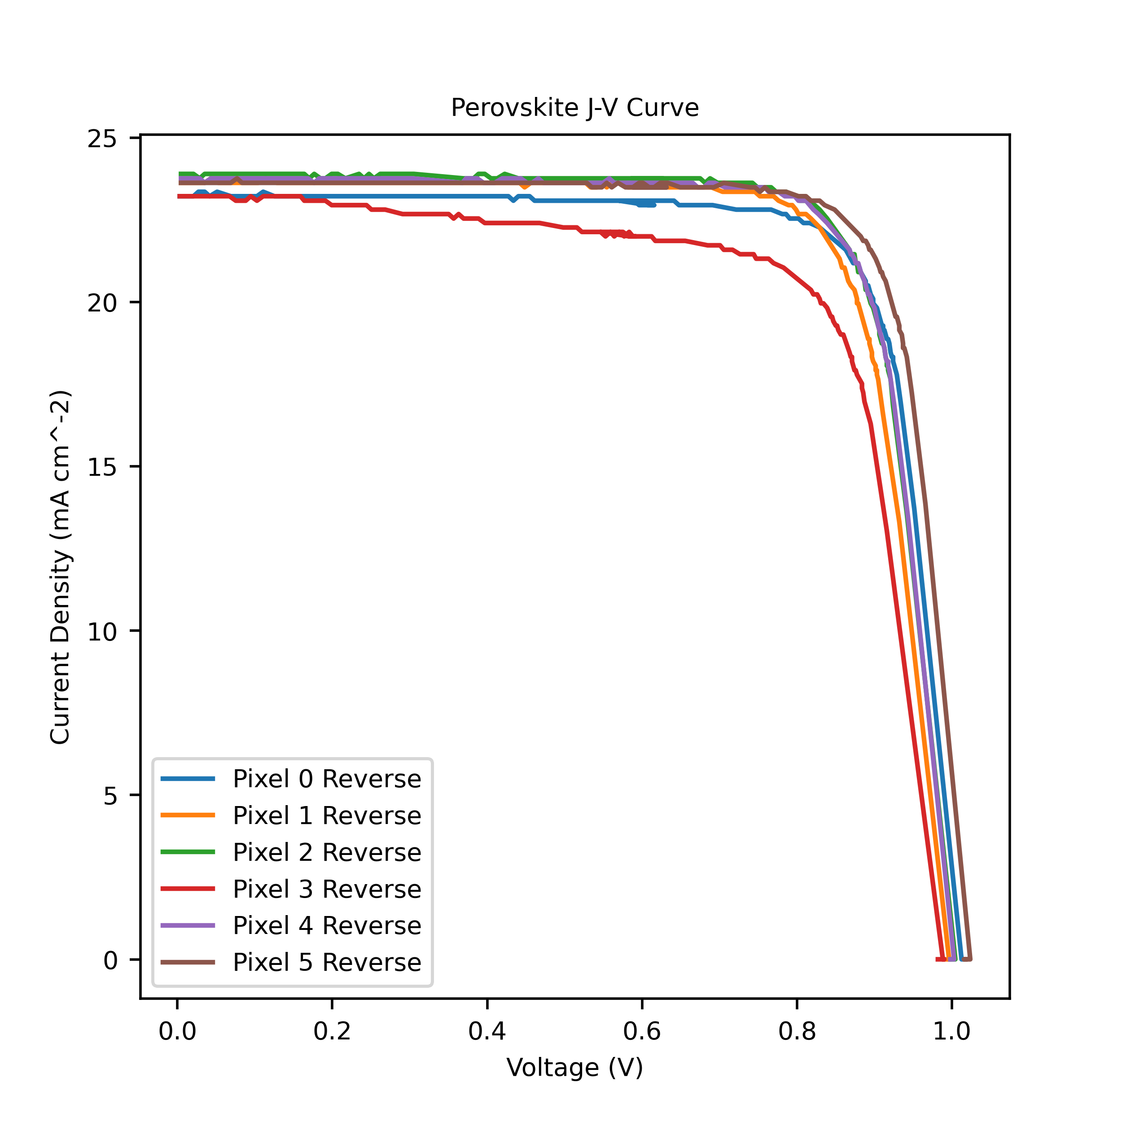
software/curves/Other/prefinal_payload/A035_LM_GB/A035_LM_GB_plotted_Reverse.png
