Big-Red-Sat/Perovskite-Curve-Tracer/software/curves/Other/prefinal_payload/A048_LM_GB_IP/A048_LM_GB_IP_plotted_Reverse.png

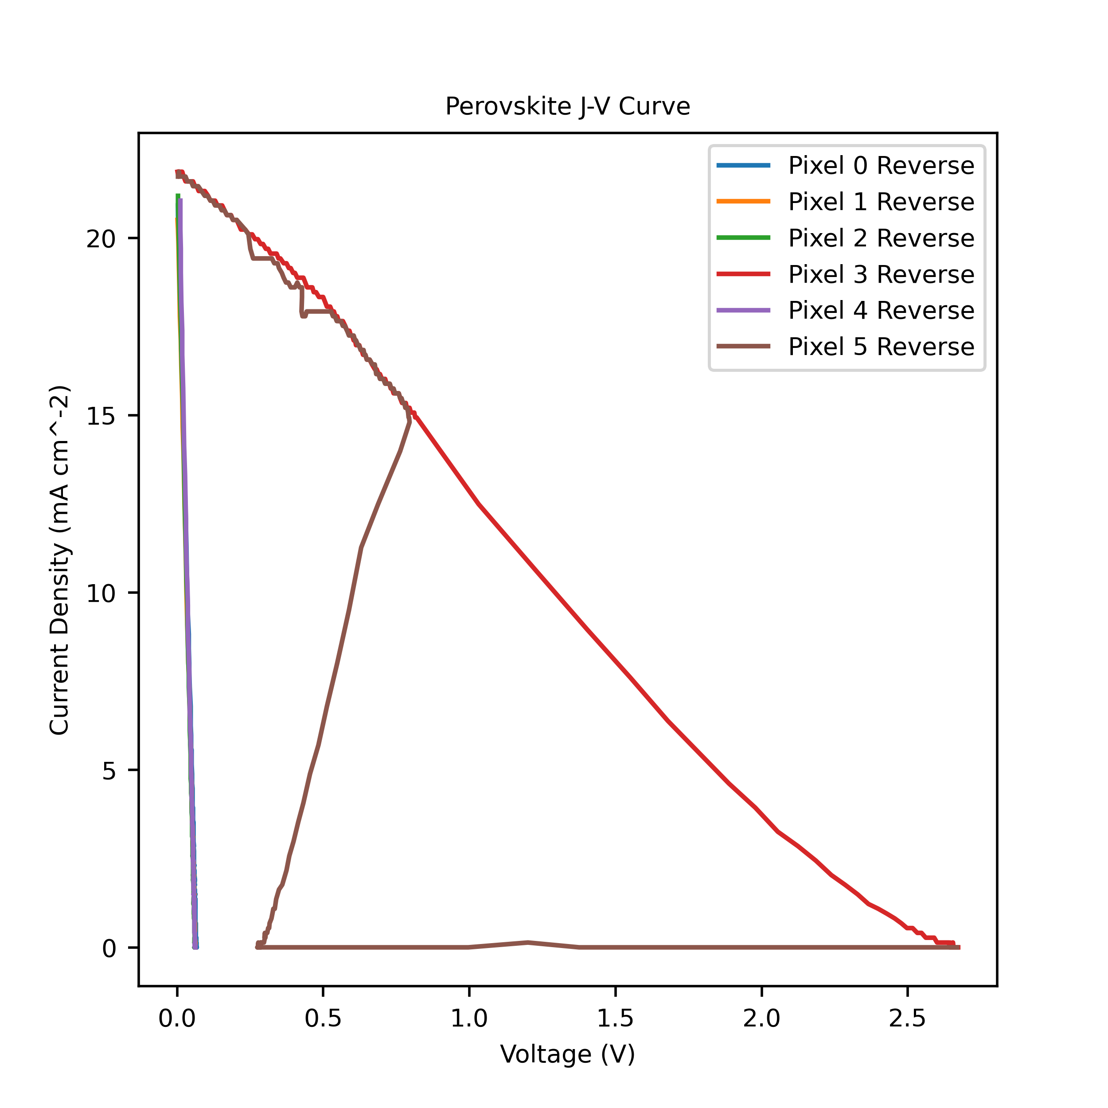
software/curves/Other/prefinal_payload/A048_LM_GB_IP/A048_LM_GB_IP_plotted_Reverse.png
