Big-Red-Sat/Perovskite-Curve-Tracer/software/curves/Payload1/X001_Payload1/A001_Payload1_plotted_Forward.png

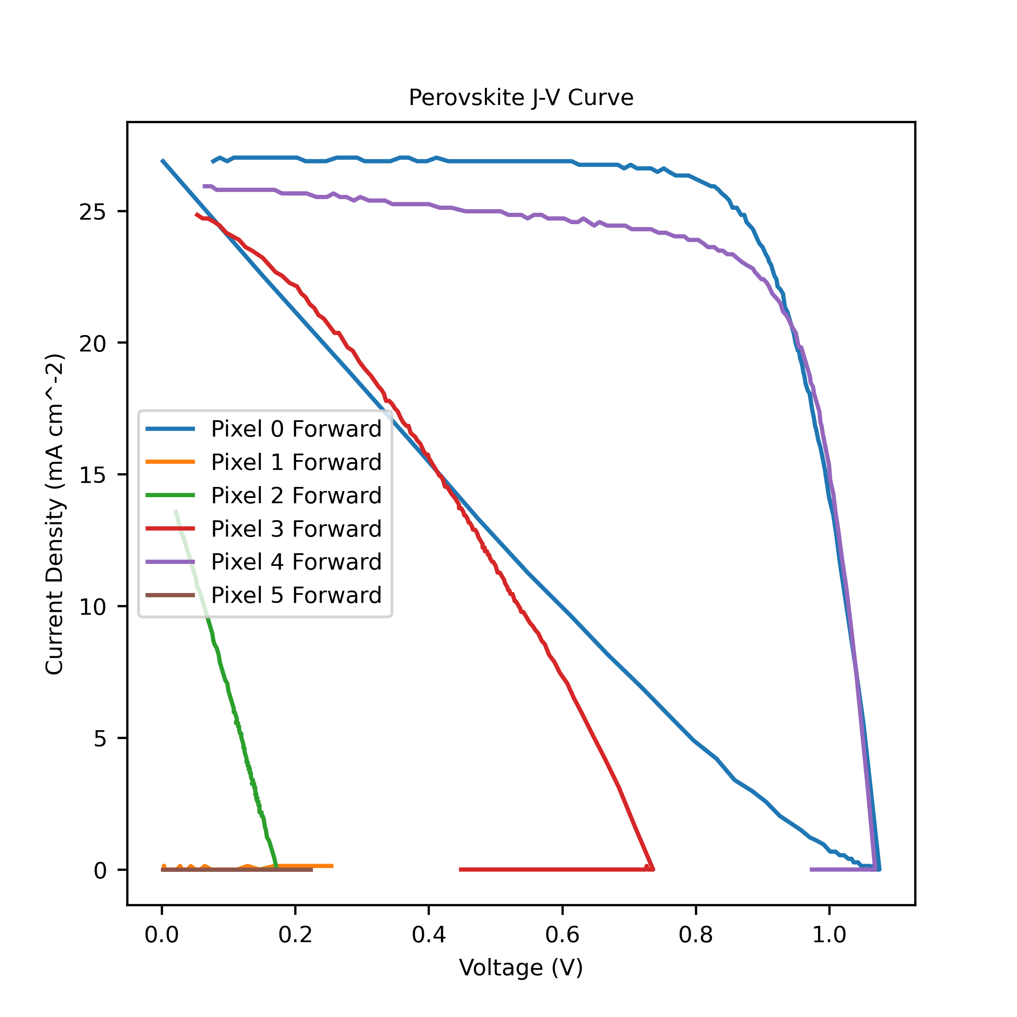
software/curves/Payload1/X001_Payload1/A001_Payload1_plotted_Forward.png
