Big-Red-Sat/Perovskite-Curve-Tracer/software/curves/Payload1/X012_Payload1/A012_Payload2_plotted_Reverse.png

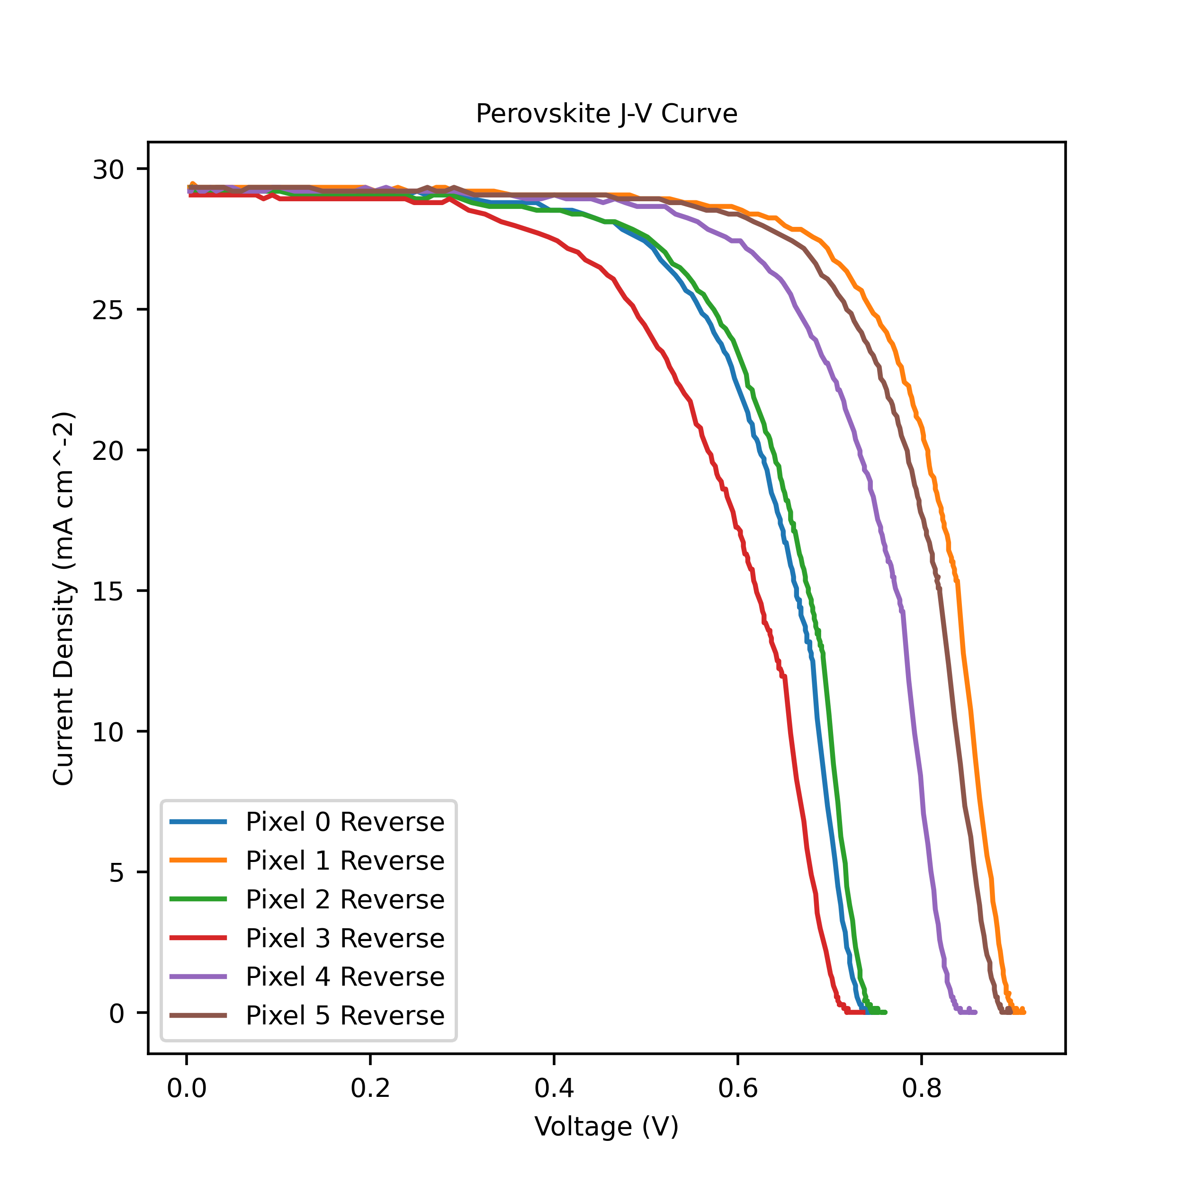
software/curves/Payload1/X012_Payload1/A012_Payload2_plotted_Reverse.png
