Big-Red-Sat/Perovskite-Curve-Tracer/software/curves/Payload1/X012_Payload1_C/X012_Payload1_C_plotted_Forward.png

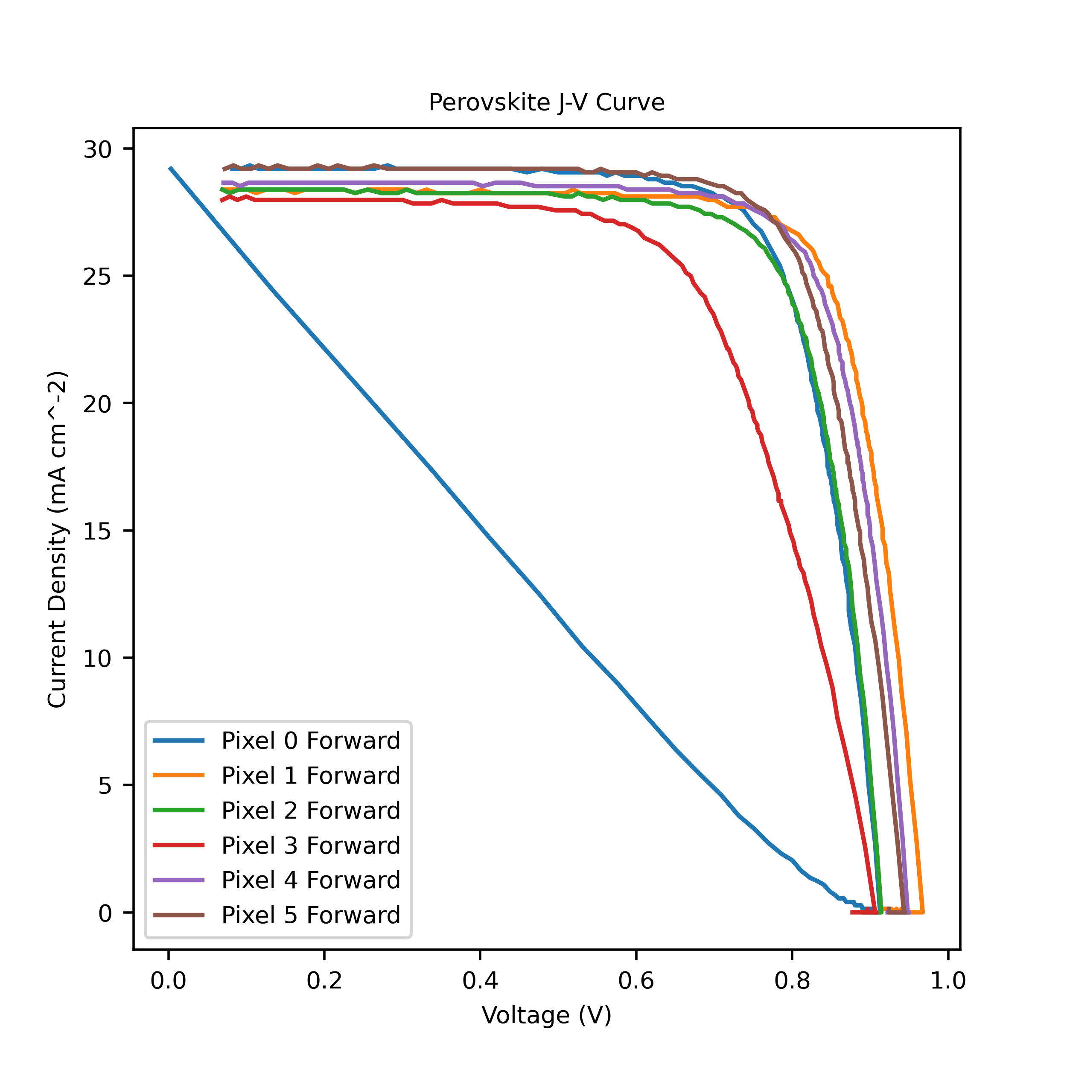
software/curves/Payload1/X012_Payload1_C/X012_Payload1_C_plotted_Forward.png
