Big-Red-Sat/Perovskite-Curve-Tracer/software/curves/Payload1/X017_Payload1/X017_Payload1_plotted_Reverse.png

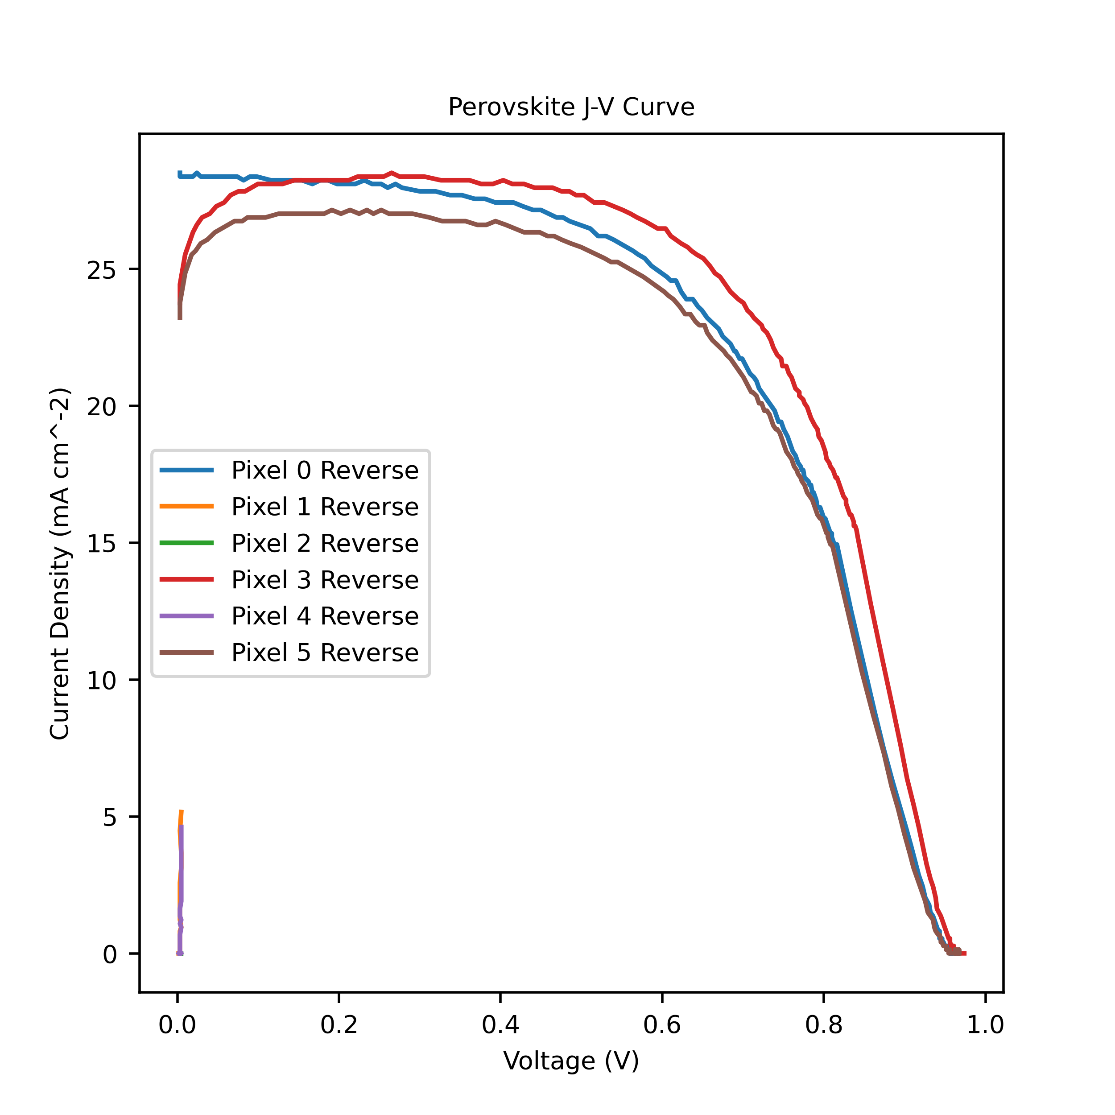
software/curves/Payload1/X017_Payload1/X017_Payload1_plotted_Reverse.png
