Big-Red-Sat/Perovskite-Curve-Tracer/software/curves/Payload1/X017_Payload1_C/X017_Payload1_C_plotted_Reverse.png

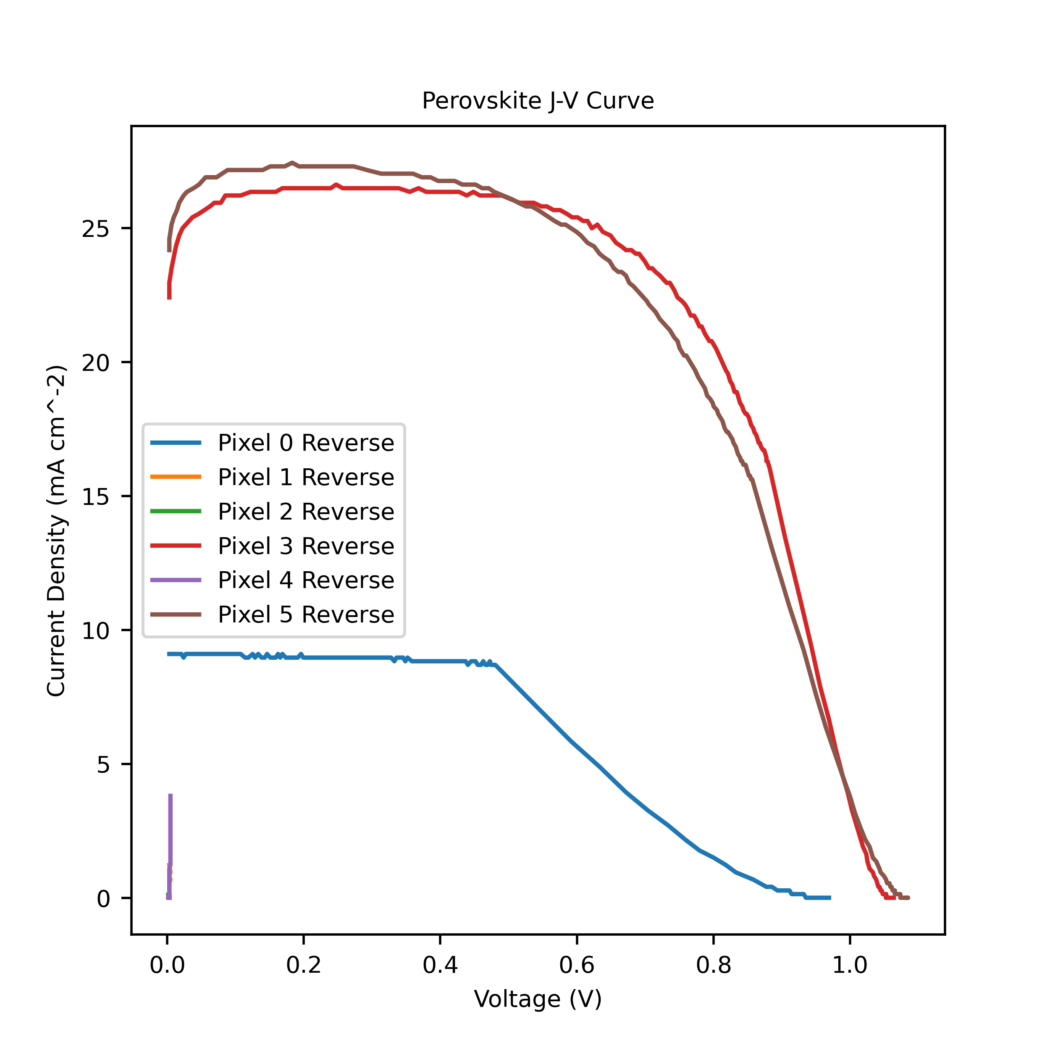
software/curves/Payload1/X017_Payload1_C/X017_Payload1_C_plotted_Reverse.png
