Big-Red-Sat/Perovskite-Curve-Tracer/software/curves/Payload2/X016_Payload2_Assy/X016_Payload2_Assy_plotted_Forward.png

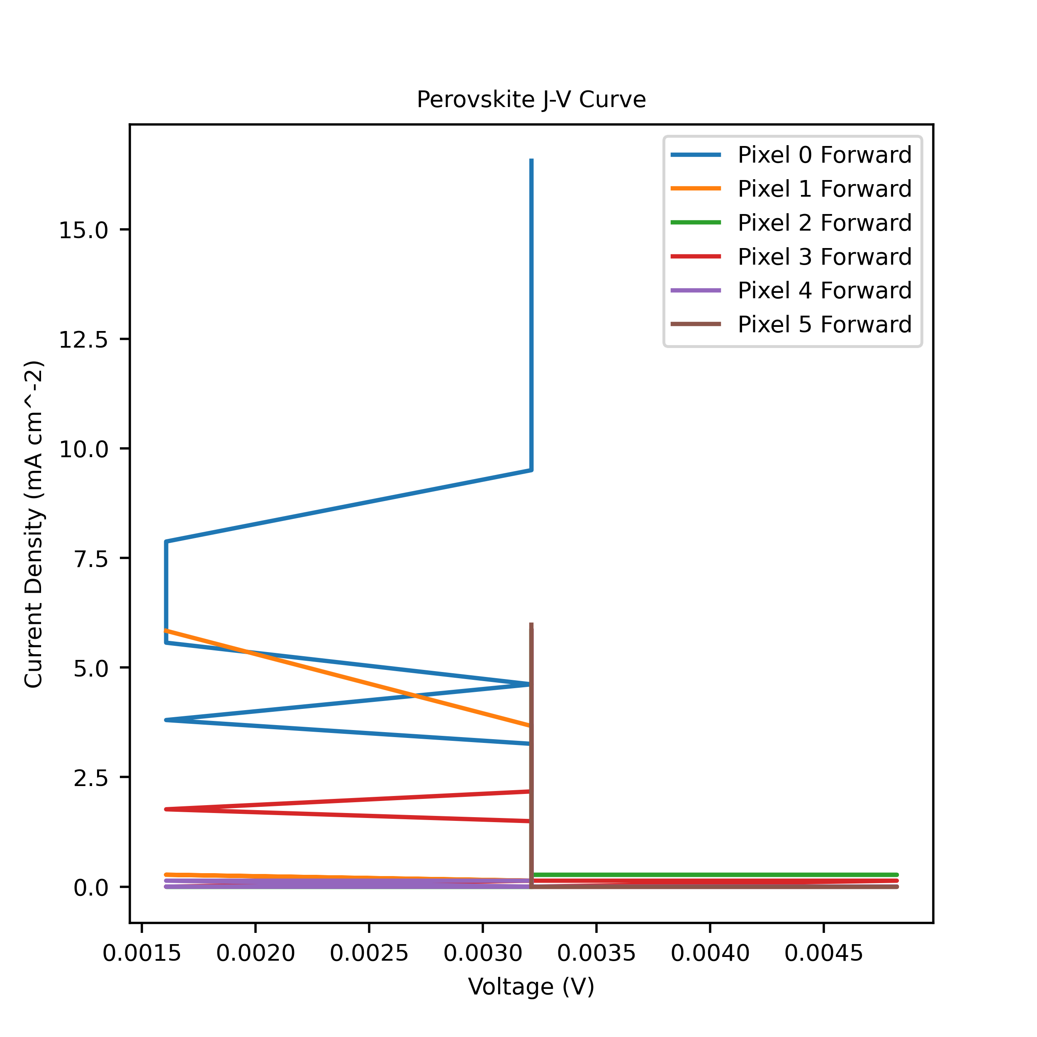
software/curves/Payload2/X016_Payload2_Assy/X016_Payload2_Assy_plotted_Forward.png
