Big-Red-Sat/Perovskite-Curve-Tracer/software/curves/Payload2/X016_Payload2_Assy/X016_Payload2_Assy_plotted_Reverse.png

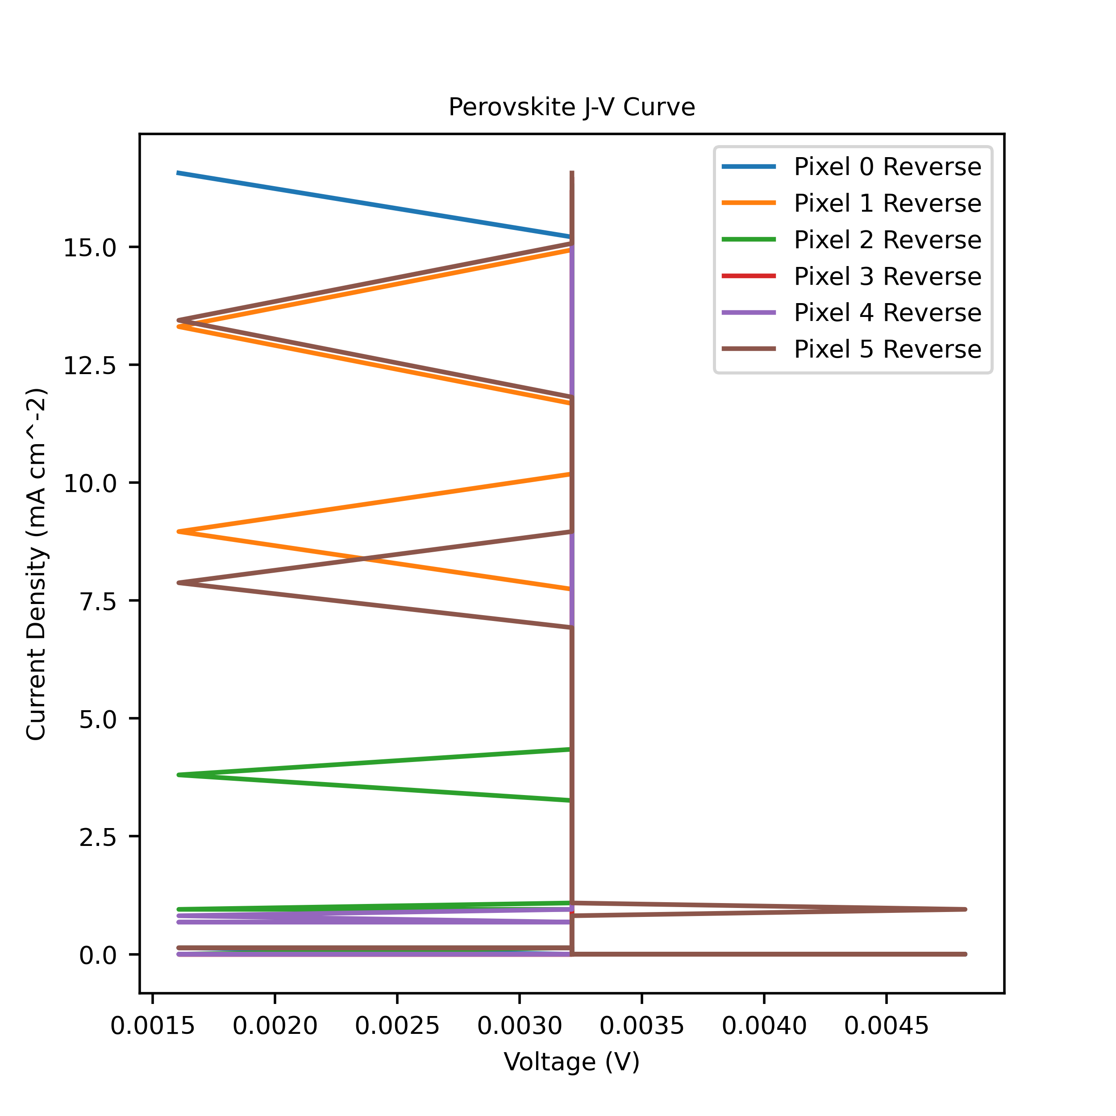
software/curves/Payload2/X016_Payload2_Assy/X016_Payload2_Assy_plotted_Reverse.png
