Big-Red-Sat/Perovskite-Curve-Tracer/software/curves/X031_Dead/X031_Dead_plotted_Forward.png

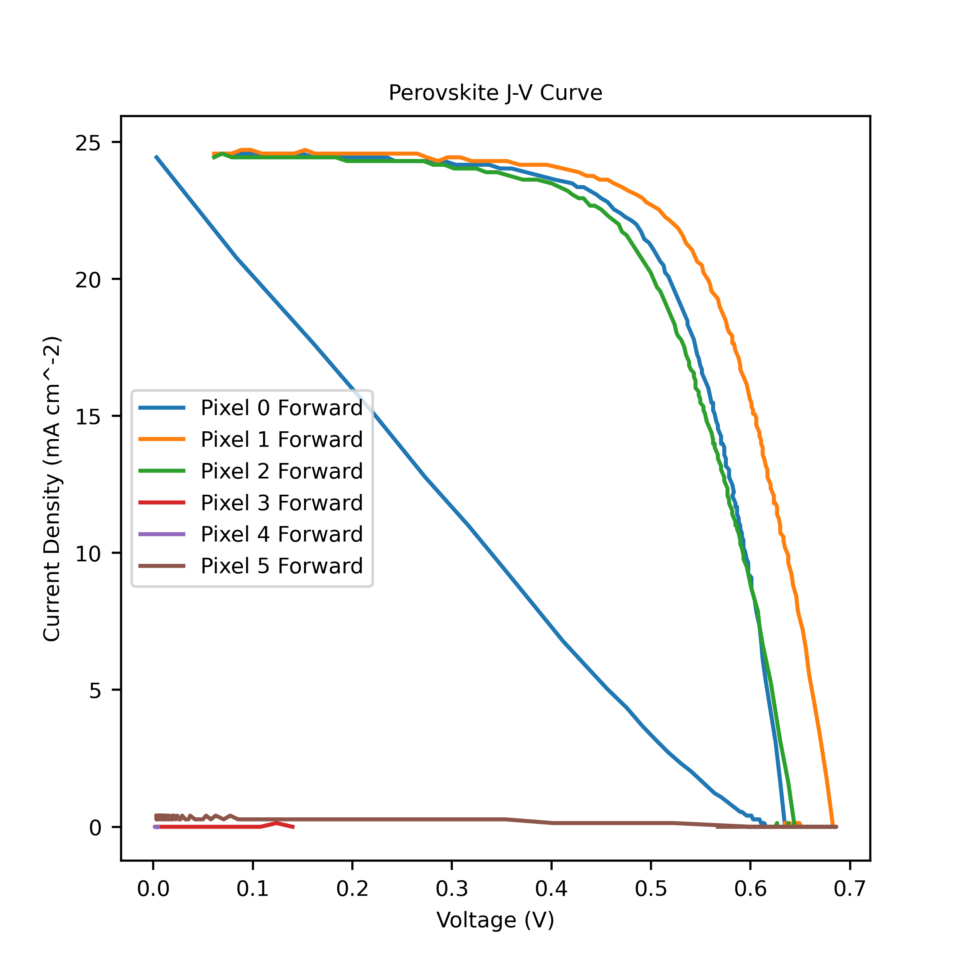
software/curves/X031_Dead/X031_Dead_plotted_Forward.png
