Big-Red-Sat/Perovskite-Curve-Tracer/software/curves/X031_LM/X031_LM_plotted_Forward.png

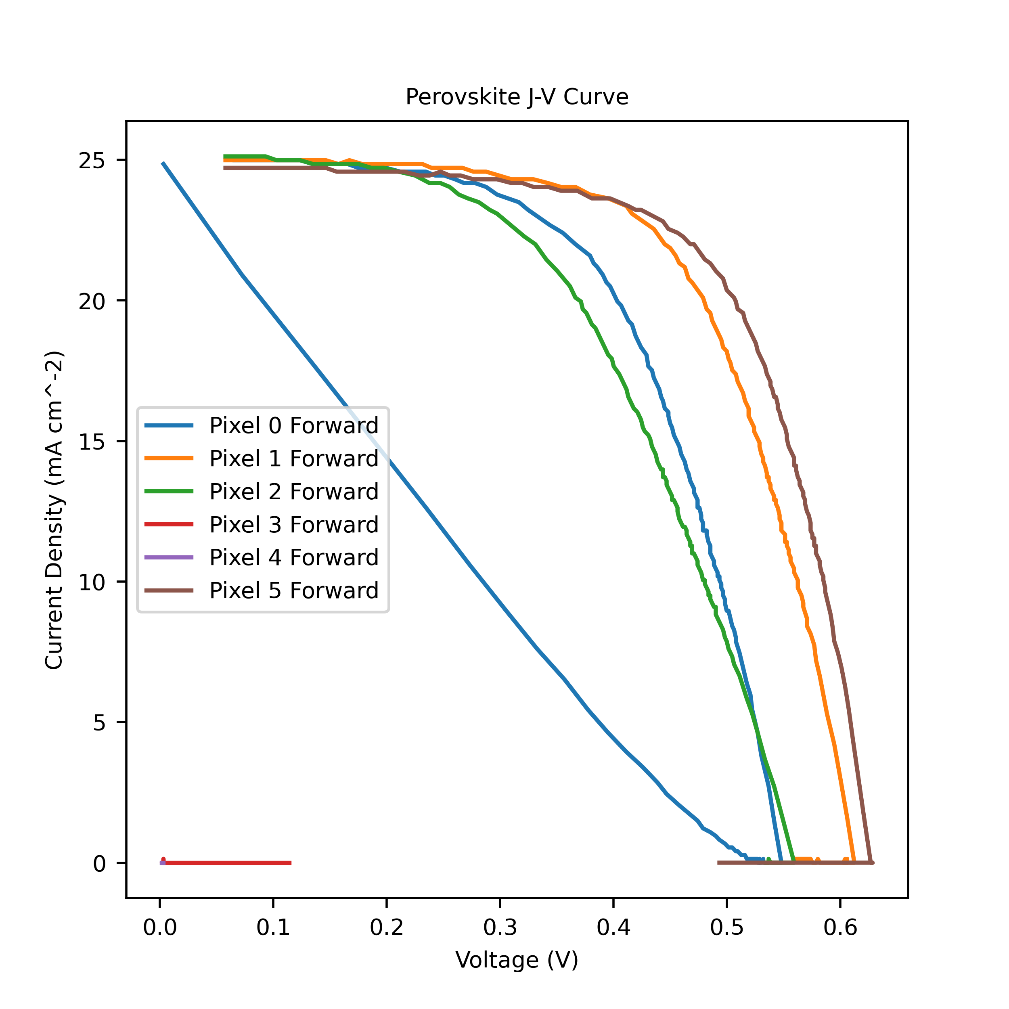
software/curves/X031_LM/X031_LM_plotted_Forward.png
