Big-Red-Sat/Perovskite-Curve-Tracer/software/curves/X031_LM/X031_LM_plotted_Reverse.png

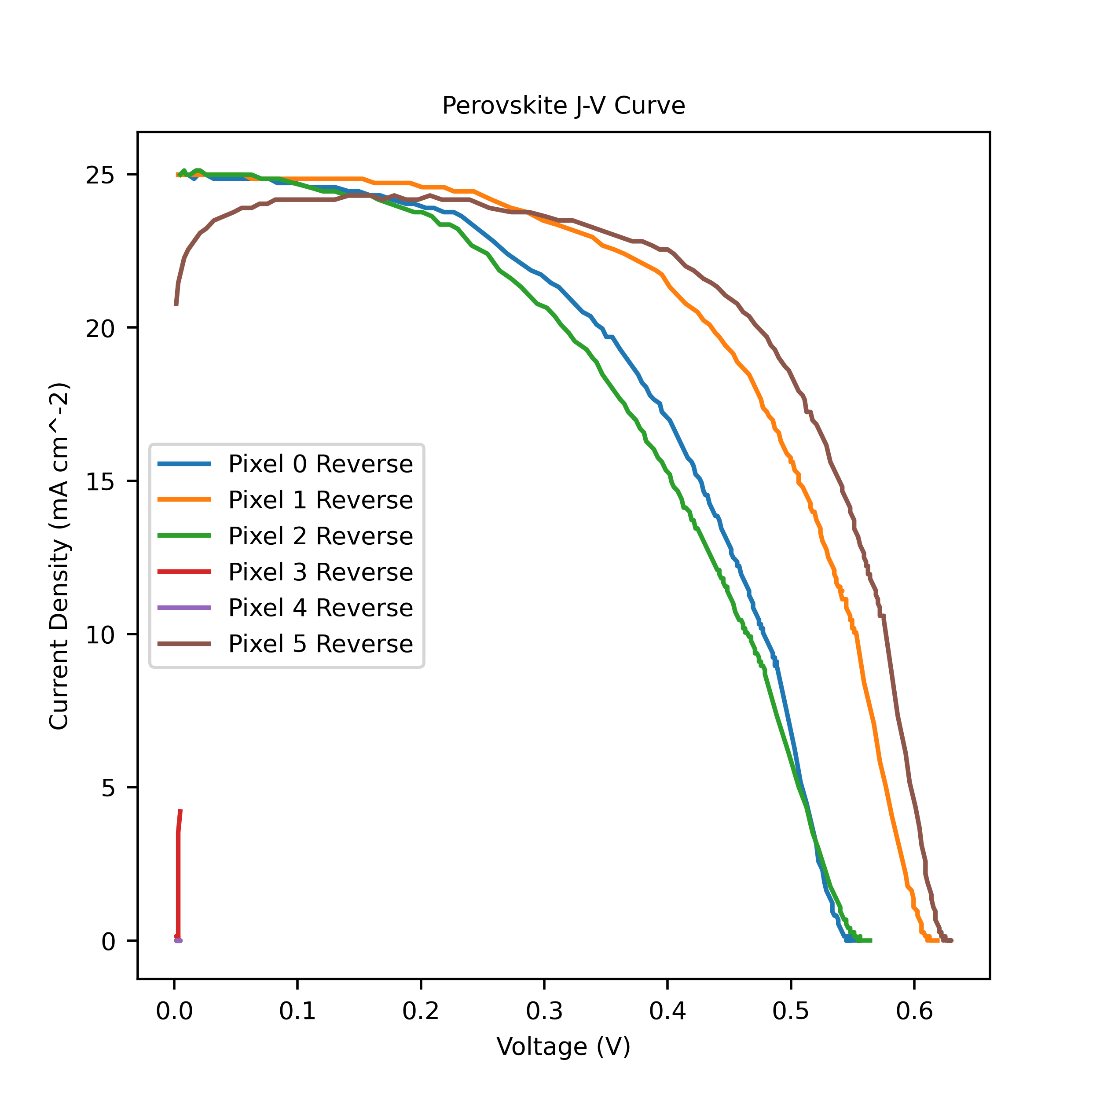
software/curves/X031_LM/X031_LM_plotted_Reverse.png
