Big-Red-Sat/Perovskite-Curve-Tracer/software/leakage_forward.png

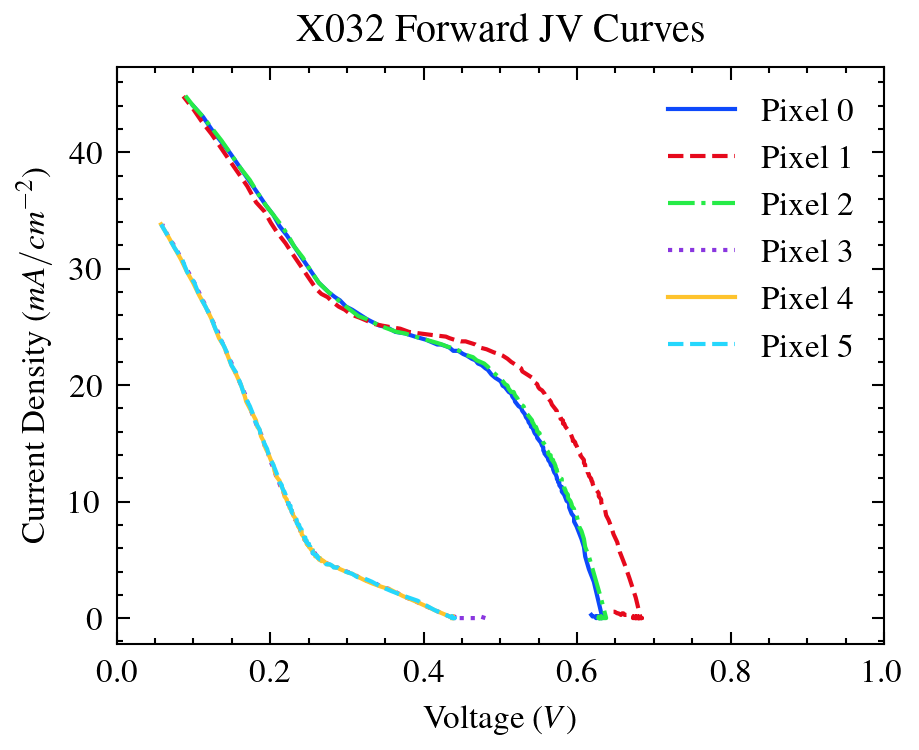
software/leakage_forward.png
