Big-Red-Sat/Perovskite-Curve-Tracer/software/leakage_reverse.png

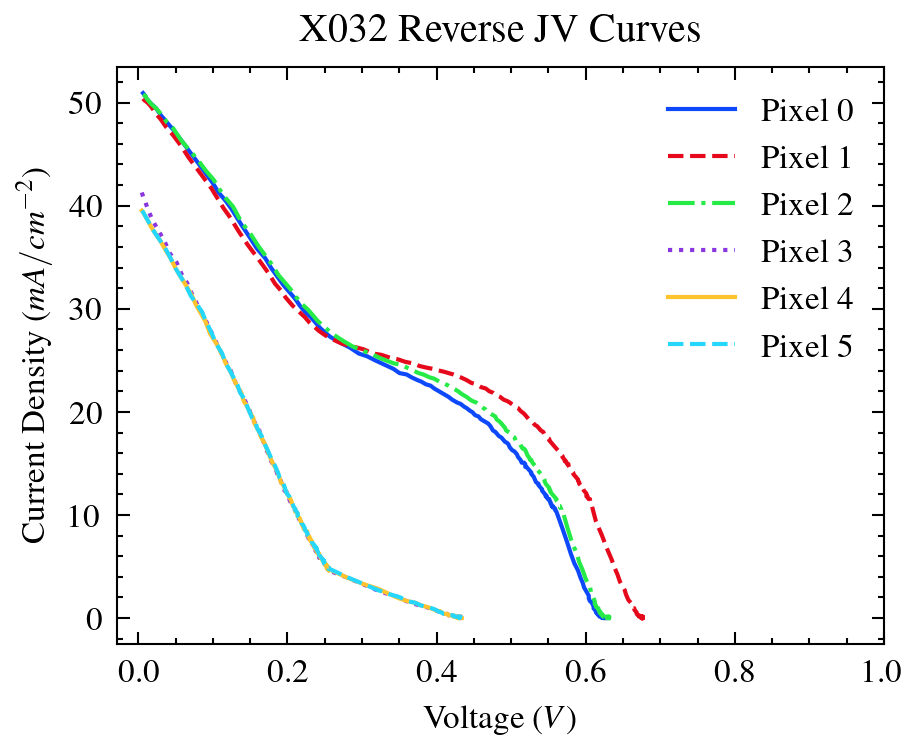
software/leakage_reverse.png
