Big-Red-Sat/Perovskite-Curve-Tracer/software/x018_forward.png

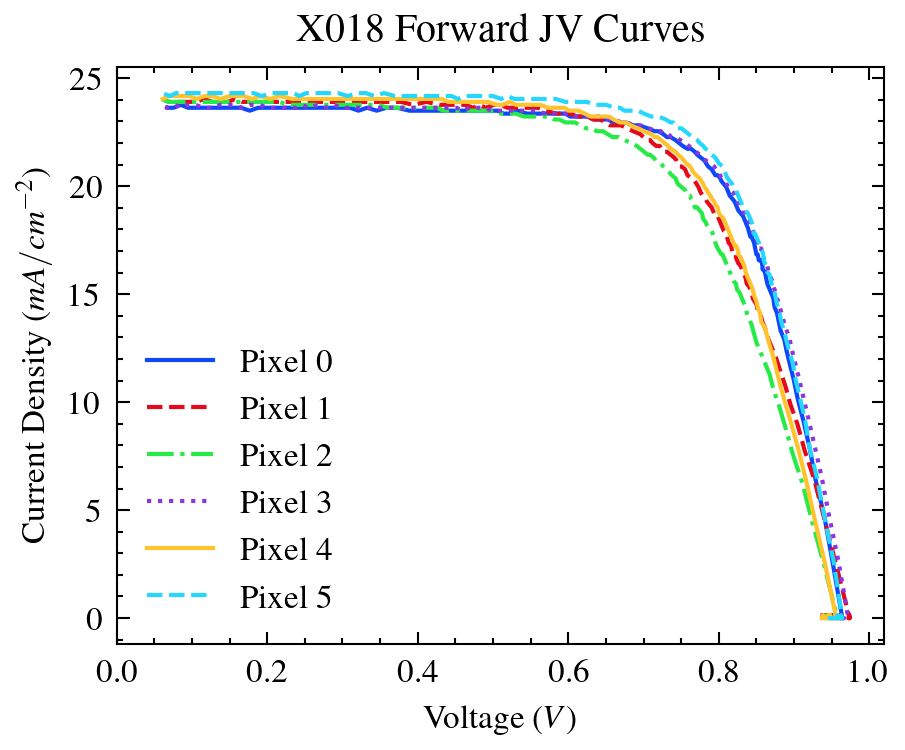
software/x018_forward.png
