Big-Red-Sat/Perovskite-Curve-Tracer/software/x018_reverse.png

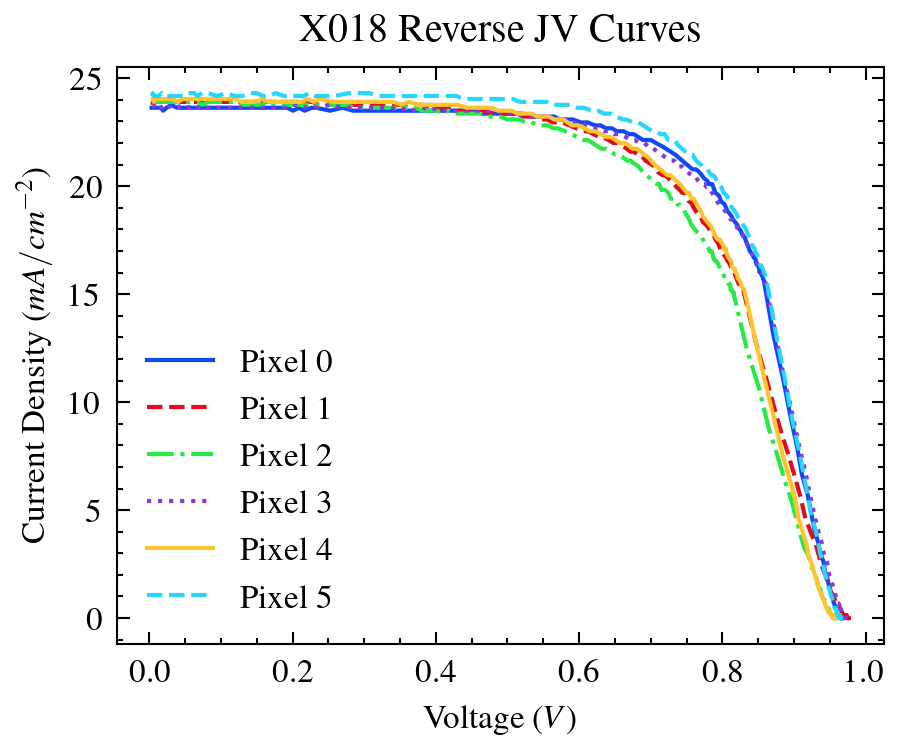
software/x018_reverse.png
