Big-Red-Sat/Perovskite-Curve-Tracer/hardware/multiplexer cell tester/KiCAD Parts/LT3092EDD_TRPBF/LT3092EDD_TRPBF.step

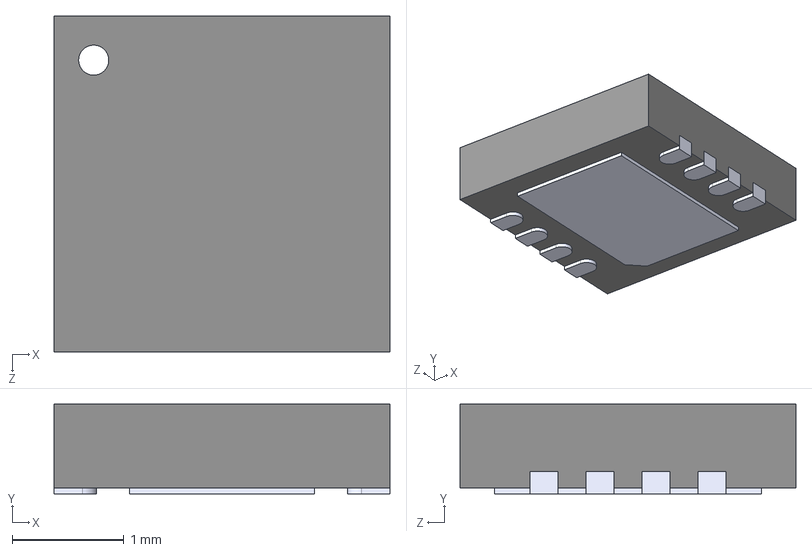
[picture p129: CAD file, 2023-08-19]
hardware/multiplexer cell tester/KiCAD Parts/LT3092EDD_TRPBF/LT3092EDD_TRPBF.step
3.00 x 0.8 x 3.00 mm
