Big-Red-Sat/Perovskite-Curve-Tracer/hardware/multiplexer cell tester/KiCAD Parts/LT3092ETS8TRPBF/LT3092ETS8TRPBF.step

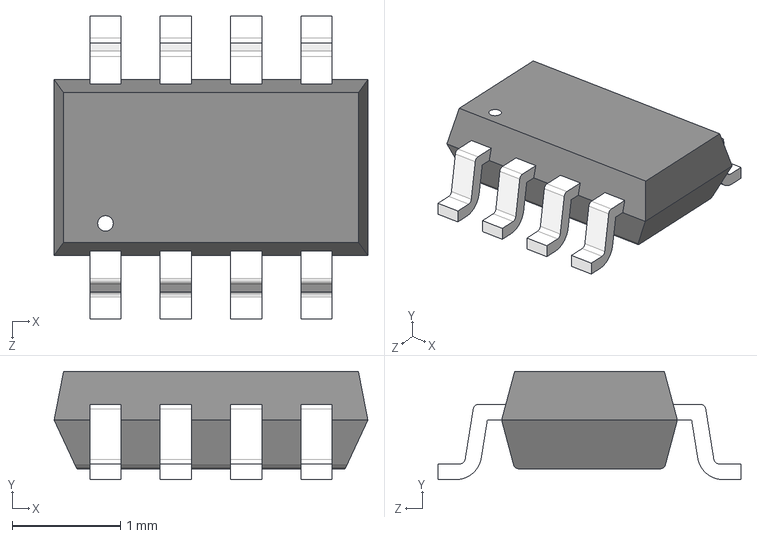
[picture p130: CAD file, 2023-08-19]
hardware/multiplexer cell tester/KiCAD Parts/LT3092ETS8TRPBF/LT3092ETS8TRPBF.step
2.90 x 1.00 x 2.80 mm
