Big-Red-Sat/Perovskite-Curve-Tracer/hardware/multiplexer cell tester/KiCAD Parts/MAX4736EUBT/MAX4736EUBT.step

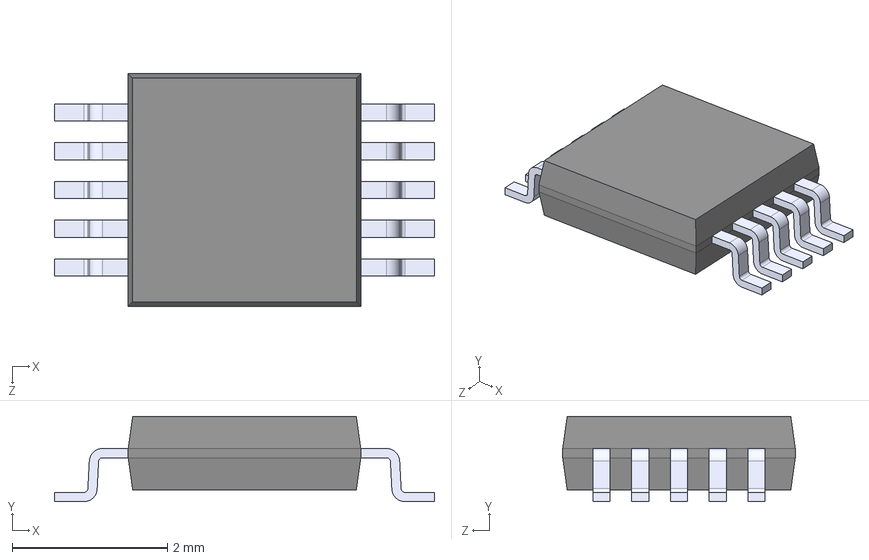
[picture p131: CAD file, 2023-08-19]
hardware/multiplexer cell tester/KiCAD Parts/MAX4736EUBT/MAX4736EUBT.step
4.90 x 1.10 x 3.00 mm
