Big-Red-Sat/Perovskite-Curve-Tracer/hardware/multiplexer cell tester/KiCAD Parts/MSP430FR5969IRGZR/MSP430FR5969IRGZR.step

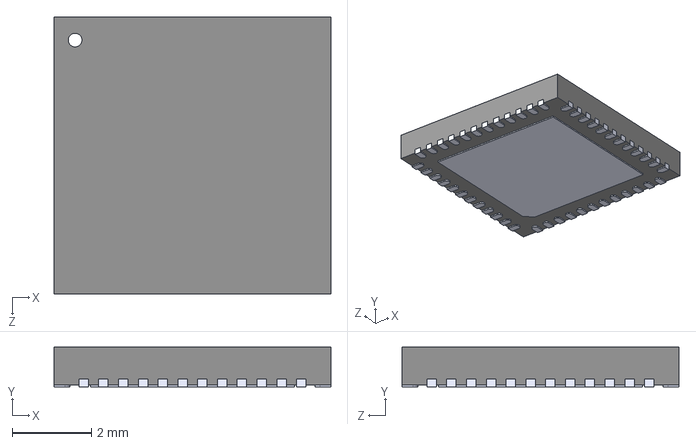
[picture p132: CAD file, 2023-08-19]
hardware/multiplexer cell tester/KiCAD Parts/MSP430FR5969IRGZR/MSP430FR5969IRGZR.step
7.00 x 1.00 x 7.00 mm
