Big-Red-Sat/Perovskite-Curve-Tracer/hardware/multiplexer cell tester/KiCAD Parts/NX3L4051PW_118/NX3L4051PW_118.step

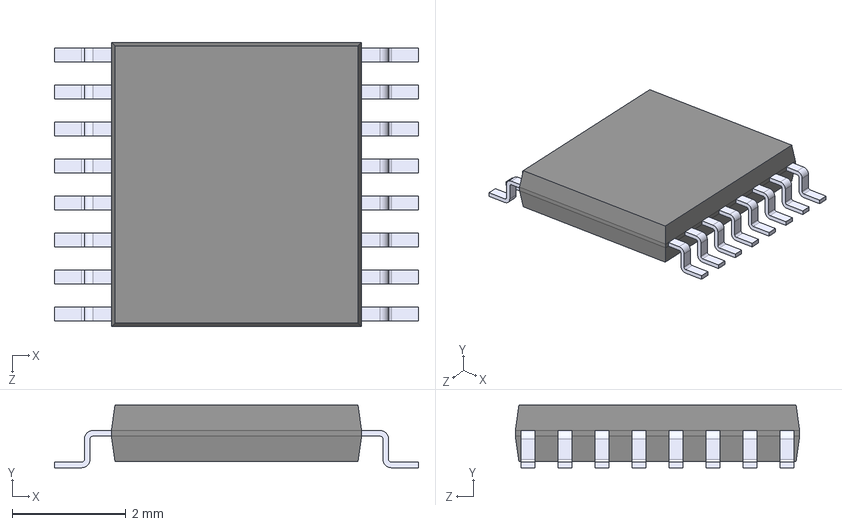
[picture p133: CAD file, 2023-08-19]
hardware/multiplexer cell tester/KiCAD Parts/NX3L4051PW_118/NX3L4051PW_118.step
6.40 x 1.10 x 5.00 mm
