Big-Red-Sat/Perovskite-Curve-Tracer/hardware/payload holder/DXF/1SkiteHolder.DXF

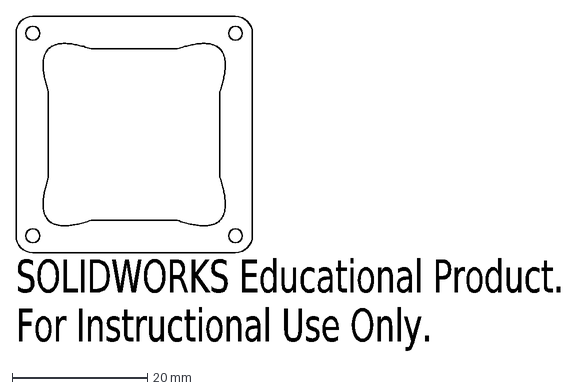
[picture p135: CAD file, 2023-08-19]
hardware/payload holder/DXF/1SkiteHolder.DXF
SOLIDWORKS Educational Product.
For Instructional Use Only.
