Big-Red-Sat/Perovskite-Curve-Tracer/hardware/payload holder/Holder/body.stl

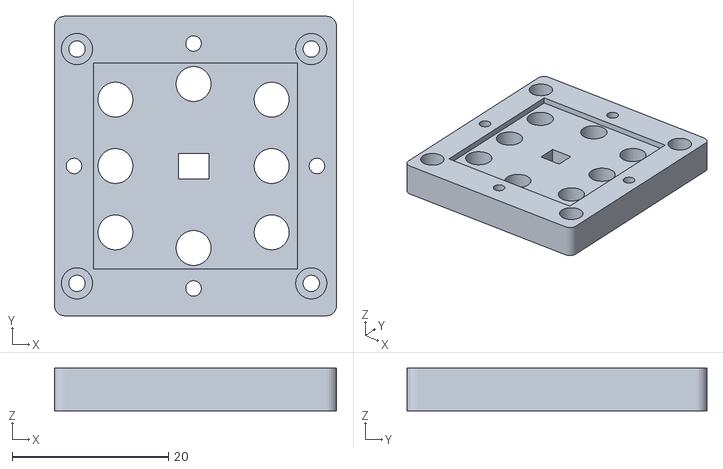
[picture p136: CAD file, 2023-08-19]
hardware/payload holder/Holder/body.stl
36.1 x 38.4 x 5.50
