Big-Red-Sat/Perovskite-Curve-Tracer/hardware/payload holder/KICAD Parts/MCP9804/_Depreciated_MCP9804-E_MC.stp

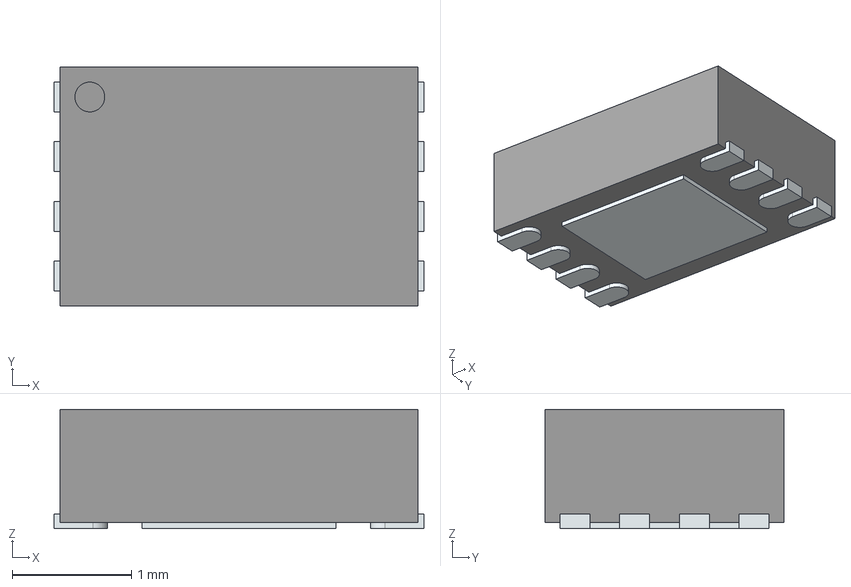
[picture p137: CAD file, 2023-08-19]
hardware/payload holder/KICAD Parts/MCP9804/_Depreciated_MCP9804-E_MC.stp
3.10 x 2.00 x 1.00 mm
ThermalPin
PinsArrayLR
