Big-Red-Sat/Perovskite-Curve-Tracer/hardware/payload holder/KICAD Parts/Perovskite/Perovskite v2.step

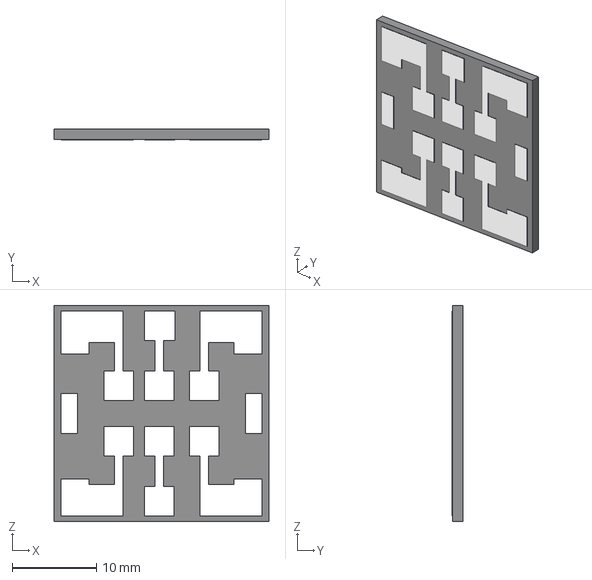
[picture p138: CAD file, 2023-08-19]
hardware/payload holder/KICAD Parts/Perovskite/Perovskite v2.step
25.5 x 1.30 x 25.7 mm
