Big-Red-Sat/Perovskite-Curve-Tracer/hardware/payload holder/Render/perovskite_router.step

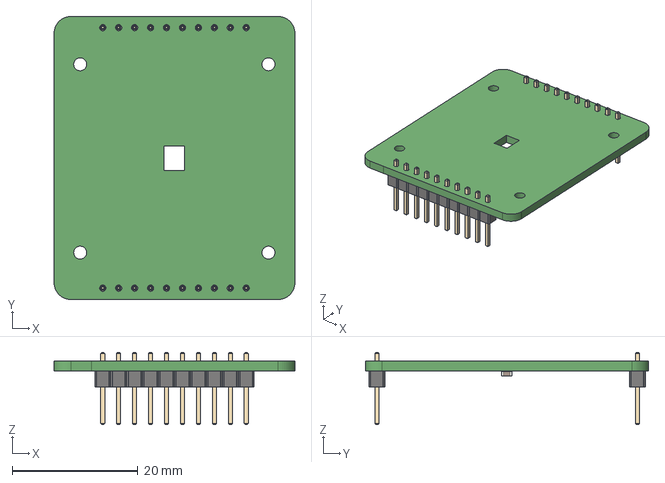
[picture p139: CAD file, 2023-09-08]
hardware/payload holder/Render/perovskite_router.step
38.4 x 45.1 x 11.5 mm
