Big-Red-Sat/Perovskite-Curve-Tracer/hardware/cell holder/Holder/payload_holder_p1.stl

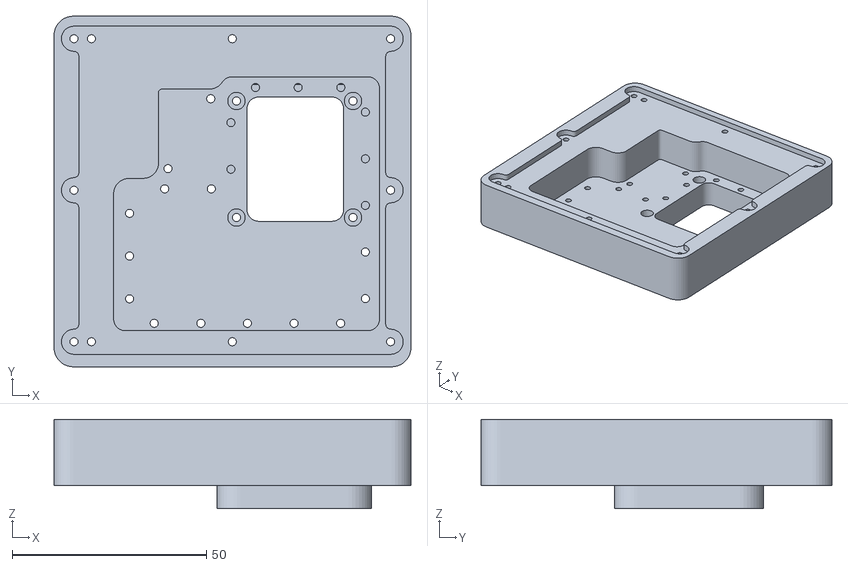
[picture p140: CAD file, 2023-09-08]
hardware/cell holder/Holder/payload_holder_p1.stl
91.9 x 90.3 x 23.0
