Big-Red-Sat/Perovskite-Curve-Tracer/hardware/multiplexer cell tester/KiCAD Parts/ul_ADG841YKSZ-500RL7/SC70-6.step

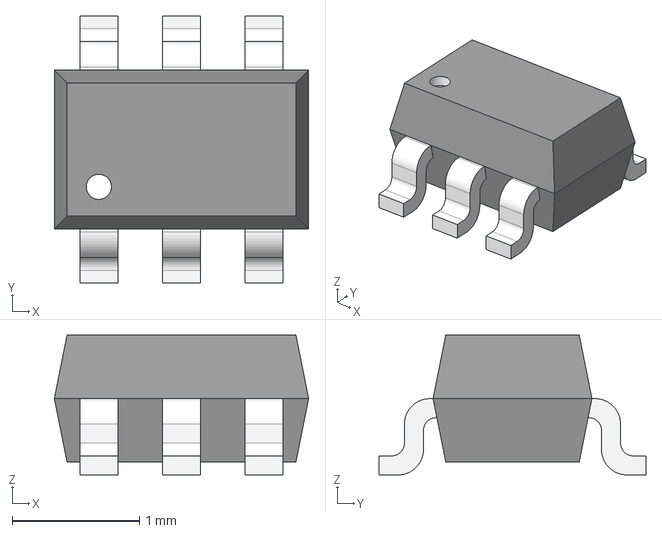
[picture p141: CAD file, 2023-08-19]
hardware/multiplexer cell tester/KiCAD Parts/ul_ADG841YKSZ-500RL7/SC70-6.step
2.00 x 2.10 x 1.10 mm
