Big-Red-Sat/Perovskite-Curve-Tracer/hardware/payload holder/Holder/arm.stl

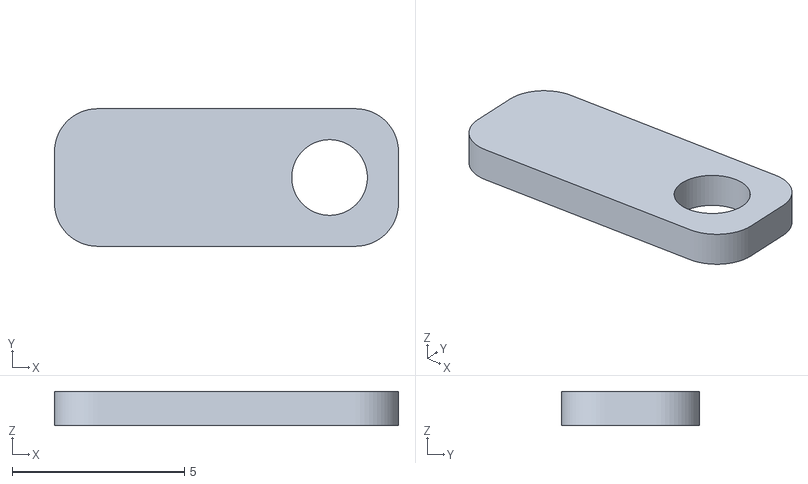
[picture p142: CAD file, 2023-08-19]
hardware/payload holder/Holder/arm.stl
10.0 x 4.00 x 1.00
