Big-Red-Sat/Perovskite-Curve-Tracer/hardware/cell holder/Holder/arm_v2.stl

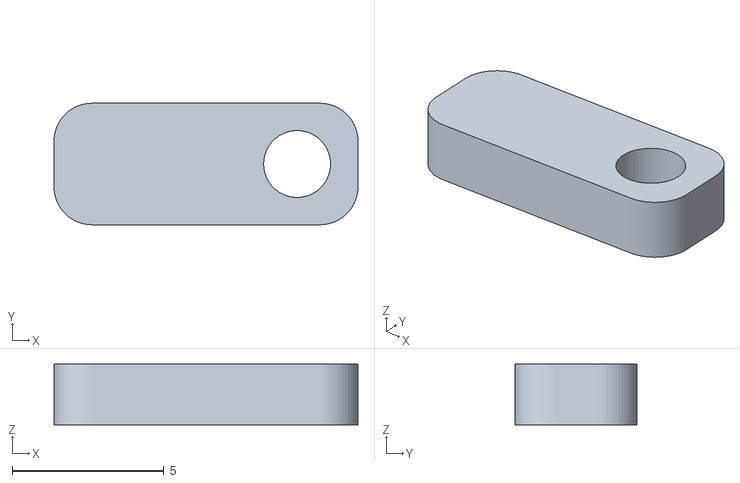
[picture p143: CAD file, 2023-09-08]
hardware/cell holder/Holder/arm_v2.stl
10.0 x 4.00 x 2.00
