Big-Red-Sat/Perovskite-Curve-Tracer/hardware/cell holder/Holder/body_v2.stl

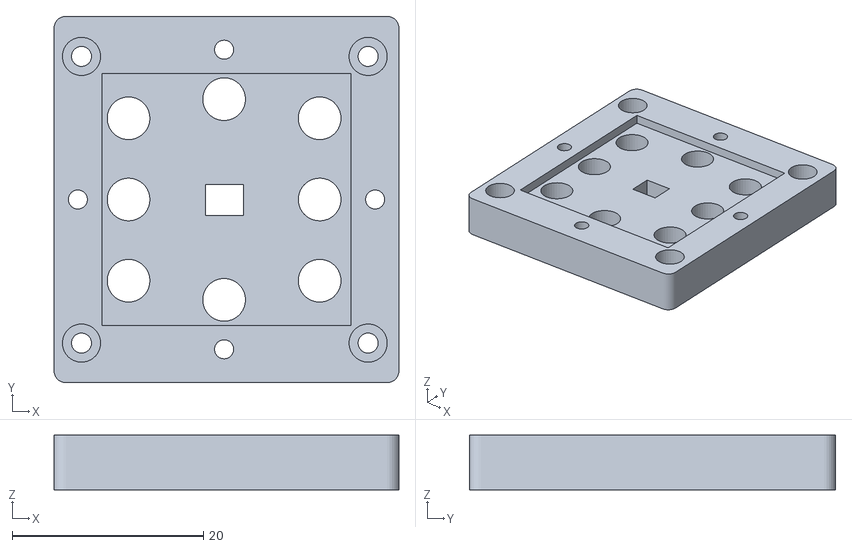
[picture p145: CAD file, 2023-09-08]
hardware/cell holder/Holder/body_v2.stl
36.1 x 38.4 x 5.75
