Big-Red-Sat/Perovskite-Curve-Tracer/software/curves/X031_ShuntTest_500_LongSettle/curve_0.0_0_Forward.xlsx

Sheet: Summary
 | 0
Time | 2023-10-22 16:05
ID | X031_ShuntTest_500_LongSettle
Pixel | 0
Pixel Area | 0.058
Irradiance | 100
Panel Temperature | 0
Voc | 0.004820512821
Isc | 2.882855706
Vmp | 0.5061538462
Imp | 1.291771409
Pmp | 0.6538350672
FF | 47.04884177
Eff | 0.112730184
Dir | Forward

Sheet: Data
 | Voltage | Current | Current Density | Power
0 | 0.004820512821 | 2.961622256 | 51.06245269 | 0.01427653805
1 | 0.4354529915 | 0.9136919725 | 15.75330987 | 0.3978699027
2 | 0.5752478632 | 0.2914362326 | 5.024762631 | 0.1676480701
3 | 0.6202393162 | 0.1023965142 | 1.765457141 | 0.06351034393
4 | 0.6395213675 | 0.03150661974 | 0.5432175818 | 0.02014915654
5 | 0.6475555556 | 0.01575330987 | 0.2716087909 | 0.01020114333
6 | 0.6507692308 | 0.007876654935 | 0.1358043954 | 0.005125884673
7 | 0.6523760684 | 0.007876654935 | 0.1358043954 | 0.005138541179
8 | 0.653982906 | 0.007876654935 | 0.1358043954 | 0.005151197684
9 | 0.6555897436 | 0.007876654935 | 0.1358043954 | 0.005163854189
10 | 0.6555897436 | 0 | 0 | 0
11 | 0.6571965812 | 0 | 0 | 0
12 | 0.6571965812 | 0 | 0 | 0
13 | 0.6571965812 | 0 | 0 | 0
14 | 0.6588034188 | 0 | 0 | 0
15 | 0.6588034188 | 0 | 0 | 0
16 | 0.6588034188 | 0 | 0 | 0
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
