Big-Red-Sat/Perovskite-Curve-Tracer/software/curves/X031_ShuntTest_500_LongSettle/curve_0.0_0_Reverse.xlsx

Sheet: Summary
 | 0
Time | 2023-10-22 16:02
ID | X031_ShuntTest_500_LongSettle
Pixel | 0
Pixel Area | 0.058
Irradiance | 100
Panel Temperature | 0
Voc | 0.004820512821
Isc | 0
Vmp | 0.4820512821
Imp | 1.24451148
Pmp | 0.5999183544
FF | 5999183.544
Eff | 0.103434199
Dir | Reverse

Sheet: Data
 | Voltage | Current | Current Density | Power
0 | 0.004820512821 | 2.953745601 | 50.92664829 | 0.01423856854
1 | 0.01606837607 | 2.914362326 | 50.24762631 | 0.04682906986
2 | 0.02731623932 | 2.859225742 | 49.29699554 | 0.07810329462
3 | 0.04017094017 | 2.811965812 | 48.48216917 | 0.1129593104
4 | 0.05302564103 | 2.748952572 | 47.39573401 | 0.1457649723
5 | 0.06588034188 | 2.693815988 | 46.44510324 | 0.1774695182
6 | 0.07712820513 | 2.638679403 | 45.49447247 | 0.2035166063
7 | 0.08837606838 | 2.591419474 | 44.6796461 | 0.2290194646
8 | 0.1124786325 | 2.449639685 | 42.23516698 | 0.2755321218
9 | 0.1269401709 | 2.386626445 | 41.14873182 | 0.302958769
10 | 0.1365811966 | 2.331489861 | 40.19810105 | 0.318437675
11 | 0.1446153846 | 2.276353276 | 39.24747028 | 0.3291957046
12 | 0.1542564103 | 2.229093347 | 38.43264391 | 0.3438519378
13 | 0.1606837607 | 2.181833417 | 37.61781754 | 0.3505851986
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
