Big-Red-Sat/Perovskite-Curve-Tracer/software/curves/X031_ShuntTest_500_LongSettle/curve_0.0_1_Forward.xlsx

Sheet: Summary
 | 0
Time | 2023-10-22 16:05
ID | X031_ShuntTest_500_LongSettle
Pixel | 1
Pixel Area | 0.058
Irradiance | 100
Panel Temperature | 0
Voc | 0.6845128205
Isc | 2.922238981
Vmp | 0.5334700855
Imp | 1.315401374
Pmp | 0.7017272835
FF | 0.3508092405
Eff | 0.1209874627
Dir | Forward

Sheet: Data
 | Voltage | Current | Current Density | Power
0 | 0.6845128205 | 0.01575330987 | 0.2716087909 | 0.01078334257
1 | 0.6909401709 | 0.007876654935 | 0.1358043954 | 0.005442297308
2 | 0.6957606838 | 0.007876654935 | 0.1358043954 | 0.005480266824
3 | 0.6973675214 | 0 | 0 | 0
4 | 0.6973675214 | 0.007876654935 | 0.1358043954 | 0.005492923329
5 | 0.698974359 | 0.007876654935 | 0.1358043954 | 0.005505579834
6 | 0.698974359 | 0 | 0 | 0
7 | 0.7005811966 | 0 | 0 | 0
8 | 0.7005811966 | 0 | 0 | 0
9 | 0.7005811966 | 0 | 0 | 0
10 | 0.7005811966 | 0 | 0 | 0
11 | 0.7005811966 | 0 | 0 | 0
12 | 0.7005811966 | 0 | 0 | 0
13 | 0.7021880342 | 0 | 0 | 0
14 | 0.7005811966 | 0 | 0 | 0
15 | 0.7021880342 | 0 | 0 | 0
16 | 0.7021880342 | 0 | 0 | 0
17 | 0.7021880342 | 0 | 0 | 0
18 | 0.7021880342 | 0 | 0 | 0
19 | 0.7037948718 | 0.007876654935 | 0.1358043954 | 0.00554354935
20 | 0.7021880342 | 0 | 0 | 0
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
