Big-Red-Sat/Perovskite-Curve-Tracer/software/curves/X031_ShuntTest_500_LongSettle/curve_0.0_1_Reverse.xlsx

Sheet: Summary
 | 0
Time | 2023-10-22 16:03
ID | X031_ShuntTest_500_LongSettle
Pixel | 1
Pixel Area | 0.058
Irradiance | 100
Panel Temperature | 0
Voc | 0.006427350427
Isc | 0
Vmp | 0.5141880342
Imp | 1.268141445
Pmp | 0.6520631565
FF | 6520631.565
Eff | 0.1124246822
Dir | Reverse

Sheet: Data
 | Voltage | Current | Current Density | Power
0 | 0.006427350427 | 2.953745601 | 50.92664829 | 0.01898475805
1 | 0.01606837607 | 2.914362326 | 50.24762631 | 0.04682906986
2 | 0.02731623932 | 2.859225742 | 49.29699554 | 0.07810329462
3 | 0.04017094017 | 2.811965812 | 48.48216917 | 0.1129593104
4 | 0.05302564103 | 2.756829227 | 47.5315384 | 0.146182637
5 | 0.06588034188 | 2.701692643 | 46.58090764 | 0.177988435
6 | 0.07712820513 | 2.646556058 | 45.63027687 | 0.2041241185
7 | 0.08837606838 | 2.591419474 | 44.6796461 | 0.2290194646
8 | 0.1140854701 | 2.45751634 | 42.37097138 | 0.2803669069
9 | 0.1269401709 | 2.386626445 | 41.14873182 | 0.302958769
10 | 0.1365811966 | 2.331489861 | 40.19810105 | 0.318437675
11 | 0.1462222222 | 2.284229931 | 39.38327468 | 0.3340051766
12 | 0.1542564103 | 2.229093347 | 38.43264391 | 0.3438519378
13 | 0.1622905983 | 2.189710072 | 37.75362193 | 0.3553693577
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
