Big-Red-Sat/Perovskite-Curve-Tracer/software/curves/X031_ShuntTest_500_LongSettle/curve_0.0_2_Forward.xlsx

Sheet: Summary
 | 0
Time | 2023-10-22 16:06
ID | X031_ShuntTest_500_LongSettle
Pixel | 2
Pixel Area | 0.058
Irradiance | 100
Panel Temperature | 0
Voc | 0.6571965812
Isc | 2.930115636
Vmp | 0.5141880342
Imp | 1.283894754
Pmp | 0.6601633199
FF | 0.3428240745
Eff | 0.1138212621
Dir | Forward

Sheet: Data
 | Voltage | Current | Current Density | Power
0 | 0.6571965812 | 0 | 0 | 0
1 | 0.6571965812 | 0 | 0 | 0
2 | 0.6571965812 | 0.007876654935 | 0.1358043954 | 0.005176510695
3 | 0.6571965812 | 0 | 0 | 0
4 | 0.6588034188 | 0 | 0 | 0
5 | 0.6588034188 | 0 | 0 | 0
6 | 0.6588034188 | 0 | 0 | 0
7 | 0.6604102564 | 0 | 0 | 0
8 | 0.6604102564 | 0 | 0 | 0
9 | 0.6604102564 | 0 | 0 | 0
10 | 0.662017094 | 0 | 0 | 0
11 | 0.662017094 | 0 | 0 | 0
12 | 0.662017094 | 0 | 0 | 0
13 | 0.662017094 | 0 | 0 | 0
14 | 0.662017094 | 0 | 0 | 0
15 | 0.6636239316 | 0 | 0 | 0
16 | 0.6636239316 | 0 | 0 | 0
17 | 0.6636239316 | 0 | 0 | 0
18 | 0.6636239316 | 0 | 0 | 0
19 | 0.6636239316 | 0 | 0 | 0
20 | 0.6636239316 | 0 | 0 | 0
21 | 0.6636239316 | 0.007876654935 | 0.1358043954 | 0.005227136716
22 | 0.6636239316 | 0 | 0 | 0
23 | 0.6636239316 | 0 | 0 | 0
24 | 0.6636239316 | 0 | 0 | 0
25 | 0.6652307692 | 0 | 0 | 0
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
