Big-Red-Sat/Perovskite-Curve-Tracer/software/curves/X031_ShuntTest_500_LongSettle/curve_0.0_2_Reverse.xlsx

Sheet: Summary
 | 0
Time | 2023-10-22 16:03
ID | X031_ShuntTest_500_LongSettle
Pixel | 2
Pixel Area | 0.058
Irradiance | 100
Panel Temperature | 0
Voc | 0.006427350427
Isc | 0
Vmp | 0.4820512821
Imp | 1.24451148
Pmp | 0.5999183544
FF | 5999183.544
Eff | 0.103434199
Dir | Reverse

Sheet: Data
 | Voltage | Current | Current Density | Power
0 | 0.006427350427 | 2.961622256 | 51.06245269 | 0.01903538407
1 | 0.01606837607 | 2.922238981 | 50.38343071 | 0.04695563491
2 | 0.02892307692 | 2.874979051 | 49.56860434 | 0.08315324026
3 | 0.04017094017 | 2.819842467 | 48.61797357 | 0.113275723
4 | 0.05302564103 | 2.764705882 | 47.6673428 | 0.1466003017
5 | 0.06588034188 | 2.717445953 | 46.85251643 | 0.1790262684
6 | 0.07712820513 | 2.662309368 | 45.90188566 | 0.2053391431
7 | 0.08837606838 | 2.615049439 | 45.08705929 | 0.231107788
8 | 0.1156923077 | 2.48902296 | 42.91418896 | 0.2879608101
9 | 0.1301538462 | 2.418133065 | 41.6919494 | 0.3147293189
10 | 0.1397948718 | 2.370873136 | 40.87712303 | 0.331435906
11 | 0.1478290598 | 2.323613206 | 40.06229665 | 0.3434975556
12 | 0.1574700855 | 2.276353276 | 39.24747028 | 0.358457545
13 | 0.1655042735 | 2.236970002 | 38.5684483 | 0.370228095
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
