Big-Red-Sat/Perovskite-Curve-Tracer/software/curves/X031_ShuntTest_500_LongSettle/curve_0.0_3_Forward.xlsx

Sheet: Summary
 | 0
Time | 2023-10-22 16:06
ID | X031_ShuntTest_500_LongSettle
Pixel | 3
Pixel Area | 0.058
Irradiance | 100
Panel Temperature | 0
Voc | 0.4804444444
Isc | 2.276353276
Vmp | 0.1671111111
Imp | 1.252388135
Pmp | 0.2092879727
FF | 0.1913645079
Eff | 0.03608413323
Dir | Forward

Sheet: Data
 | Voltage | Current | Current Density | Power
0 | 0.4804444444 | 0.007876654935 | 0.1358043954 | 0.003784295105
1 | 0.4708034188 | 0 | 0 | 0
2 | 0.465982906 | 0 | 0 | 0
3 | 0.465982906 | 0.007876654935 | 0.1358043954 | 0.003670386556
4 | 0.465982906 | 0 | 0 | 0
5 | 0.4643760684 | 0 | 0 | 0
6 | 0.465982906 | 0.007876654935 | 0.1358043954 | 0.003670386556
7 | 0.4643760684 | 0 | 0 | 0
8 | 0.465982906 | 0 | 0 | 0
9 | 0.465982906 | 0 | 0 | 0
10 | 0.4643760684 | 0 | 0 | 0
11 | 0.4643760684 | 0 | 0 | 0
12 | 0.4643760684 | 0 | 0 | 0
13 | 0.4643760684 | 0 | 0 | 0
14 | 0.4643760684 | 0 | 0 | 0
15 | 0.465982906 | 0 | 0 | 0
16 | 0.4643760684 | 0 | 0 | 0
17 | 0.4643760684 | 0 | 0 | 0
18 | 0.465982906 | 0 | 0 | 0
19 | 0.4643760684 | 0 | 0 | 0
20 | 0.465982906 | 0 | 0 | 0
21 | 0.465982906 | 0 | 0 | 0
22 | 0.465982906 | 0 | 0 | 0
23 | 0.465982906 | 0 | 0 | 0
24 | 0.465982906 | 0 | 0 | 0
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
