Big-Red-Sat/Perovskite-Curve-Tracer/software/curves/X031_ShuntTest_500_LongSettle/curve_0.0_3_Reverse.xlsx

Sheet: Summary
 | 0
Time | 2023-10-22 16:03
ID | X031_ShuntTest_500_LongSettle
Pixel | 3
Pixel Area | 0.058
Irradiance | 100
Panel Temperature | 0
Voc | 0.004820512821
Isc | 0
Vmp | 0.1671111111
Imp | 1.205128205
Pmp | 0.2013903134
FF | 2013903.134
Eff | 0.03472246783
Dir | Reverse

Sheet: Data
 | Voltage | Current | Current Density | Power
0 | 0.004820512821 | 2.355119826 | 40.60551424 | 0.01135288531
1 | 0.01285470085 | 2.284229931 | 39.38327468 | 0.02936309245
2 | 0.0224957265 | 2.213340037 | 38.16103512 | 0.04979069211
3 | 0.03052991453 | 2.150326797 | 37.07459995 | 0.06564929334
4 | 0.04017094017 | 2.087313558 | 35.98816479 | 0.08384934805
5 | 0.04820512821 | 2.040053628 | 35.17333842 | 0.0983410467
6 | 0.05784615385 | 1.977040389 | 34.08690326 | 0.1143641825
7 | 0.06427350427 | 1.929780459 | 33.27207688 | 0.1240337526
8 | 0.08355555556 | 1.811630635 | 31.23501095 | 0.1513718042
9 | 0.0931965812 | 1.748617396 | 30.14857579 | 0.1629651631
10 | 0.09962393162 | 1.701357466 | 29.33374941 | 0.1694959199
11 | 0.1060512821 | 1.661974191 | 28.65472744 | 0.1762544937
12 | 0.1108717949 | 1.622590917 | 27.97570546 | 0.1798995673
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
