Big-Red-Sat/Perovskite-Curve-Tracer/software/curves/X031_ShuntTest_500_LongSettle/curve_0.0_4_Reverse.xlsx

Sheet: Summary
 | 0
Time | 2023-10-22 16:04
ID | X031_ShuntTest_500_LongSettle
Pixel | 4
Pixel Area | 0.058
Irradiance | 100
Panel Temperature | 0
Voc | 0.004820512821
Isc | 0
Vmp | 0.1622905983
Imp | 1.236634825
Pmp | 0.2006942056
FF | 2006942.056
Eff | 0.03460244924
Dir | Reverse

Sheet: Data
 | Voltage | Current | Current Density | Power
0 | 0.004820512821 | 2.299983241 | 39.65488347 | 0.0110870987
1 | 0.01285470085 | 2.260599966 | 38.97586149 | 0.02905933632
2 | 0.02088888889 | 2.205463382 | 38.02523072 | 0.04606967953
3 | 0.03052991453 | 2.150326797 | 37.07459995 | 0.06564929334
4 | 0.04017094017 | 2.087313558 | 35.98816479 | 0.08384934805
5 | 0.04981196581 | 2.024300318 | 34.90172963 | 0.1008343783
6 | 0.05784615385 | 1.977040389 | 34.08690326 | 0.1143641825
7 | 0.06427350427 | 1.929780459 | 33.27207688 | 0.1240337526
8 | 0.08194871795 | 1.80375398 | 31.09920656 | 0.1478153262
9 | 0.0931965812 | 1.748617396 | 30.14857579 | 0.1629651631
10 | 0.09962393162 | 1.701357466 | 29.33374941 | 0.1694959199
11 | 0.1060512821 | 1.661974191 | 28.65472744 | 0.1762544937
12 | 0.1108717949 | 1.614714262 | 27.83990107 | 0.1790262684
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
