Big-Red-Sat/Perovskite-Curve-Tracer/software/curves/X031_ShuntTest_500_LongSettle/curve_0.0_5_Forward.xlsx

Sheet: Summary
 | 0
Time | 2023-10-22 16:07
ID | X031_ShuntTest_500_LongSettle
Pixel | 5
Pixel Area | 0.058
Irradiance | 100
Panel Temperature | 0
Voc | 0.4627692308
Isc | 2.276353276
Vmp | 0.1638974359
Imp | 1.2760181
Pmp | 0.2091360947
FF | 0.1985293929
Eff | 0.03605794736
Dir | Forward

Sheet: Data
 | Voltage | Current | Current Density | Power
0 | 0.4627692308 | 0 | 0 | 0
1 | 0.4643760684 | 0 | 0 | 0
2 | 0.4627692308 | 0 | 0 | 0
3 | 0.4643760684 | 0 | 0 | 0
4 | 0.4643760684 | 0 | 0 | 0
5 | 0.4643760684 | 0 | 0 | 0
6 | 0.4643760684 | 0 | 0 | 0
7 | 0.4627692308 | 0 | 0 | 0
8 | 0.4643760684 | 0.007876654935 | 0.1358043954 | 0.003657730051
9 | 0.4643760684 | 0 | 0 | 0
10 | 0.4643760684 | 0 | 0 | 0
11 | 0.4643760684 | 0 | 0 | 0
12 | 0.4643760684 | 0 | 0 | 0
13 | 0.4643760684 | 0 | 0 | 0
14 | 0.4643760684 | 0 | 0 | 0
15 | 0.4643760684 | 0 | 0 | 0
16 | 0.465982906 | 0 | 0 | 0
17 | 0.4643760684 | 0 | 0 | 0
18 | 0.465982906 | 0 | 0 | 0
19 | 0.465982906 | 0 | 0 | 0
20 | 0.4643760684 | 0 | 0 | 0
21 | 0.4643760684 | 0 | 0 | 0
22 | 0.465982906 | 0 | 0 | 0
23 | 0.4643760684 | 0 | 0 | 0
24 | 0.4643760684 | 0 | 0 | 0
25 | 0.465982906 | 0 | 0 | 0
26 | 0.4643760684 | 0 | 0 | 0
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
