Big-Red-Sat/Perovskite-Curve-Tracer/software/curves/X031_ShuntTest_500_LongSettle/curve_0.0_5_Reverse.xlsx

Sheet: Summary
 | 0
Time | 2023-10-22 16:04
ID | X031_ShuntTest_500_LongSettle
Pixel | 5
Pixel Area | 0.058
Irradiance | 100
Panel Temperature | 0
Voc | 0.004820512821
Isc | 0
Vmp | 0.1638974359
Imp | 1.22875817
Pmp | 0.2013903134
FF | 2013903.134
Eff | 0.03472246783
Dir | Reverse

Sheet: Data
 | Voltage | Current | Current Density | Power
0 | 0.004820512821 | 2.307859896 | 39.79068786 | 0.01112506822
1 | 0.01124786325 | 2.260599966 | 38.97586149 | 0.02542691928
2 | 0.02088888889 | 2.205463382 | 38.02523072 | 0.04606967953
3 | 0.03052991453 | 2.142450142 | 36.93879556 | 0.06540881973
4 | 0.04017094017 | 2.087313558 | 35.98816479 | 0.08384934805
5 | 0.04820512821 | 2.032176973 | 35.03753402 | 0.09796135154
6 | 0.05784615385 | 1.977040389 | 34.08690326 | 0.1143641825
7 | 0.06427350427 | 1.929780459 | 33.27207688 | 0.1240337526
8 | 0.08355555556 | 1.80375398 | 31.09920656 | 0.1507136659
9 | 0.0931965812 | 1.748617396 | 30.14857579 | 0.1629651631
10 | 0.09962393162 | 1.701357466 | 29.33374941 | 0.1694959199
11 | 0.1044444444 | 1.654097536 | 28.51892304 | 0.1727612983
12 | 0.1108717949 | 1.622590917 | 27.97570546 | 0.1798995673
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
