Big-Red-Sat/Perovskite-Curve-Tracer/software/curves/Other/test/curve_0.0_4_Reverse.xlsx

Sheet: Summary
 | 0
Time | 2023-10-09 21:44
ID | test
Pixel | 4
Pixel Area | 0.058
Irradiance | 100
Panel Temperature | 0
Voc | 0.03695726496
Isc | 0
Vmp | 1.23565812
Imp | 0.6222557399
Pmp | 0.7688953575
FF | 7688953.575
Eff | 0.1325681651
Dir | Reverse

Sheet: Data
 | Voltage | Current | Current Density | Power
0 | 0.03695726496 | 1.268141445 | 21.86450767 | 0.04686703937
1 | 0.03374358974 | 1.268141445 | 21.86450767 | 0.04279164464
2 | 0.03213675214 | 1.268141445 | 21.86450767 | 0.04075394728
3 | 0.03213675214 | 1.268141445 | 21.86450767 | 0.04075394728
4 | 0.03213675214 | 1.268141445 | 21.86450767 | 0.04075394728
5 | 0.03374358974 | 1.268141445 | 21.86450767 | 0.04279164464
6 | 0.03535042735 | 1.26026479 | 21.72870327 | 0.04455089889
7 | 0.03695726496 | 1.268141445 | 21.86450767 | 0.04686703937
8 | 0.04177777778 | 1.26026479 | 21.72870327 | 0.05265106232
9 | 0.0465982906 | 1.26026479 | 21.72870327 | 0.0587261849
10 | 0.05141880342 | 1.26026479 | 21.72870327 | 0.06480130748
11 | 0.05623931624 | 1.252388135 | 21.59289887 | 0.07043345236
12 | 0.06105982906 | 1.252388135 | 21.59289887 | 0.07647060542
13 | 0.06748717949 | 1.24451148 | 21.45709448 | 0.08398856961
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
