Big-Red-Sat/Perovskite-Curve-Tracer/software/curves/1. Round One/1776_test/curve_0.0_0.xlsx

Sheet: Summary
 | 0
Time | 2023-08-20 08:18
ID | 1776_test
Pixel | 0
Pixel Area | 0.111
Irradiance | 100
Panel Temperature | 0
Voc | 0.003213675214
Isc | 0
Vmp | 0.006427350427
Imp | 0.03150661974
Pmp | 0.0002025040859
FF | 2025.040859
Eff | 1.824361134e-05

Sheet: Data
 | Voltage | Current | Current Density | Power
0 | 0.003213675214 | 0.02362996481 | 0.2128825658 | 7.59390322e-05
1 | 0.003213675214 | 0.007876654935 | 0.07096085527 | 2.531301073e-05
2 | 0.004820512821 | 0.01575330987 | 0.1419217105 | 7.59390322e-05
3 | 0.004820512821 | 0.01575330987 | 0.1419217105 | 7.59390322e-05
4 | 0.003213675214 | 0.007876654935 | 0.07096085527 | 2.531301073e-05
5 | 0.004820512821 | 0.01575330987 | 0.1419217105 | 7.59390322e-05
6 | 0.003213675214 | 0.01575330987 | 0.1419217105 | 5.062602147e-05
7 | 0.004820512821 | 0.007876654935 | 0.07096085527 | 3.79695161e-05
8 | 0.006427350427 | 0.007876654935 | 0.07096085527 | 5.062602147e-05
9 | 0.003213675214 | 0.007876654935 | 0.07096085527 | 2.531301073e-05
10 | 0.003213675214 | 0.01575330987 | 0.1419217105 | 5.062602147e-05
11 | 0.001606837607 | 0.007876654935 | 0.07096085527 | 1.265650537e-05
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
