Big-Red-Sat/Perovskite-Curve-Tracer/software/curves/1. Round One/1776_test/curve_0.0_1.xlsx

Sheet: Summary
 | 0
Time | 2023-08-20 08:18
ID | 1776_test
Pixel | 1
Pixel Area | 0.111
Irradiance | 100
Panel Temperature | 0
Voc | 0.8773333333
Isc | 0.1339031339
Vmp | 0.4708034188
Imp | 0.06301323948
Pmp | 0.02966684858
FF | 0.252531567
Eff | 0.002672689061

Sheet: Data
 | Voltage | Current | Current Density | Power
0 | 0.8773333333 | 0.007876654935 | 0.07096085527 | 0.00691045193
1 | 0.8741196581 | 0.01575330987 | 0.1419217105 | 0.01377027784
2 | 0.8709059829 | 0.02362996481 | 0.2128825658 | 0.02057947773
3 | 0.8725128205 | 0.007876654935 | 0.07096085527 | 0.006872482414
4 | 0.8692991453 | 0.01575330987 | 0.1419217105 | 0.01369433881
5 | 0.8741196581 | 0.007876654935 | 0.07096085527 | 0.006885138919
6 | 0.8725128205 | 0.007876654935 | 0.07096085527 | 0.006872482414
7 | 0.8725128205 | 0.007876654935 | 0.07096085527 | 0.006872482414
8 | 0.8676923077 | 0.02362996481 | 0.2128825658 | 0.02050353869
9 | 0.8692991453 | 0.007876654935 | 0.07096085527 | 0.006847169403
10 | 0.8676923077 | 0.01575330987 | 0.1419217105 | 0.0136690258
11 | 0.8676923077 | 0.02362996481 | 0.2128825658 | 0.02050353869
12 | 0.8676923077 | 0.02362996481 | 0.2128825658 | 0.02050353869
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
