Big-Red-Sat/Perovskite-Curve-Tracer/software/curves/1. Round One/1776_test/curve_0.0_2.xlsx

Sheet: Summary
 | 0
Time | 2023-08-20 08:18
ID | 1776_test
Pixel | 2
Pixel Area | 0.111
Irradiance | 100
Panel Temperature | 0
Voc | 0.903042735
Isc | 1.118485001
Vmp | 0.4756239316
Imp | 0.7404055639
Pmp | 0.3521546053
FF | 0.3486541683
Eff | 0.03172564012

Sheet: Data
 | Voltage | Current | Current Density | Power
0 | 0.903042735 | 0.007876654935 | 0.07096085527 | 0.007112956016
1 | 0.903042735 | 0.01575330987 | 0.1419217105 | 0.01422591203
2 | 0.903042735 | 0.01575330987 | 0.1419217105 | 0.01422591203
3 | 0.8966153846 | 0.01575330987 | 0.1419217105 | 0.01412465999
4 | 0.8966153846 | 0.01575330987 | 0.1419217105 | 0.01412465999
5 | 0.895008547 | 0.007876654935 | 0.07096085527 | 0.007049673489
6 | 0.8998290598 | 0.007876654935 | 0.07096085527 | 0.007087643005
7 | 0.895008547 | 0 | 0 | 0
8 | 0.8917948718 | 0.02362996481 | 0.2128825658 | 0.02107308144
9 | 0.8934017094 | 0.01575330987 | 0.1419217105 | 0.01407403397
10 | 0.8934017094 | 0.01575330987 | 0.1419217105 | 0.01407403397
11 | 0.8901880342 | 0.01575330987 | 0.1419217105 | 0.01402340795
12 | 0.8917948718 | 0.007876654935 | 0.07096085527 | 0.007024360478
13 | 0.8853675214 | 0 | 0 | 0
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
