Big-Red-Sat/Perovskite-Curve-Tracer/software/curves/1. Round One/1776_test/curve_0.0_3.xlsx

Sheet: Summary
 | 0
Time | 2023-08-20 08:18
ID | 1776_test
Pixel | 3
Pixel Area | 0.111
Irradiance | 100
Panel Temperature | 0
Voc | 0.8853675214
Isc | 0.362326127
Vmp | 0.3792136752
Imp | 0.2599296129
Pmp | 0.09856886379
FF | 0.3072673231
Eff | 0.008880077819

Sheet: Data
 | Voltage | Current | Current Density | Power
0 | 0.8853675214 | 0.01575330987 | 0.1419217105 | 0.01394746891
1 | 0.8837606838 | 0.007876654935 | 0.07096085527 | 0.006961077952
2 | 0.8853675214 | 0.007876654935 | 0.07096085527 | 0.006973734457
3 | 0.8821538462 | 0.007876654935 | 0.07096085527 | 0.006948421446
4 | 0.8805470085 | 0.007876654935 | 0.07096085527 | 0.006935764941
5 | 0.8773333333 | 0.02362996481 | 0.2128825658 | 0.02073135579
6 | 0.8837606838 | 0.007876654935 | 0.07096085527 | 0.006961077952
7 | 0.8789401709 | 0.01575330987 | 0.1419217105 | 0.01384621687
8 | 0.8837606838 | 0.01575330987 | 0.1419217105 | 0.0139221559
9 | 0.8757264957 | 0.01575330987 | 0.1419217105 | 0.01379559085
10 | 0.8805470085 | 0.007876654935 | 0.07096085527 | 0.006935764941
11 | 0.8741196581 | 0.007876654935 | 0.07096085527 | 0.006885138919
12 | 0.8773333333 | 0.01575330987 | 0.1419217105 | 0.01382090386
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
