Big-Red-Sat/Perovskite-Curve-Tracer/software/curves/1. Round One/1776_test/curve_0.0_4.xlsx

Sheet: Summary
 | 0
Time | 2023-08-20 08:18
ID | 1776_test
Pixel | 4
Pixel Area | 0.111
Irradiance | 100
Panel Temperature | 0
Voc | 0.8853675214
Isc | 0.9136919725
Vmp | 0.4418803419
Imp | 0.5986257751
Pmp | 0.2645209622
FF | 0.3269916362
Eff | 0.02383071731

Sheet: Data
 | Voltage | Current | Current Density | Power
0 | 0.8853675214 | 0.007876654935 | 0.07096085527 | 0.006973734457
1 | 0.8805470085 | 0.007876654935 | 0.07096085527 | 0.006935764941
2 | 0.8789401709 | 0.007876654935 | 0.07096085527 | 0.006923108435
3 | 0.8773333333 | 0.007876654935 | 0.07096085527 | 0.00691045193
4 | 0.8757264957 | 0.007876654935 | 0.07096085527 | 0.006897795425
5 | 0.8741196581 | 0.007876654935 | 0.07096085527 | 0.006885138919
6 | 0.8773333333 | 0.01575330987 | 0.1419217105 | 0.01382090386
7 | 0.8773333333 | 0.007876654935 | 0.07096085527 | 0.00691045193
8 | 0.8741196581 | 0.01575330987 | 0.1419217105 | 0.01377027784
9 | 0.8676923077 | 0.007876654935 | 0.07096085527 | 0.006834512898
10 | 0.8660854701 | 0 | 0 | 0
11 | 0.8676923077 | 0.007876654935 | 0.07096085527 | 0.006834512898
12 | 0.8676923077 | 0 | 0 | 0
13 | 0.8692991453 | 0.01575330987 | 0.1419217105 | 0.01369433881
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
