Big-Red-Sat/Perovskite-Curve-Tracer/software/curves/1. Round One/1776_test/curve_0.0_5.xlsx

Sheet: Summary
 | 0
Time | 2023-08-20 08:18
ID | 1776_test
Pixel | 5
Pixel Area | 0.111
Irradiance | 100
Panel Temperature | 0
Voc | 0.976957265
Isc | 1.630467572
Vmp | 0.5527521368
Imp | 1.110608346
Pmp | 0.6138911363
FF | 0.3853928057
Eff | 0.05530550777

Sheet: Data
 | Voltage | Current | Current Density | Power
0 | 0.976957265 | 0.007876654935 | 0.07096085527 | 0.007695155263
1 | 0.9705299145 | 0.02362996481 | 0.2128825658 | 0.02293358772
2 | 0.9705299145 | 0.007876654935 | 0.07096085527 | 0.007644529241
3 | 0.9689230769 | 0.01575330987 | 0.1419217105 | 0.01526374547
4 | 0.9689230769 | 0.02362996481 | 0.2128825658 | 0.02289561821
5 | 0.9657094017 | 0.007876654935 | 0.07096085527 | 0.007606559725
6 | 0.9673162393 | 0.01575330987 | 0.1419217105 | 0.01523843246
7 | 0.9673162393 | 0.01575330987 | 0.1419217105 | 0.01523843246
8 | 0.9657094017 | 0.01575330987 | 0.1419217105 | 0.01521311945
9 | 0.9592820513 | 0.007876654935 | 0.07096085527 | 0.007555933704
10 | 0.9576752137 | 0.01575330987 | 0.1419217105 | 0.0150865544
11 | 0.9641025641 | 0 | 0 | 0
12 | 0.9560683761 | 0.01575330987 | 0.1419217105 | 0.01506124139
13 | 0.9560683761 | 0.01575330987 | 0.1419217105 | 0.01506124139
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
