Big-Red-Sat/Perovskite-Curve-Tracer/software/curves/2. Round Two/Test_Sim_0Shunt/curve_0.0_0_Forward.xlsx

Sheet: Summary
 | 0
Time | 2023-10-05 13:09
ID | Test_Sim_0Shunt
Pixel | 0
Pixel Area | 0.058
Irradiance | 100
Panel Temperature | 0
Voc | 0.003213675214
Isc | 1.378414614
Vmp | 0.9287521368
Imp | 1.2760181
Pmp | 1.185104536
FF | 267.5253893
Eff | 0.2043283684
Dir | Forward

Sheet: Data
 | Voltage | Current | Current Density | Power
0 | 0.003213675214 | 1.370537959 | 23.62996481 | 0.004404463868
1 | 0.1478290598 | 1.157868276 | 19.96324613 | 0.1711665786
2 | 0.2763760684 | 0.9845818669 | 16.97554943 | 0.2721148654
3 | 0.384034188 | 0.8349254232 | 14.39526592 | 0.320639907
4 | 0.4724102564 | 0.7088989442 | 12.22239559 | 0.334891132
5 | 0.5479316239 | 0.60650243 | 10.45693845 | 0.3323218614
6 | 0.6138119658 | 0.5198592257 | 8.963090099 | 0.3190958133
7 | 0.6700512821 | 0.4410926764 | 7.605046145 | 0.2955547133
8 | 0.7198632479 | 0.3780794369 | 6.518610981 | 0.2721654914
9 | 0.7632478632 | 0.3229428524 | 5.567980213 | 0.246485442
10 | 0.8002051282 | 0.2835595777 | 4.888958236 | 0.2269058282
11 | 0.8339487179 | 0.244176303 | 4.209936259 | 0.2036305148
12 | 0.8628717949 | 0.2047930283 | 3.530914281 | 0.1767101279
13 | 0.8885811966 | 0.1811630635 | 3.123501095 | 0.1609780918
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
