Big-Red-Sat/Perovskite-Curve-Tracer/software/curves/2. Round Two/Test_Sim_0Shunt/curve_0.0_0_Reverse.xlsx

Sheet: Summary
 | 0
Time | 2023-10-05 13:09
ID | Test_Sim_0Shunt
Pixel | 0
Pixel Area | 0.058
Irradiance | 100
Panel Temperature | 0
Voc | 0.001606837607
Isc | 0
Vmp | 0.8966153846
Imp | 1.236634825
Pmp | 1.108785809
FF | 11087858.09
Eff | 0.1911699671
Dir | Reverse

Sheet: Data
 | Voltage | Current | Current Density | Power
0 | 0.001606837607 | 1.378414614 | 23.7657692 | 0.002214888439
1 | 0.003213675214 | 1.378414614 | 23.7657692 | 0.004429776878
2 | 0.004820512821 | 1.370537959 | 23.62996481 | 0.006606695801
3 | 0.008034188034 | 1.378414614 | 23.7657692 | 0.0110744422
4 | 0.01124786325 | 1.370537959 | 23.62996481 | 0.01541562354
5 | 0.01446153846 | 1.370537959 | 23.62996481 | 0.0198200874
6 | 0.01928205128 | 1.370537959 | 23.62996481 | 0.02642678321
7 | 0.0241025641 | 1.378414614 | 23.7657692 | 0.03322332659
8 | 0.03052991453 | 1.370537959 | 23.62996481 | 0.04184240674
9 | 0.03856410256 | 1.370537959 | 23.62996481 | 0.05285356641
10 | 0.04499145299 | 1.370537959 | 23.62996481 | 0.06166249415
11 | 0.05141880342 | 1.370537959 | 23.62996481 | 0.07047142188
12 | 0.05945299145 | 1.370537959 | 23.62996481 | 0.08148258155
13 | 0.06588034188 | 1.370537959 | 23.62996481 | 0.09029150928
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
