Big-Red-Sat/Perovskite-Curve-Tracer/software/curves/2. Round Two/Test_Sim_0Shunt/curve_0.0_1_Forward.xlsx

Sheet: Summary
 | 0
Time | 2023-10-05 13:09
ID | Test_Sim_0Shunt
Pixel | 1
Pixel Area | 0.058
Irradiance | 100
Panel Temperature | 0
Voc | 1.060512821
Isc | 1.378414614
Vmp | 0.94
Imp | 1.268141445
Pmp | 1.192052958
FF | 0.8154544897
Eff | 0.2055263721
Dir | Forward

Sheet: Data
 | Voltage | Current | Current Density | Power
0 | 1.060512821 | 0.01575330987 | 0.2716087909 | 0.01670658708
1 | 1.063726496 | 0.01575330987 | 0.2716087909 | 0.01675721311
2 | 1.065333333 | 0.007876654935 | 0.1358043954 | 0.008391263058
3 | 1.066940171 | 0.007876654935 | 0.1358043954 | 0.008403919563
4 | 1.070153846 | 0.007876654935 | 0.1358043954 | 0.008429232574
5 | 1.071760684 | 0.007876654935 | 0.1358043954 | 0.008441889079
6 | 1.073367521 | 0.007876654935 | 0.1358043954 | 0.008454545585
7 | 1.074974359 | 0.007876654935 | 0.1358043954 | 0.00846720209
8 | 1.074974359 | 0.007876654935 | 0.1358043954 | 0.00846720209
9 | 1.076581197 | 0.007876654935 | 0.1358043954 | 0.008479858595
10 | 1.078188034 | 0.007876654935 | 0.1358043954 | 0.008492515101
11 | 1.078188034 | 0 | 0 | 0
12 | 1.081401709 | 0.007876654935 | 0.1358043954 | 0.008517828112
13 | 1.079794872 | 0.007876654935 | 0.1358043954 | 0.008505171606
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
