Big-Red-Sat/Perovskite-Curve-Tracer/software/curves/2. Round Two/Test_Sim_0Shunt/curve_0.0_1_Reverse.xlsx

Sheet: Summary
 | 0
Time | 2023-10-05 13:09
ID | Test_Sim_0Shunt
Pixel | 1
Pixel Area | 0.058
Irradiance | 100
Panel Temperature | 0
Voc | 0.004820512821
Isc | 0
Vmp | 0.9158974359
Imp | 1.24451148
Pmp | 1.139844873
FF | 11398448.73
Eff | 0.1965249782
Dir | Reverse

Sheet: Data
 | Voltage | Current | Current Density | Power
0 | 0.004820512821 | 1.378414614 | 23.7657692 | 0.006644665317
1 | 0.004820512821 | 1.370537959 | 23.62996481 | 0.006606695801
2 | 0.006427350427 | 1.370537959 | 23.62996481 | 0.008808927735
3 | 0.009641025641 | 1.370537959 | 23.62996481 | 0.0132133916
4 | 0.01285470085 | 1.370537959 | 23.62996481 | 0.01761785547
5 | 0.01606837607 | 1.370537959 | 23.62996481 | 0.02202231934
6 | 0.01928205128 | 1.378414614 | 23.7657692 | 0.02657866127
7 | 0.0241025641 | 1.378414614 | 23.7657692 | 0.03322332659
8 | 0.03052991453 | 1.378414614 | 23.7657692 | 0.04208288034
9 | 0.03856410256 | 1.370537959 | 23.62996481 | 0.05285356641
10 | 0.04499145299 | 1.370537959 | 23.62996481 | 0.06166249415
11 | 0.05302564103 | 1.370537959 | 23.62996481 | 0.07267365381
12 | 0.05945299145 | 1.370537959 | 23.62996481 | 0.08148258155
13 | 0.06588034188 | 1.378414614 | 23.7657692 | 0.090810426
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
