Big-Red-Sat/Perovskite-Curve-Tracer/software/curves/2. Round Two/Test_Sim_0Shunt/curve_0.0_2_Forward.xlsx

Sheet: Summary
 | 0
Time | 2023-10-05 13:09
ID | Test_Sim_0Shunt
Pixel | 2
Pixel Area | 0.058
Irradiance | 100
Panel Temperature | 0
Voc | 1.074974359
Isc | 1.394167924
Vmp | 0.9367863248
Imp | 1.283894754
Pmp | 1.202735048
FF | 0.802521629
Eff | 0.2073681118
Dir | Forward

Sheet: Data
 | Voltage | Current | Current Density | Power
0 | 1.074974359 | 0 | 0 | 0
1 | 1.074974359 | 0.007876654935 | 0.1358043954 | 0.00846720209
2 | 1.074974359 | 0.007876654935 | 0.1358043954 | 0.00846720209
3 | 1.076581197 | 0 | 0 | 0
4 | 1.076581197 | 0 | 0 | 0
5 | 1.078188034 | 0 | 0 | 0
6 | 1.078188034 | 0 | 0 | 0
7 | 1.079794872 | 0 | 0 | 0
8 | 1.079794872 | 0 | 0 | 0
9 | 1.081401709 | 0 | 0 | 0
10 | 1.081401709 | 0.007876654935 | 0.1358043954 | 0.008517828112
11 | 1.081401709 | 0 | 0 | 0
12 | 1.083008547 | 0 | 0 | 0
13 | 1.081401709 | 0 | 0 | 0
14 | 1.083008547 | 0 | 0 | 0
15 | 1.083008547 | 0 | 0 | 0
16 | 1.084615385 | 0.007876654935 | 0.1358043954 | 0.008543141122
17 | 1.084615385 | 0 | 0 | 0
18 | 1.084615385 | 0 | 0 | 0
19 | 1.084615385 | 0 | 0 | 0
20 | 1.084615385 | 0 | 0 | 0
21 | 1.086222222 | 0 | 0 | 0
22 | 1.084615385 | 0 | 0 | 0
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
