Big-Red-Sat/Perovskite-Curve-Tracer/software/curves/2. Round Two/Test_Sim_0Shunt/curve_0.0_2_Reverse.xlsx

Sheet: Summary
 | 0
Time | 2023-10-05 13:09
ID | Test_Sim_0Shunt
Pixel | 2
Pixel Area | 0.058
Irradiance | 100
Panel Temperature | 0
Voc | 0.004820512821
Isc | 0.007876654935
Vmp | 0.8757264957
Imp | 1.323278029
Pmp | 1.158829631
FF | 30439.83087
Eff | 0.1997982123
Dir | Reverse

Sheet: Data
 | Voltage | Current | Current Density | Power
0 | 0.004820512821 | 1.386291269 | 23.9015736 | 0.006682634833
1 | 0.006427350427 | 1.386291269 | 23.9015736 | 0.008910179778
2 | 0.008034188034 | 1.386291269 | 23.9015736 | 0.01113772472
3 | 0.009641025641 | 1.386291269 | 23.9015736 | 0.01336526967
4 | 0.01285470085 | 1.386291269 | 23.9015736 | 0.01782035956
5 | 0.01606837607 | 1.394167924 | 24.03737799 | 0.0224020145
6 | 0.02088888889 | 1.394167924 | 24.03737799 | 0.02912261885
7 | 0.0241025641 | 1.394167924 | 24.03737799 | 0.03360302175
8 | 0.03213675214 | 1.394167924 | 24.03737799 | 0.044804029
9 | 0.03856410256 | 1.394167924 | 24.03737799 | 0.0537648348
10 | 0.0465982906 | 1.386291269 | 23.9015736 | 0.06459880339
11 | 0.05302564103 | 1.386291269 | 23.9015736 | 0.07350898317
12 | 0.05945299145 | 1.394167924 | 24.03737799 | 0.08288745364
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
