Big-Red-Sat/Perovskite-Curve-Tracer/software/curves/2. Round Two/Test_Sim_0Shunt/curve_0.0_3_Forward.xlsx

Sheet: Summary
 | 0
Time | 2023-10-05 13:09
ID | Test_Sim_0Shunt
Pixel | 3
Pixel Area | 0.058
Irradiance | 100
Panel Temperature | 0
Voc | 0.2619145299
Isc | 0
Vmp | 0.2297777778
Imp | 0.007876654935
Pmp | 0.001809880267
FF | 18098.80267
Eff | 0.000312048322
Dir | Forward

Sheet: Data
 | Voltage | Current | Current Density | Power
0 | 0.2619145299 | 0 | 0 | 0
1 | 0.2297777778 | 0.007876654935 | 0.1358043954 | 0.001809880267
2 | 0.2024615385 | 0 | 0 | 0
3 | 0.1783589744 | 0 | 0 | 0
4 | 0.1558632479 | 0 | 0 | 0
5 | 0.1365811966 | 0 | 0 | 0
6 | 0.1221196581 | 0 | 0 | 0
7 | 0.1060512821 | 0 | 0 | 0
8 | 0.0931965812 | 0 | 0 | 0
9 | 0.08355555556 | 0 | 0 | 0
10 | 0.07230769231 | 0 | 0 | 0
11 | 0.06427350427 | 0 | 0 | 0
12 | 0.05784615385 | 0.007876654935 | 0.1358043954 | 0.0004556341932
13 | 0.05141880342 | 0 | 0 | 0
14 | 0.04499145299 | 0 | 0 | 0
15 | 0.04017094017 | 0 | 0 | 0
16 | 0.03695726496 | 0 | 0 | 0
17 | 0.03213675214 | 0 | 0 | 0
18 | 0.02892307692 | 0.007876654935 | 0.1358043954 | 0.0002278170966
19 | 0.02570940171 | 0 | 0 | 0
20 | 0.0224957265 | 0 | 0 | 0
21 | 0.02088888889 | 0 | 0 | 0
22 | 0.01928205128 | 0 | 0 | 0
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
