Big-Red-Sat/Perovskite-Curve-Tracer/software/curves/2. Round Two/Test_Sim_0Shunt/curve_0.0_3_Reverse.xlsx

Sheet: Summary
 | 0
Time | 2023-10-05 13:09
ID | Test_Sim_0Shunt
Pixel | 3
Pixel Area | 0.058
Irradiance | 100
Panel Temperature | 0
Voc | 0.004820512821
Isc | 0.007876654935
Vmp | 0.004820512821
Imp | 0.2678062678
Pmp | 0.001290963547
FF | 33.9106897
Eff | 0.000222579922
Dir | Reverse

Sheet: Data
 | Voltage | Current | Current Density | Power
0 | 0.004820512821 | 0.2678062678 | 4.617349445 | 0.001290963547
1 | 0.004820512821 | 0.2205463382 | 3.802523072 | 0.001063146451
2 | 0.004820512821 | 0.1890397185 | 3.259305491 | 0.0009112683864
3 | 0.004820512821 | 0.1654097536 | 2.851892304 | 0.0007973598381
4 | 0.004820512821 | 0.1417797888 | 2.444479118 | 0.0006834512898
5 | 0.004820512821 | 0.126026479 | 2.172870327 | 0.0006075122576
6 | 0.004820512821 | 0.1023965142 | 1.765457141 | 0.0004936037093
7 | 0.004820512821 | 0.08664320429 | 1.49384835 | 0.0004176646771
8 | 0.004820512821 | 0.07876654935 | 1.358043954 | 0.000379695161
9 | 0.004820512821 | 0.07088989442 | 1.222239559 | 0.0003417256449
10 | 0.004820512821 | 0.05513658455 | 0.9506307681 | 0.0002657866127
11 | 0.004820512821 | 0.04725992961 | 0.8148263726 | 0.0002278170966
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
