Big-Red-Sat/Perovskite-Curve-Tracer/software/curves/2. Round Two/Test_Sim_0Shunt/curve_0.0_4_Forward.xlsx

Sheet: Summary
 | 0
Time | 2023-10-05 13:10
ID | Test_Sim_0Shunt
Pixel | 4
Pixel Area | 0.058
Irradiance | 100
Panel Temperature | 0
Voc | 0.8821538462
Isc | 1.2760181
Vmp | 0.931965812
Imp | 1.18149824
Pmp | 1.101115967
FF | 0.9782094523
Eff | 0.1898475805
Dir | Forward

Sheet: Data
 | Voltage | Current | Current Density | Power
0 | 0.8821538462 | 0.007876654935 | 0.1358043954 | 0.006948421446
1 | 0.9062564103 | 0 | 0 | 0
2 | 0.9271452991 | 0 | 0 | 0
3 | 0.9448205128 | 0 | 0 | 0
4 | 0.9608888889 | 0 | 0 | 0
5 | 0.9753504274 | 0 | 0 | 0
6 | 0.9882051282 | 0 | 0 | 0
7 | 0.9994529915 | 0.007876654935 | 0.1358043954 | 0.007872346338
8 | 1.009094017 | 0 | 0 | 0
9 | 1.017128205 | 0 | 0 | 0
10 | 1.025162393 | 0 | 0 | 0
11 | 1.031589744 | 0 | 0 | 0
12 | 1.036410256 | 0 | 0 | 0
13 | 1.041230769 | 0 | 0 | 0
14 | 1.046051282 | 0 | 0 | 0
15 | 1.050871795 | 0 | 0 | 0
16 | 1.05408547 | 0 | 0 | 0
17 | 1.057299145 | 0 | 0 | 0
18 | 1.060512821 | 0 | 0 | 0
19 | 1.062119658 | 0 | 0 | 0
20 | 1.065333333 | 0 | 0 | 0
21 | 1.066940171 | 0 | 0 | 0
22 | 1.068547009 | 0 | 0 | 0
23 | 1.070153846 | 0.007876654935 | 0.1358043954 | 0.008429232574
24 | 1.071760684 | 0 | 0 | 0
25 | 1.073367521 | 0 | 0 | 0
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
