Big-Red-Sat/Perovskite-Curve-Tracer/software/curves/2. Round Two/Test_Sim_0Shunt/curve_0.0_4_Reverse.xlsx

Sheet: Summary
 | 0
Time | 2023-10-05 13:09
ID | Test_Sim_0Shunt
Pixel | 4
Pixel Area | 0.058
Irradiance | 100
Panel Temperature | 0
Voc | 0.003213675214
Isc | 0
Vmp | 0.9303589744
Imp | 1.142114966
Pmp | 1.062576908
FF | 10625769.08
Eff | 0.1832029152
Dir | Reverse

Sheet: Data
 | Voltage | Current | Current Density | Power
0 | 0.003213675214 | 1.047595106 | 18.06198459 | 0.003366630427
1 | 0.004820512821 | 1.079101726 | 18.60520218 | 0.005201823706
2 | 0.004820512821 | 1.102731691 | 19.01261536 | 0.005315732254
3 | 0.008034188034 | 1.126361656 | 19.42002855 | 0.009049401337
4 | 0.01124786325 | 1.149991621 | 19.82744173 | 0.01293494848
5 | 0.01446153846 | 1.157868276 | 19.96324613 | 0.0167445566
6 | 0.01928205128 | 1.173621585 | 20.23485492 | 0.0226298316
7 | 0.0224957265 | 1.189374895 | 20.50646371 | 0.02675585234
8 | 0.02892307692 | 1.19725155 | 20.64226811 | 0.03462819868
9 | 0.03535042735 | 1.21300486 | 20.9138769 | 0.04288024018
10 | 0.04177777778 | 1.21300486 | 20.9138769 | 0.05067664749
11 | 0.04820512821 | 1.220881515 | 21.04968129 | 0.05885274995
12 | 0.05463247863 | 1.22875817 | 21.18548569 | 0.06713010446
13 | 0.06105982906 | 1.236634825 | 21.32129008 | 0.07550871102
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
