Big-Red-Sat/Perovskite-Curve-Tracer/software/curves/2. Round Two/Test_Sim_0Shunt/curve_0.0_5_Forward.xlsx

Sheet: Summary
 | 0
Time | 2023-10-05 13:10
ID | Test_Sim_0Shunt
Pixel | 5
Pixel Area | 0.058
Irradiance | 100
Panel Temperature | 0
Voc | 1.076581197
Isc | 1.26026479
Vmp | 0.9383931624
Imp | 1.16574493
Pmp | 1.093927072
FF | 0.8062685973
Eff | 0.1886081158
Dir | Forward

Sheet: Data
 | Voltage | Current | Current Density | Power
0 | 1.076581197 | 0.007876654935 | 0.1358043954 | 0.008479858595
1 | 1.076581197 | 0 | 0 | 0
2 | 1.076581197 | 0 | 0 | 0
3 | 1.078188034 | 0 | 0 | 0
4 | 1.078188034 | 0 | 0 | 0
5 | 1.079794872 | 0 | 0 | 0
6 | 1.079794872 | 0 | 0 | 0
7 | 1.079794872 | 0 | 0 | 0
8 | 1.081401709 | 0 | 0 | 0
9 | 1.081401709 | 0 | 0 | 0
10 | 1.081401709 | 0 | 0 | 0
11 | 1.081401709 | 0.007876654935 | 0.1358043954 | 0.008517828112
12 | 1.083008547 | 0 | 0 | 0
13 | 1.083008547 | 0.007876654935 | 0.1358043954 | 0.008530484617
14 | 1.081401709 | 0 | 0 | 0
15 | 1.083008547 | 0 | 0 | 0
16 | 1.083008547 | 0 | 0 | 0
17 | 1.083008547 | 0 | 0 | 0
18 | 1.084615385 | 0 | 0 | 0
19 | 1.084615385 | 0 | 0 | 0
20 | 1.084615385 | 0 | 0 | 0
21 | 1.084615385 | 0 | 0 | 0
22 | 1.084615385 | 0 | 0 | 0
23 | 1.084615385 | 0.007876654935 | 0.1358043954 | 0.008543141122
24 | 1.084615385 | 0 | 0 | 0
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
