Big-Red-Sat/Perovskite-Curve-Tracer/software/curves/2. Round Two/Test_Sim_0Shunt/curve_0.0_5_Reverse.xlsx

Sheet: Summary
 | 0
Time | 2023-10-05 13:09
ID | Test_Sim_0Shunt
Pixel | 5
Pixel Area | 0.058
Irradiance | 100
Panel Temperature | 0
Voc | 0.004820512821
Isc | 0
Vmp | 0.9303589744
Imp | 1.142114966
Pmp | 1.062576908
FF | 10625769.08
Eff | 0.1832029152
Dir | Reverse

Sheet: Data
 | Voltage | Current | Current Density | Power
0 | 0.004820512821 | 1.268141445 | 21.86450767 | 0.006113092092
1 | 0.006427350427 | 1.268141445 | 21.86450767 | 0.008150789456
2 | 0.006427350427 | 1.26026479 | 21.72870327 | 0.008100163435
3 | 0.009641025641 | 1.268141445 | 21.86450767 | 0.01222618418
4 | 0.01285470085 | 1.26026479 | 21.72870327 | 0.01620032687
5 | 0.01606837607 | 1.268141445 | 21.86450767 | 0.02037697364
6 | 0.01928205128 | 1.26026479 | 21.72870327 | 0.0243004903
7 | 0.0224957265 | 1.268141445 | 21.86450767 | 0.0285277631
8 | 0.02892307692 | 1.268141445 | 21.86450767 | 0.03667855255
9 | 0.03535042735 | 1.26026479 | 21.72870327 | 0.04455089889
10 | 0.04338461538 | 1.26026479 | 21.72870327 | 0.05467610318
11 | 0.04820512821 | 1.26026479 | 21.72870327 | 0.06075122576
12 | 0.05623931624 | 1.268141445 | 21.86450767 | 0.07131940774
13 | 0.06105982906 | 1.26026479 | 21.72870327 | 0.07695155263
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
