Big-Red-Sat/Perovskite-Curve-Tracer/software/curves/2. Round Two/Test_Sim_400Shunt/curve_0.0_0_Forward.xlsx

Sheet: Summary
 | 0
Time | 2023-10-05 12:49
ID | Test_Sim_400Shunt
Pixel | 0
Pixel Area | 0.058
Irradiance | 100
Panel Temperature | 0
Voc | 0.008034188034
Isc | 3.158538629
Vmp | 0.9287521368
Imp | 1.2760181
Pmp | 1.185104536
FF | 46.70106285
Eff | 0.2043283684
Dir | Forward

Sheet: Data
 | Voltage | Current | Current Density | Power
0 | 0.008034188034 | 4.001340707 | 68.98863288 | 0.03214752363
1 | 0.1526495726 | 3.410591587 | 58.80330323 | 0.5206253482
2 | 0.2844102564 | 2.930115636 | 50.5192351 | 0.8333549393
3 | 0.3904615385 | 2.528406234 | 43.59321094 | 0.9872453881
4 | 0.4788376068 | 2.189710072 | 37.75362193 | 1.048515531
5 | 0.555965812 | 1.890397185 | 32.59305491 | 1.050996206
6 | 0.6218461538 | 1.646220882 | 28.38311865 | 1.023696124
7 | 0.6764786325 | 1.425674543 | 24.58059557 | 0.9644383654
8 | 0.7278974359 | 1.24451148 | 21.45709448 | 0.9058767151
9 | 0.7696752137 | 1.079101726 | 18.60520218 | 0.8305578517
10 | 0.8066324786 | 0.9373219373 | 16.16072306 | 0.7560743176
11 | 0.8403760684 | 0.8112954584 | 13.98785273 | 0.6817932876
12 | 0.8676923077 | 0.7088989442 | 12.22239559 | 0.6151061608
13 | 0.8934017094 | 0.6222557399 | 10.72854724 | 0.5559243417
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
