Big-Red-Sat/Perovskite-Curve-Tracer/software/curves/2. Round Two/Test_Sim_400Shunt/curve_0.0_0_Reverse.xlsx

Sheet: Summary
 | 0
Time | 2023-10-05 12:48
ID | Test_Sim_400Shunt
Pixel | 0
Pixel Area | 0.058
Irradiance | 100
Panel Temperature | 0
Voc | 0.008034188034
Isc | 0
Vmp | 0.9223247863
Imp | 1.21300486
Pmp | 1.118784448
FF | 11187844.48
Eff | 0.1928938704
Dir | Reverse

Sheet: Data
 | Voltage | Current | Current Density | Power
0 | 0.008034188034 | 4.009217362 | 69.12443728 | 0.03221080616
1 | 0.009641025641 | 3.985587397 | 68.71702409 | 0.03842515029
2 | 0.01606837607 | 3.946204123 | 68.03800212 | 0.06340909189
3 | 0.0224957265 | 3.891067538 | 67.08737135 | 0.08753239111
4 | 0.03052991453 | 3.828054299 | 66.00093618 | 0.1168701706
5 | 0.03856410256 | 3.765041059 | 64.91450102 | 0.1451954296
6 | 0.04820512821 | 3.68627451 | 63.55645707 | 0.1776973353
7 | 0.05945299145 | 3.615384615 | 62.33421751 | 0.2149454306
8 | 0.07391452991 | 3.505111446 | 60.43295597 | 0.2590786649
9 | 0.08676923077 | 3.410591587 | 58.80330323 | 0.2959344085
10 | 0.09962393162 | 3.316071728 | 57.17365048 | 0.3303601031
11 | 0.1108717949 | 3.229428524 | 55.67980213 | 0.3580525368
12 | 0.1221196581 | 3.150661974 | 54.32175818 | 0.3847577631
13 | 0.1333675214 | 3.071895425 | 52.96371422 | 0.4096910787
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
