Big-Red-Sat/Perovskite-Curve-Tracer/software/curves/2. Round Two/Test_Sim_400Shunt/curve_0.0_1_Forward.xlsx

Sheet: Summary
 | 0
Time | 2023-10-05 12:49
ID | Test_Sim_400Shunt
Pixel | 1
Pixel Area | 0.058
Irradiance | 100
Panel Temperature | 0
Voc | 1.066940171
Isc | 3.260935143
Vmp | 0.9367863248
Imp | 1.283894754
Pmp | 1.202735048
FF | 0.345690724
Eff | 0.2073681118
Dir | Forward

Sheet: Data
 | Voltage | Current | Current Density | Power
0 | 1.066940171 | 0.03938327468 | 0.6790219772 | 0.04201959782
1 | 1.068547009 | 0.03938327468 | 0.6790219772 | 0.04208288034
2 | 1.070153846 | 0.03150661974 | 0.5432175818 | 0.0337169303
3 | 1.071760684 | 0.03150661974 | 0.5432175818 | 0.03376755632
4 | 1.073367521 | 0.02362996481 | 0.4074131863 | 0.02536363675
5 | 1.074974359 | 0.02362996481 | 0.4074131863 | 0.02540160627
6 | 1.076581197 | 0.01575330987 | 0.2716087909 | 0.01695971719
7 | 1.076581197 | 0.02362996481 | 0.4074131863 | 0.02543957579
8 | 1.078188034 | 0.01575330987 | 0.2716087909 | 0.0169850302
9 | 1.079794872 | 0.01575330987 | 0.2716087909 | 0.01701034321
10 | 1.079794872 | 0.01575330987 | 0.2716087909 | 0.01701034321
11 | 1.079794872 | 0.01575330987 | 0.2716087909 | 0.01701034321
12 | 1.081401709 | 0.01575330987 | 0.2716087909 | 0.01703565622
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
