Big-Red-Sat/Perovskite-Curve-Tracer/software/curves/2. Round Two/Test_Sim_400Shunt/curve_0.0_1_Reverse.xlsx

Sheet: Summary
 | 0
Time | 2023-10-05 12:48
ID | Test_Sim_400Shunt
Pixel | 1
Pixel Area | 0.058
Irradiance | 100
Panel Temperature | 0
Voc | 0.009641025641
Isc | 0
Vmp | 0.886974359
Imp | 1.331154684
Pmp | 1.180700073
FF | 11807000.73
Eff | 0.203568978
Dir | Reverse

Sheet: Data
 | Voltage | Current | Current Density | Power
0 | 0.009641025641 | 4.001340707 | 68.98863288 | 0.03857702836
1 | 0.01285470085 | 3.977710742 | 68.5812197 | 0.05113228168
2 | 0.01606837607 | 3.938327468 | 67.90219772 | 0.06328252683
3 | 0.0224957265 | 3.883190883 | 66.95156695 | 0.08735520004
4 | 0.03052991453 | 3.828054299 | 66.00093618 | 0.1168701706
5 | 0.04017094017 | 3.757164404 | 64.77869662 | 0.1509288265
6 | 0.04981196581 | 3.68627451 | 63.55645707 | 0.1836205799
7 | 0.05945299145 | 3.60750796 | 62.19841311 | 0.2144771399
8 | 0.07391452991 | 3.505111446 | 60.43295597 | 0.2590786649
9 | 0.08676923077 | 3.410591587 | 58.80330323 | 0.2959344085
10 | 0.09801709402 | 3.316071728 | 57.17365048 | 0.3250317143
11 | 0.1108717949 | 3.229428524 | 55.67980213 | 0.3580525368
12 | 0.1221196581 | 3.142785319 | 54.18595378 | 0.3837958687
13 | 0.1333675214 | 3.06401877 | 52.82790983 | 0.4086405888
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
