Big-Red-Sat/Perovskite-Curve-Tracer/software/curves/2. Round Two/Test_Sim_400Shunt/curve_0.0_2_Forward.xlsx

Sheet: Summary
 | 0
Time | 2023-10-05 12:49
ID | Test_Sim_400Shunt
Pixel | 2
Pixel Area | 0.058
Irradiance | 100
Panel Temperature | 0
Voc | 1.078188034
Isc | 3.268811798
Vmp | 0.9191111111
Imp | 1.323278029
Pmp | 1.21623954
FF | 0.345091833
Eff | 0.2096964724
Dir | Forward

Sheet: Data
 | Voltage | Current | Current Density | Power
0 | 1.078188034 | 0.007876654935 | 0.1358043954 | 0.008492515101
1 | 1.079794872 | 0 | 0 | 0
2 | 1.079794872 | 0.007876654935 | 0.1358043954 | 0.008505171606
3 | 1.079794872 | 0 | 0 | 0
4 | 1.081401709 | 0.007876654935 | 0.1358043954 | 0.008517828112
5 | 1.079794872 | 0 | 0 | 0
6 | 1.079794872 | 0 | 0 | 0
7 | 1.081401709 | 0.007876654935 | 0.1358043954 | 0.008517828112
8 | 1.081401709 | 0.007876654935 | 0.1358043954 | 0.008517828112
9 | 1.081401709 | 0.007876654935 | 0.1358043954 | 0.008517828112
10 | 1.083008547 | 0 | 0 | 0
11 | 1.083008547 | 0 | 0 | 0
12 | 1.081401709 | 0 | 0 | 0
13 | 1.081401709 | 0.007876654935 | 0.1358043954 | 0.008517828112
14 | 1.083008547 | 0.007876654935 | 0.1358043954 | 0.008530484617
15 | 1.083008547 | 0.007876654935 | 0.1358043954 | 0.008530484617
16 | 1.083008547 | 0 | 0 | 0
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
