Big-Red-Sat/Perovskite-Curve-Tracer/software/curves/2. Round Two/Test_Sim_400Shunt/curve_0.0_2_Reverse.xlsx

Sheet: Summary
 | 0
Time | 2023-10-05 12:48
ID | Test_Sim_400Shunt
Pixel | 2
Pixel Area | 0.058
Irradiance | 100
Panel Temperature | 0
Voc | 0.01124786325
Isc | 0
Vmp | 0.8917948718
Imp | 1.331154684
Pmp | 1.187116921
FF | 11871169.21
Eff | 0.2046753312
Dir | Reverse

Sheet: Data
 | Voltage | Current | Current Density | Power
0 | 0.01124786325 | 3.993464052 | 68.85282849 | 0.04491793755
1 | 0.01285470085 | 3.969834087 | 68.4454153 | 0.05103102964
2 | 0.01767521368 | 3.938327468 | 67.90219772 | 0.06961077952
3 | 0.0241025641 | 3.891067538 | 67.08737135 | 0.09378470477
4 | 0.03213675214 | 3.820177644 | 65.86513179 | 0.1227681021
5 | 0.04017094017 | 3.757164404 | 64.77869662 | 0.1509288265
6 | 0.04981196581 | 3.68627451 | 63.55645707 | 0.1836205799
7 | 0.05945299145 | 3.60750796 | 62.19841311 | 0.2144771399
8 | 0.07391452991 | 3.505111446 | 60.43295597 | 0.2590786649
9 | 0.08676923077 | 3.402714932 | 58.66749883 | 0.2952509572
10 | 0.09962393162 | 3.316071728 | 57.17365048 | 0.3303601031
11 | 0.1108717949 | 3.229428524 | 55.67980213 | 0.3580525368
12 | 0.1221196581 | 3.142785319 | 54.18595378 | 0.3837958687
13 | 0.1333675214 | 3.06401877 | 52.82790983 | 0.4086405888
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
