Big-Red-Sat/Perovskite-Curve-Tracer/software/curves/2. Round Two/Test_Sim_400Shunt/curve_0.0_3_Forward.xlsx

Sheet: Summary
 | 0
Time | 2023-10-05 12:49
ID | Test_Sim_400Shunt
Pixel | 3
Pixel Area | 0.058
Irradiance | 100
Panel Temperature | 0
Voc | 0.6491623932
Isc | 2.622926094
Vmp | 0.179965812
Imp | 1.701357466
Pmp | 0.3061861778
FF | 0.1798233772
Eff | 0.05279072031
Dir | Forward

Sheet: Data
 | Voltage | Current | Current Density | Power
0 | 0.6491623932 | 0 | 0 | 0
1 | 0.6363076923 | 0.007876654935 | 0.1358043954 | 0.005011976125
2 | 0.6234529915 | 0.007876654935 | 0.1358043954 | 0.004910724082
3 | 0.6138119658 | 0 | 0 | 0
4 | 0.6057777778 | 0.007876654935 | 0.1358043954 | 0.004771502523
5 | 0.5977435897 | 0.007876654935 | 0.1358043954 | 0.004708219996
6 | 0.5913162393 | 0 | 0 | 0
7 | 0.5848888889 | 0.007876654935 | 0.1358043954 | 0.004606967953
8 | 0.5816752137 | 0 | 0 | 0
9 | 0.5768547009 | 0.007876654935 | 0.1358043954 | 0.004543685427
10 | 0.572034188 | 0.007876654935 | 0.1358043954 | 0.00450571591
11 | 0.5688205128 | 0 | 0 | 0
12 | 0.5656068376 | 0 | 0 | 0
13 | 0.564 | 0 | 0 | 0
14 | 0.5607863248 | 0 | 0 | 0
15 | 0.5591794872 | 0 | 0 | 0
16 | 0.5575726496 | 0 | 0 | 0
17 | 0.555965812 | 0 | 0 | 0
18 | 0.5543589744 | 0 | 0 | 0
19 | 0.5527521368 | 0 | 0 | 0
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
