Big-Red-Sat/Perovskite-Curve-Tracer/software/curves/2. Round Two/Test_Sim_400Shunt/curve_0.0_3_Reverse.xlsx

Sheet: Summary
 | 0
Time | 2023-10-05 12:48
ID | Test_Sim_400Shunt
Pixel | 3
Pixel Area | 0.058
Irradiance | 100
Panel Temperature | 0
Voc | 0.009641025641
Isc | 0
Vmp | 0.1863931624
Imp | 1.669850846
Pmp | 0.31124878
FF | 3112487.8
Eff | 0.05366358275
Dir | Reverse

Sheet: Data
 | Voltage | Current | Current Density | Power
0 | 0.009641025641 | 3.442098207 | 59.34652081 | 0.03318535707
1 | 0.01124786325 | 3.402714932 | 58.66749883 | 0.03827327223
2 | 0.01446153846 | 3.347578348 | 57.71686806 | 0.04841113303
3 | 0.02088888889 | 3.292441763 | 56.76623729 | 0.06877545016
4 | 0.02731623932 | 3.221551869 | 55.54399773 | 0.08800068181
5 | 0.03213675214 | 3.142785319 | 54.18595378 | 0.1009989128
6 | 0.04017094017 | 3.06401877 | 52.82790983 | 0.1230845147
7 | 0.04820512821 | 2.993128875 | 51.60567027 | 0.1442841612
8 | 0.05784615385 | 2.882855706 | 49.70440873 | 0.1667621147
9 | 0.06909401709 | 2.788335847 | 48.07475599 | 0.1926573247
10 | 0.07712820513 | 2.701692643 | 46.58090764 | 0.2083767044
11 | 0.08676923077 | 2.615049439 | 45.08705929 | 0.2269058282
12 | 0.0948034188 | 2.536282889 | 43.72901533 | 0.240448289
13 | 0.1028376068 | 2.449639685 | 42.23516698 | 0.2519150828
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
