Big-Red-Sat/Perovskite-Curve-Tracer/software/curves/2. Round Two/Test_Sim_400Shunt/curve_0.0_4_Forward.xlsx

Sheet: Summary
 | 0
Time | 2023-10-05 12:49
ID | Test_Sim_400Shunt
Pixel | 4
Pixel Area | 0.058
Irradiance | 100
Panel Temperature | 0
Voc | 0.9624957265
Isc | 3.213675214
Vmp | 0.9448205128
Imp | 1.173621585
Pmp | 1.108861748
FF | 0.358489628
Eff | 0.19118306
Dir | Forward

Sheet: Data
 | Voltage | Current | Current Density | Power
0 | 0.9624957265 | 0.007876654935 | 0.1358043954 | 0.007581246714
1 | 0.976957265 | 0.007876654935 | 0.1358043954 | 0.007695155263
2 | 0.9882051282 | 0 | 0 | 0
3 | 0.9994529915 | 0 | 0 | 0
4 | 1.009094017 | 0.007876654935 | 0.1358043954 | 0.00794828537
5 | 1.017128205 | 0 | 0 | 0
6 | 1.025162393 | 0.007876654935 | 0.1358043954 | 0.008074850424
7 | 1.031589744 | 0 | 0 | 0
8 | 1.036410256 | 0 | 0 | 0
9 | 1.041230769 | 0 | 0 | 0
10 | 1.046051282 | 0 | 0 | 0
11 | 1.050871795 | 0 | 0 | 0
12 | 1.05408547 | 0.007876654935 | 0.1358043954 | 0.00830266752
13 | 1.057299145 | 0 | 0 | 0
14 | 1.058905983 | 0 | 0 | 0
15 | 1.062119658 | 0 | 0 | 0
16 | 1.063726496 | 0.007876654935 | 0.1358043954 | 0.008378606553
17 | 1.065333333 | 0.007876654935 | 0.1358043954 | 0.008391263058
18 | 1.066940171 | 0 | 0 | 0
19 | 1.068547009 | 0 | 0 | 0
20 | 1.070153846 | 0 | 0 | 0
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
