Big-Red-Sat/Perovskite-Curve-Tracer/software/curves/2. Round Two/Test_Sim_400Shunt/curve_0.0_4_Reverse.xlsx

Sheet: Summary
 | 0
Time | 2023-10-05 12:49
ID | Test_Sim_400Shunt
Pixel | 4
Pixel Area | 0.058
Irradiance | 100
Panel Temperature | 0
Voc | 0.008034188034
Isc | 0
Vmp | 0.9287521368
Imp | 1.173621585
Pmp | 1.090003555
FF | 10900035.55
Eff | 0.1879316474
Dir | Reverse

Sheet: Data
 | Voltage | Current | Current Density | Power
0 | 0.008034188034 | 3.804424334 | 65.593523 | 0.03056546046
1 | 0.01124786325 | 3.804424334 | 65.593523 | 0.04279164464
2 | 0.01606837607 | 3.780794369 | 65.18610981 | 0.06075122576
3 | 0.0224957265 | 3.741411094 | 64.50708783 | 0.08416576069
4 | 0.03052991453 | 3.694151165 | 63.69226146 | 0.1127821193
5 | 0.03856410256 | 3.63901458 | 62.74163069 | 0.1403353315
6 | 0.04820512821 | 3.576001341 | 61.65519553 | 0.1723816031
7 | 0.05784615385 | 3.512988101 | 60.56876037 | 0.2032128502
8 | 0.0707008547 | 3.410591587 | 58.80330323 | 0.2411317402
9 | 0.08516239316 | 3.323948383 | 57.30945488 | 0.283075399
10 | 0.09641025641 | 3.237305178 | 55.81560653 | 0.3121094223
11 | 0.1092649573 | 3.150661974 | 54.32175818 | 0.344256946
12 | 0.1205128205 | 3.071895425 | 52.96371422 | 0.370202782
13 | 0.1301538462 | 2.993128875 | 51.60567027 | 0.3895672352
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
