Big-Red-Sat/Perovskite-Curve-Tracer/software/curves/2. Round Two/Test_Sim_400Shunt/curve_0.0_5_Forward.xlsx

Sheet: Summary
 | 0
Time | 2023-10-05 12:49
ID | Test_Sim_400Shunt
Pixel | 5
Pixel Area | 0.058
Irradiance | 100
Panel Temperature | 0
Voc | 1.076581197
Isc | 3.245181833
Vmp | 0.9223247863
Imp | 1.189374895
Pmp | 1.096989946
FF | 0.313990717
Eff | 0.1891361976
Dir | Forward

Sheet: Data
 | Voltage | Current | Current Density | Power
0 | 1.076581197 | 0 | 0 | 0
1 | 1.076581197 | 0 | 0 | 0
2 | 1.076581197 | 0.007876654935 | 0.1358043954 | 0.008479858595
3 | 1.076581197 | 0.007876654935 | 0.1358043954 | 0.008479858595
4 | 1.076581197 | 0 | 0 | 0
5 | 1.078188034 | 0 | 0 | 0
6 | 1.078188034 | 0 | 0 | 0
7 | 1.078188034 | 0.007876654935 | 0.1358043954 | 0.008492515101
8 | 1.078188034 | 0 | 0 | 0
9 | 1.078188034 | 0 | 0 | 0
10 | 1.078188034 | 0 | 0 | 0
11 | 1.079794872 | 0.007876654935 | 0.1358043954 | 0.008505171606
12 | 1.079794872 | 0 | 0 | 0
13 | 1.079794872 | 0.007876654935 | 0.1358043954 | 0.008505171606
14 | 1.079794872 | 0 | 0 | 0
15 | 1.079794872 | 0 | 0 | 0
16 | 1.079794872 | 0 | 0 | 0
17 | 1.079794872 | 0 | 0 | 0
18 | 1.079794872 | 0 | 0 | 0
19 | 1.079794872 | 0 | 0 | 0
20 | 1.081401709 | 0.007876654935 | 0.1358043954 | 0.008517828112
21 | 1.081401709 | 0 | 0 | 0
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
