Big-Red-Sat/Perovskite-Curve-Tracer/software/curves/2. Round Two/Test_Sim_400Shunt/curve_0.0_5_Reverse.xlsx

Sheet: Summary
 | 0
Time | 2023-10-05 12:49
ID | Test_Sim_400Shunt
Pixel | 5
Pixel Area | 0.058
Irradiance | 100
Panel Temperature | 0
Voc | 0.009641025641
Isc | 0
Vmp | 0.9335726496
Imp | 1.149991621
Pmp | 1.073600724
FF | 10736007.24
Eff | 0.1851035731
Dir | Reverse

Sheet: Data
 | Voltage | Current | Current Density | Power
0 | 0.009641025641 | 3.969834087 | 68.4454153 | 0.03827327223
1 | 0.01285470085 | 3.954080778 | 68.17380651 | 0.05082852555
2 | 0.01606837607 | 3.914697503 | 67.49478453 | 0.06290283167
3 | 0.0241025641 | 3.867437573 | 66.67995816 | 0.09321516202
4 | 0.03213675214 | 3.804424334 | 65.593523 | 0.1222618418
5 | 0.04017094017 | 3.741411094 | 64.50708783 | 0.1502960012
6 | 0.04981196581 | 3.6705212 | 63.28484827 | 0.1828358765
7 | 0.05945299145 | 3.599631306 | 62.06260872 | 0.2140088492
8 | 0.07391452991 | 3.489358136 | 60.16134718 | 0.2579142664
9 | 0.08516239316 | 3.394838277 | 58.53169443 | 0.2891125521
10 | 0.09801709402 | 3.300318418 | 56.90204169 | 0.3234876207
11 | 0.1108717949 | 3.213675214 | 55.40819334 | 0.3563059391
12 | 0.1221196581 | 3.134908664 | 54.05014938 | 0.3828339743
13 | 0.1317606838 | 3.04826546 | 52.55630104 | 0.4016415413
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
