Big-Red-Sat/Perovskite-Curve-Tracer/software/curves/Other/Test_New_2/curve_0.0_0_Forward.xlsx

Sheet: Summary
 | 0
Time | 2023-10-05 08:49
ID | Test_New_2
Pixel | 0
Pixel Area | 0.058
Irradiance | 100
Panel Temperature | 0
Voc | 0.003213675214
Isc | 0.1575330987
Vmp | 0.4852649573
Imp | 0.1339031339
Pmp | 0.06497849855
FF | 128.3246524
Eff | 0.01120318941
Dir | Forward

Sheet: Data
 | Voltage | Current | Current Density | Power
0 | 0.003213675214 | 0.1811630635 | 3.123501095 | 0.0005821992469
1 | 0.1446153846 | 0.1496564438 | 2.580283513 | 0.02164262418
2 | 0.2747692308 | 0.126026479 | 2.172870327 | 0.03462819868
3 | 0.3808205128 | 0.09451985923 | 1.629652745 | 0.03599510126
4 | 0.4675897436 | 0.07088989442 | 1.222239559 | 0.03314738755
5 | 0.5382905983 | 0.06301323948 | 1.086435164 | 0.03391943438
6 | 0.6025641026 | 0.05513658455 | 0.9506307681 | 0.03322332659
7 | 0.653982906 | 0.03938327468 | 0.6790219772 | 0.02575598842
8 | 0.7021880342 | 0.03150661974 | 0.5432175818 | 0.02212357138
9 | 0.743965812 | 0.03150661974 | 0.5432175818 | 0.02343984794
10 | 0.7777094017 | 0.03150661974 | 0.5432175818 | 0.02450299439
11 | 0.8098461538 | 0.02362996481 | 0.4074131863 | 0.01913663611
12 | 0.8339487179 | 0.01575330987 | 0.2716087909 | 0.01313745257
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
