Big-Red-Sat/Perovskite-Curve-Tracer/software/curves/Other/Test_New_2/curve_0.0_0_Reverse.xlsx

Sheet: Summary
 | 0
Time | 2023-10-05 08:49
ID | Test_New_2
Pixel | 0
Pixel Area | 0.058
Irradiance | 100
Panel Temperature | 0
Voc | 0.001606837607
Isc | 0
Vmp | 0.5864957265
Imp | 0.07088989442
Pmp | 0.04157662013
FF | 415766.2013
Eff | 0.007168382781
Dir | Reverse

Sheet: Data
 | Voltage | Current | Current Density | Power
0 | 0.001606837607 | 0.1339031339 | 2.308674722 | 0.0002151605912
1 | 0.004820512821 | 0.1417797888 | 2.444479118 | 0.0006834512898
2 | 0.003213675214 | 0.1339031339 | 2.308674722 | 0.0004303211825
3 | 0.003213675214 | 0.1339031339 | 2.308674722 | 0.0004303211825
4 | 0.001606837607 | 0.1339031339 | 2.308674722 | 0.0002151605912
5 | 0.003213675214 | 0.126026479 | 2.172870327 | 0.0004050081717
6 | 0.001606837607 | 0.1339031339 | 2.308674722 | 0.0002151605912
7 | 0.001606837607 | 0.1339031339 | 2.308674722 | 0.0002151605912
8 | 0.006427350427 | 0.1339031339 | 2.308674722 | 0.0008606423649
9 | 0.004820512821 | 0.126026479 | 2.172870327 | 0.0006075122576
10 | 0.004820512821 | 0.1417797888 | 2.444479118 | 0.0006834512898
11 | 0.003213675214 | 0.1339031339 | 2.308674722 | 0.0004303211825
12 | 0.006427350427 | 0.1339031339 | 2.308674722 | 0.0008606423649
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
