Big-Red-Sat/Perovskite-Curve-Tracer/software/curves/Other/Test_New_2/curve_0.0_1_Forward.xlsx

Sheet: Summary
 | 0
Time | 2023-10-05 08:49
ID | Test_New_2
Pixel | 1
Pixel Area | 0.058
Irradiance | 100
Panel Temperature | 0
Voc | 0.9962393162
Isc | 0.1496564438
Vmp | 0.5222222222
Imp | 0.126026479
Pmp | 0.06581382791
FF | 0.4414258499
Eff | 0.01134721171
Dir | Forward

Sheet: Data
 | Voltage | Current | Current Density | Power
0 | 0.9962393162 | 0.007876654935 | 0.1358043954 | 0.007847033327
1 | 0.9994529915 | 0 | 0 | 0
2 | 0.9994529915 | 0.01575330987 | 0.2716087909 | 0.01574469268
3 | 1.002666667 | 0 | 0 | 0
4 | 1.004273504 | 0.007876654935 | 0.1358043954 | 0.007910315854
5 | 1.001059829 | 0.007876654935 | 0.1358043954 | 0.007885002843
6 | 1.004273504 | 0 | 0 | 0
7 | 1.005880342 | 0 | 0 | 0
8 | 1.009094017 | 0.007876654935 | 0.1358043954 | 0.00794828537
9 | 1.010700855 | 0.007876654935 | 0.1358043954 | 0.007960941875
10 | 1.007487179 | 0.007876654935 | 0.1358043954 | 0.007935628865
11 | 1.007487179 | 0.007876654935 | 0.1358043954 | 0.007935628865
12 | 1.009094017 | 0.007876654935 | 0.1358043954 | 0.00794828537
13 | 1.012307692 | 0.007876654935 | 0.1358043954 | 0.007973598381
14 | 1.009094017 | 0.007876654935 | 0.1358043954 | 0.00794828537
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
