Big-Red-Sat/Perovskite-Curve-Tracer/software/curves/Other/Test_New_2/curve_0.0_1_Reverse.xlsx

Sheet: Summary
 | 0
Time | 2023-10-05 08:49
ID | Test_New_2
Pixel | 1
Pixel Area | 0.058
Irradiance | 100
Panel Temperature | 0
Voc | 0.006427350427
Isc | 0.007876654935
Vmp | 0.4097435897
Imp | 0.1417797888
Pmp | 0.05809335963
FF | 1145.237847
Eff | 0.01001609649
Dir | Reverse

Sheet: Data
 | Voltage | Current | Current Density | Power
0 | 0.006427350427 | 0.1811630635 | 3.123501095 | 0.001164398494
1 | 0.004820512821 | 0.1732864086 | 2.9876967 | 0.0008353293542
2 | 0.004820512821 | 0.1811630635 | 3.123501095 | 0.0008732988703
3 | 0.004820512821 | 0.1811630635 | 3.123501095 | 0.0008732988703
4 | 0.006427350427 | 0.1732864086 | 2.9876967 | 0.001113772472
5 | 0.003213675214 | 0.1811630635 | 3.123501095 | 0.0005821992469
6 | 0.004820512821 | 0.1811630635 | 3.123501095 | 0.0008732988703
7 | 0.008034188034 | 0.1811630635 | 3.123501095 | 0.001455498117
8 | 0.004820512821 | 0.1732864086 | 2.9876967 | 0.0008353293542
9 | 0.006427350427 | 0.1732864086 | 2.9876967 | 0.001113772472
10 | 0.006427350427 | 0.1732864086 | 2.9876967 | 0.001113772472
11 | 0.009641025641 | 0.1890397185 | 3.259305491 | 0.001822536773
12 | 0.009641025641 | 0.1732864086 | 2.9876967 | 0.001670658708
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
