Big-Red-Sat/Perovskite-Curve-Tracer/software/curves/Other/Test_New_2/curve_0.0_2_Forward.xlsx

Sheet: Summary
 | 0
Time | 2023-10-05 08:49
ID | Test_New_2
Pixel | 2
Pixel Area | 0.058
Irradiance | 100
Panel Temperature | 0
Voc | 1.010700855
Isc | 0.1654097536
Vmp | 0.474017094
Imp | 0.126026479
Pmp | 0.05973870533
FF | 0.3573319083
Eff | 0.01029977678
Dir | Forward

Sheet: Data
 | Voltage | Current | Current Density | Power
0 | 1.010700855 | 0.007876654935 | 0.1358043954 | 0.007960941875
1 | 1.012307692 | 0.007876654935 | 0.1358043954 | 0.007973598381
2 | 1.009094017 | 0.007876654935 | 0.1358043954 | 0.00794828537
3 | 1.012307692 | 0 | 0 | 0
4 | 1.01391453 | 0.007876654935 | 0.1358043954 | 0.007986254886
5 | 1.01391453 | 0.007876654935 | 0.1358043954 | 0.007986254886
6 | 1.01391453 | 0 | 0 | 0
7 | 1.012307692 | 0.007876654935 | 0.1358043954 | 0.007973598381
8 | 1.01391453 | 0.007876654935 | 0.1358043954 | 0.007986254886
9 | 1.012307692 | 0 | 0 | 0
10 | 1.012307692 | 0.007876654935 | 0.1358043954 | 0.007973598381
11 | 1.010700855 | 0.007876654935 | 0.1358043954 | 0.007960941875
12 | 1.01391453 | 0.007876654935 | 0.1358043954 | 0.007986254886
13 | 1.01391453 | 0.007876654935 | 0.1358043954 | 0.007986254886
14 | 1.01391453 | 0 | 0 | 0
15 | 1.012307692 | 0 | 0 | 0
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
