Big-Red-Sat/Perovskite-Curve-Tracer/software/curves/Other/Test_New_2/curve_0.0_2_Reverse.xlsx

Sheet: Summary
 | 0
Time | 2023-10-05 08:49
ID | Test_New_2
Pixel | 2
Pixel Area | 0.058
Irradiance | 100
Panel Temperature | 0
Voc | 0.004820512821
Isc | 0
Vmp | 0.4113504274
Imp | 0.1496564438
Pmp | 0.0615612421
FF | 615612.421
Eff | 0.01061400726
Dir | Reverse

Sheet: Data
 | Voltage | Current | Current Density | Power
0 | 0.004820512821 | 0.2205463382 | 3.802523072 | 0.001063146451
1 | 0.004820512821 | 0.2126696833 | 3.666718677 | 0.001025176935
2 | 0.006427350427 | 0.2205463382 | 3.802523072 | 0.001417528601
3 | 0.004820512821 | 0.2205463382 | 3.802523072 | 0.001063146451
4 | 0.006427350427 | 0.2284229931 | 3.938327468 | 0.001468154623
5 | 0.006427350427 | 0.2205463382 | 3.802523072 | 0.001417528601
6 | 0.006427350427 | 0.2205463382 | 3.802523072 | 0.001417528601
7 | 0.004820512821 | 0.2205463382 | 3.802523072 | 0.001063146451
8 | 0.006427350427 | 0.2362996481 | 4.074131863 | 0.001518780644
9 | 0.008034188034 | 0.2205463382 | 3.802523072 | 0.001771910751
10 | 0.009641025641 | 0.2284229931 | 3.938327468 | 0.002202231934
11 | 0.01285470085 | 0.2205463382 | 3.802523072 | 0.002835057202
12 | 0.01285470085 | 0.2126696833 | 3.666718677 | 0.002733805159
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
