Big-Red-Sat/Perovskite-Curve-Tracer/software/curves/Other/Test_New_2/curve_0.0_3_Forward.xlsx

Sheet: Summary
 | 0
Time | 2023-10-05 08:49
ID | Test_New_2
Pixel | 3
Pixel Area | 0.058
Irradiance | 100
Panel Temperature | 0
Voc | 0.2811965812
Isc | 0
Vmp | 0.2506666667
Imp | 0.01575330987
Pmp | 0.003948829674
FF | 39488.29674
Eff | 0.0006808327025
Dir | Forward

Sheet: Data
 | Voltage | Current | Current Density | Power
0 | 0.2811965812 | 0.007876654935 | 0.1358043954 | 0.002214888439
1 | 0.2506666667 | 0.01575330987 | 0.2716087909 | 0.003948829674
2 | 0.2217435897 | 0.007876654935 | 0.1358043954 | 0.001746597741
3 | 0.2024615385 | 0 | 0 | 0
4 | 0.1831794872 | 0.007876654935 | 0.1358043954 | 0.001442841612
5 | 0.1671111111 | 0 | 0 | 0
6 | 0.151042735 | 0.007876654935 | 0.1358043954 | 0.001189711504
7 | 0.1365811966 | 0.007876654935 | 0.1358043954 | 0.001075802956
8 | 0.1253333333 | 0.007876654935 | 0.1358043954 | 0.0009872074186
9 | 0.1140854701 | 0.007876654935 | 0.1358043954 | 0.000898611881
10 | 0.1076581197 | 0.007876654935 | 0.1358043954 | 0.0008479858595
11 | 0.09962393162 | 0.007876654935 | 0.1358043954 | 0.0007847033327
12 | 0.0948034188 | 0.007876654935 | 0.1358043954 | 0.0007467338166
13 | 0.08998290598 | 0 | 0 | 0
14 | 0.08194871795 | 0 | 0 | 0
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
