Big-Red-Sat/Perovskite-Curve-Tracer/software/curves/Other/Test_New_2/curve_0.0_3_Reverse.xlsx

Sheet: Summary
 | 0
Time | 2023-10-05 08:49
ID | Test_New_2
Pixel | 3
Pixel Area | 0.058
Irradiance | 100
Panel Temperature | 0
Voc | 0.004820512821
Isc | 0.007876654935
Vmp | 0.06105982906
Imp | 0.01575330987
Pmp | 0.0009618944078
FF | 25.2667884
Eff | 0.0001658438634
Dir | Reverse

Sheet: Data
 | Voltage | Current | Current Density | Power
0 | 0.004820512821 | 0.03150661974 | 0.5432175818 | 0.0001518780644
1 | 0.006427350427 | 0.02362996481 | 0.4074131863 | 0.0001518780644
2 | 0.006427350427 | 0.03938327468 | 0.6790219772 | 0.0002531301073
3 | 0.003213675214 | 0.03150661974 | 0.5432175818 | 0.0001012520429
4 | 0.003213675214 | 0 | 0 | 0
5 | 0.008034188034 | 0.01575330987 | 0.2716087909 | 0.0001265650537
6 | 0.004820512821 | 0 | 0 | 0
7 | 0.003213675214 | 0.007876654935 | 0.1358043954 | 2.531301073e-05
8 | 0.003213675214 | 0.01575330987 | 0.2716087909 | 5.062602147e-05
9 | 0.003213675214 | 0.007876654935 | 0.1358043954 | 2.531301073e-05
10 | 0.004820512821 | 0 | 0 | 0
11 | 0.004820512821 | 0.007876654935 | 0.1358043954 | 3.79695161e-05
12 | 0.004820512821 | 0.007876654935 | 0.1358043954 | 3.79695161e-05
13 | 0.004820512821 | 0 | 0 | 0
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
