Big-Red-Sat/Perovskite-Curve-Tracer/software/curves/Other/Test_New_2/curve_0.0_4_Forward.xlsx

Sheet: Summary
 | 0
Time | 2023-10-05 08:50
ID | Test_New_2
Pixel | 4
Pixel Area | 0.058
Irradiance | 100
Panel Temperature | 0
Voc | 0.04820512821
Isc | 0.007876654935
Vmp | 0.0465982906
Imp | 0.02362996481
Pmp | 0.001101115967
FF | 2.899236431
Eff | 0.0001898475805
Dir | Forward

Sheet: Data
 | Voltage | Current | Current Density | Power
0 | 0.04820512821 | 0 | 0 | 0
1 | 0.04981196581 | 0.007876654935 | 0.1358043954 | 0.0003923516664
2 | 0.04820512821 | 0.007876654935 | 0.1358043954 | 0.000379695161
3 | 0.0465982906 | 0.007876654935 | 0.1358043954 | 0.0003670386556
4 | 0.04820512821 | 0 | 0 | 0
5 | 0.04499145299 | 0.007876654935 | 0.1358043954 | 0.0003543821503
6 | 0.04820512821 | 0.007876654935 | 0.1358043954 | 0.000379695161
7 | 0.04820512821 | 0 | 0 | 0
8 | 0.0465982906 | 0 | 0 | 0
9 | 0.04820512821 | 0.007876654935 | 0.1358043954 | 0.000379695161
10 | 0.0465982906 | 0.007876654935 | 0.1358043954 | 0.0003670386556
11 | 0.0465982906 | 0 | 0 | 0
12 | 0.0465982906 | 0.007876654935 | 0.1358043954 | 0.0003670386556
13 | 0.0465982906 | 0.007876654935 | 0.1358043954 | 0.0003670386556
14 | 0.0465982906 | 0.007876654935 | 0.1358043954 | 0.0003670386556
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
