Big-Red-Sat/Perovskite-Curve-Tracer/software/curves/Other/Test_New_2/curve_0.0_4_Reverse.xlsx

Sheet: Summary
 | 0
Time | 2023-10-05 08:49
ID | Test_New_2
Pixel | 4
Pixel Area | 0.058
Irradiance | 100
Panel Temperature | 0
Voc | 0.001606837607
Isc | 0.007876654935
Vmp | 0.06105982906
Imp | 0.01575330987
Pmp | 0.0009618944078
FF | 75.40422555
Eff | 0.0001658438634
Dir | Reverse

Sheet: Data
 | Voltage | Current | Current Density | Power
0 | 0.001606837607 | 0 | 0 | 0
1 | 0.001606837607 | 0.007876654935 | 0.1358043954 | 1.265650537e-05
2 | 0.001606837607 | 0.007876654935 | 0.1358043954 | 1.265650537e-05
3 | 0.004820512821 | 0 | 0 | 0
4 | 0.003213675214 | 0 | 0 | 0
5 | 0.003213675214 | 0 | 0 | 0
6 | 0.004820512821 | 0 | 0 | 0
7 | 0.003213675214 | 0.007876654935 | 0.1358043954 | 2.531301073e-05
8 | 0.001606837607 | 0 | 0 | 0
9 | 0.003213675214 | 0.007876654935 | 0.1358043954 | 2.531301073e-05
10 | 0.004820512821 | 0.007876654935 | 0.1358043954 | 3.79695161e-05
11 | 0.001606837607 | 0.007876654935 | 0.1358043954 | 1.265650537e-05
12 | 0.003213675214 | 0 | 0 | 0
13 | 0.003213675214 | 0.01575330987 | 0.2716087909 | 5.062602147e-05
14 | 0.003213675214 | 0 | 0 | 0
15 | 0.003213675214 | 0.007876654935 | 0.1358043954 | 2.531301073e-05
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
