Big-Red-Sat/Perovskite-Curve-Tracer/software/curves/Other/Test_New_2/curve_0.0_5_Forward.xlsx

Sheet: Summary
 | 0
Time | 2023-10-05 08:50
ID | Test_New_2
Pixel | 5
Pixel Area | 0.058
Irradiance | 100
Panel Temperature | 0
Voc | 0.7985982906
Isc | 0.244176303
Vmp | 0.5254358974
Imp | 0.1890397185
Pmp | 0.09932825412
FF | 0.5093785925
Eff | 0.01712556105
Dir | Forward

Sheet: Data
 | Voltage | Current | Current Density | Power
0 | 0.7985982906 | 0.007876654935 | 0.1358043954 | 0.006290283167
1 | 0.8275213675 | 0.007876654935 | 0.1358043954 | 0.006518100264
2 | 0.8532307692 | 0 | 0 | 0
3 | 0.8741196581 | 0 | 0 | 0
4 | 0.8917948718 | 0 | 0 | 0
5 | 0.9062564103 | 0.007876654935 | 0.1358043954 | 0.007138269027
6 | 0.9207179487 | 0 | 0 | 0
7 | 0.931965812 | 0 | 0 | 0
8 | 0.9432136752 | 0 | 0 | 0
9 | 0.9560683761 | 0.007876654935 | 0.1358043954 | 0.007530620693
10 | 0.9624957265 | 0 | 0 | 0
11 | 0.9689230769 | 0 | 0 | 0
12 | 0.9801709402 | 0 | 0 | 0
13 | 0.9865982906 | 0.007876654935 | 0.1358043954 | 0.007771094295
14 | 0.9882051282 | 0.007876654935 | 0.1358043954 | 0.0077837508
15 | 0.993025641 | 0.007876654935 | 0.1358043954 | 0.007821720316
16 | 0.9978461538 | 0.007876654935 | 0.1358043954 | 0.007859689833
17 | 0.9994529915 | 0 | 0 | 0
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
