Big-Red-Sat/Perovskite-Curve-Tracer/software/curves/Other/Test_New_2/curve_0.0_5_Reverse.xlsx

Sheet: Summary
 | 0
Time | 2023-10-05 08:49
ID | Test_New_2
Pixel | 5
Pixel Area | 0.058
Irradiance | 100
Panel Temperature | 0
Voc | 0.003213675214
Isc | 0.01575330987
Vmp | 0.4627692308
Imp | 0.1969163734
Pmp | 0.09112683864
FF | 1796.451525
Eff | 0.0157115239
Dir | Reverse

Sheet: Data
 | Voltage | Current | Current Density | Power
0 | 0.003213675214 | 0.2520529579 | 4.345740654 | 0.0008100163435
1 | 0.001606837607 | 0.2520529579 | 4.345740654 | 0.0004050081717
2 | 0.001606837607 | 0.2756829227 | 4.75315384 | 0.0004429776878
3 | 0.003213675214 | 0.2678062678 | 4.617349445 | 0.0008606423649
4 | 0.004820512821 | 0.2756829227 | 4.75315384 | 0.001328933063
5 | 0.003213675214 | 0.2835595777 | 4.888958236 | 0.0009112683864
6 | 0.003213675214 | 0.2756829227 | 4.75315384 | 0.0008859553756
7 | 0.004820512821 | 0.2914362326 | 5.024762631 | 0.001404872096
8 | 0.006427350427 | 0.2835595777 | 4.888958236 | 0.001822536773
9 | 0.009641025641 | 0.2914362326 | 5.024762631 | 0.002809744191
10 | 0.009641025641 | 0.2914362326 | 5.024762631 | 0.002809744191
11 | 0.01124786325 | 0.2756829227 | 4.75315384 | 0.003100843815
12 | 0.01446153846 | 0.2835595777 | 4.888958236 | 0.004100707739
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
