Big-Red-Sat/Perovskite-Curve-Tracer/software/curves/Other/Test_New_CT/curve_0.0_0_Forward.xlsx

Sheet: Summary
 | 0
Time | 2023-10-04 08:29
ID | Test_New_CT
Pixel | 0
Pixel Area | 0.058
Irradiance | 100
Panel Temperature | 0
Voc | 0.9801709402
Isc | 0.01575330987
Vmp | 0.4708034188
Imp | 0.2520529579
Pmp | 0.1186673943
FF | 7.68519613
Eff | 0.02045989557
Dir | Forward

Sheet: Data
 | Voltage | Current | Current Density | Power
0 | 0.9801709402 | 0.007876654935 | 0.1358043954 | 0.007720468274
1 | 0.8468034188 | 0.06301323948 | 1.086435164 | 0.05335982662
2 | 0.7262905983 | 0.118149824 | 2.037065932 | 0.08581110638
3 | 0.6250598291 | 0.1654097536 | 2.851892304 | 0.1033909923
4 | 0.5495384615 | 0.2047930283 | 3.530914281 | 0.1125416457
5 | 0.474017094 | 0.2284229931 | 3.938327468 | 0.1082764034
6 | 0.412957265 | 0.244176303 | 4.209936259 | 0.1008343783
7 | 0.3631452991 | 0.2678062678 | 4.617349445 | 0.09725258724
8 | 0.3213675214 | 0.2914362326 | 5.024762631 | 0.09365813971
9 | 0.2811965812 | 0.3229428524 | 5.567980213 | 0.090810426
10 | 0.2506666667 | 0.3150661974 | 5.432175818 | 0.07897659349
11 | 0.2201367521 | 0.3150661974 | 5.432175818 | 0.06935764941
12 | 0.1944273504 | 0.3465728172 | 5.975393399 | 0.06738323457
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
