Big-Red-Sat/Perovskite-Curve-Tracer/software/curves/Other/Test_New_CT/curve_0.0_0_Reverse.xlsx

Sheet: Summary
 | 0
Time | 2023-10-04 08:29
ID | Test_New_CT
Pixel | 0
Pixel Area | 0.058
Irradiance | 100
Panel Temperature | 0
Voc | 0.9833846154
Isc | 0.362326127
Vmp | 0.4772307692
Imp | 0.3071895425
Pmp | 0.1466003017
FF | 0.4114448973
Eff | 0.02527591408
Dir | Reverse

Sheet: Data
 | Voltage | Current | Current Density | Power
0 | 0.9833846154 | 0 | 0 | 0
1 | 0.9833846154 | 0.007876654935 | 0.1358043954 | 0.007745781284
2 | 0.9817777778 | 0 | 0 | 0
3 | 0.9817777778 | 0.007876654935 | 0.1358043954 | 0.007733124779
4 | 0.9801709402 | 0 | 0 | 0
5 | 0.9817777778 | 0.01575330987 | 0.2716087909 | 0.01546624956
6 | 0.9833846154 | 0.007876654935 | 0.1358043954 | 0.007745781284
7 | 0.9865982906 | 0.007876654935 | 0.1358043954 | 0.007771094295
8 | 0.9817777778 | 0.01575330987 | 0.2716087909 | 0.01546624956
9 | 0.984991453 | 0 | 0 | 0
10 | 0.9833846154 | 0.007876654935 | 0.1358043954 | 0.007745781284
11 | 0.9817777778 | 0 | 0 | 0
12 | 0.9817777778 | 0.007876654935 | 0.1358043954 | 0.007733124779
13 | 0.9817777778 | 0 | 0 | 0
14 | 0.984991453 | 0.007876654935 | 0.1358043954 | 0.00775843779
15 | 0.984991453 | 0.007876654935 | 0.1358043954 | 0.00775843779
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
