Big-Red-Sat/Perovskite-Curve-Tracer/software/curves/2. Round Two/9-9-2023 Payload Test/A027/A027_plotted.png

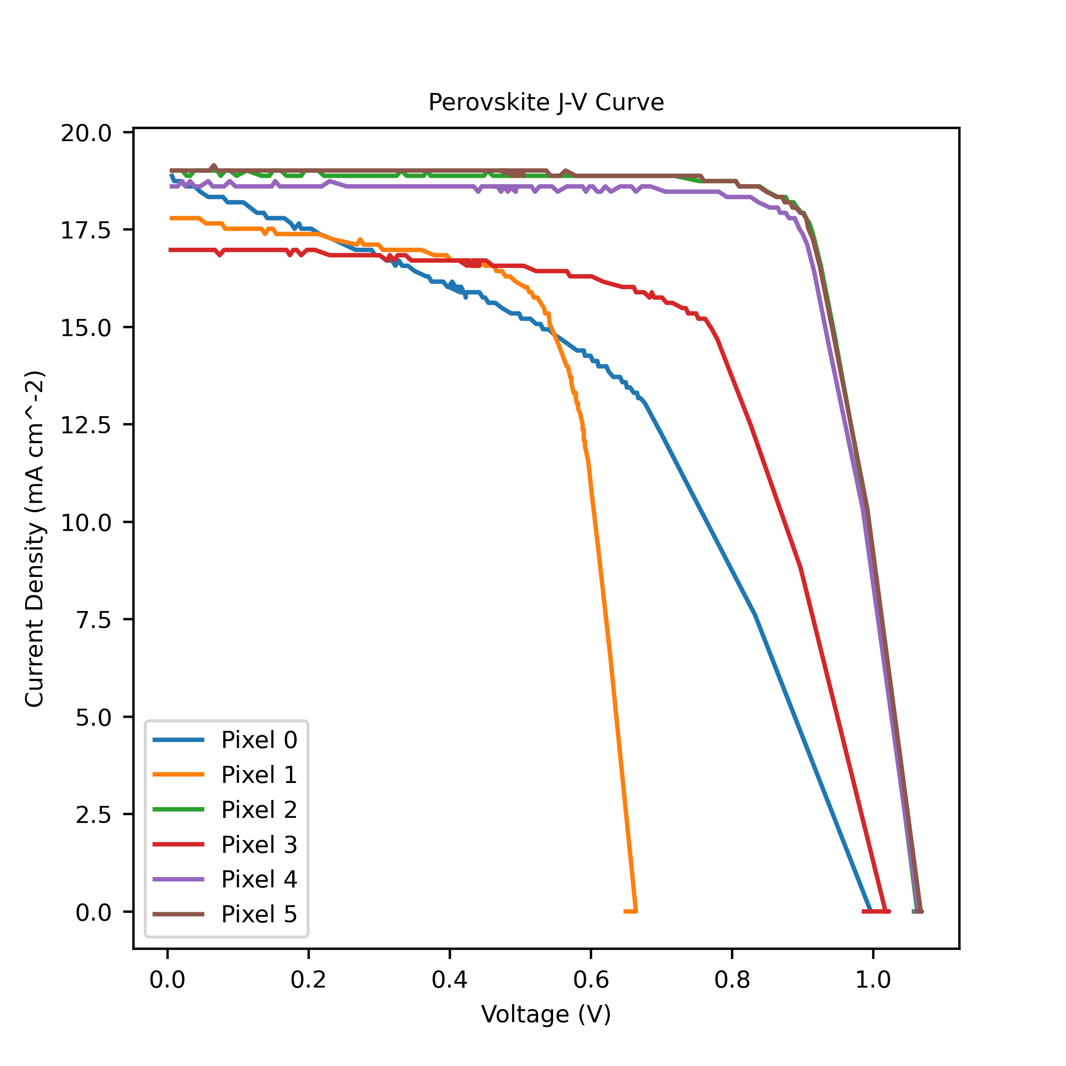
software/curves/2. Round Two/9-9-2023 Payload Test/A027/A027_plotted.png
