Big-Red-Sat/Perovskite-Curve-Tracer/software/curves/2. Round Two/Test_Sim_0Shunt/Test_Sim_0Shunt_plotted_Forward.png

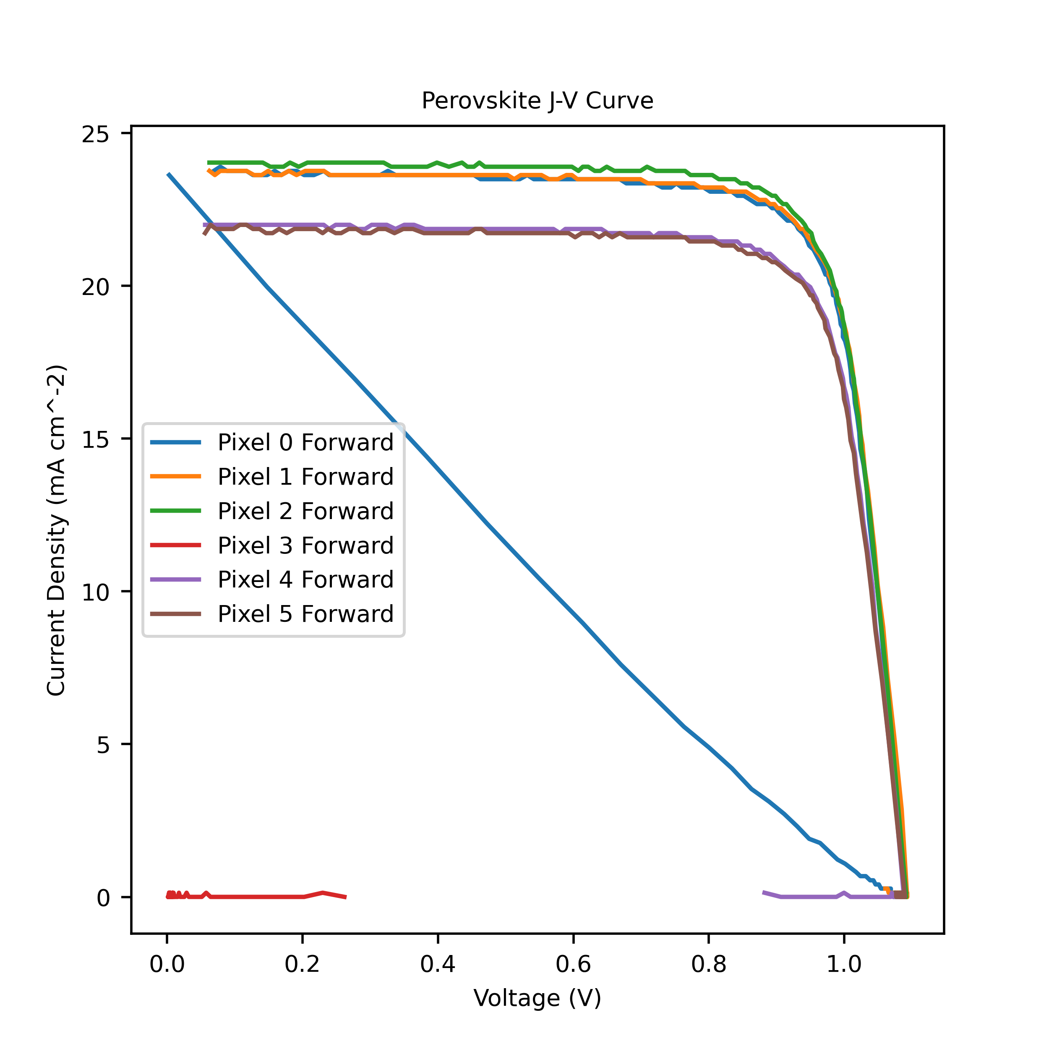
software/curves/2. Round Two/Test_Sim_0Shunt/Test_Sim_0Shunt_plotted_Forward.png
