Big-Red-Sat/Perovskite-Curve-Tracer/software/curves/2. Round Two/Test_Sim_400Shunt/Test_Sim_400Shunt_plotted_Reverse.png

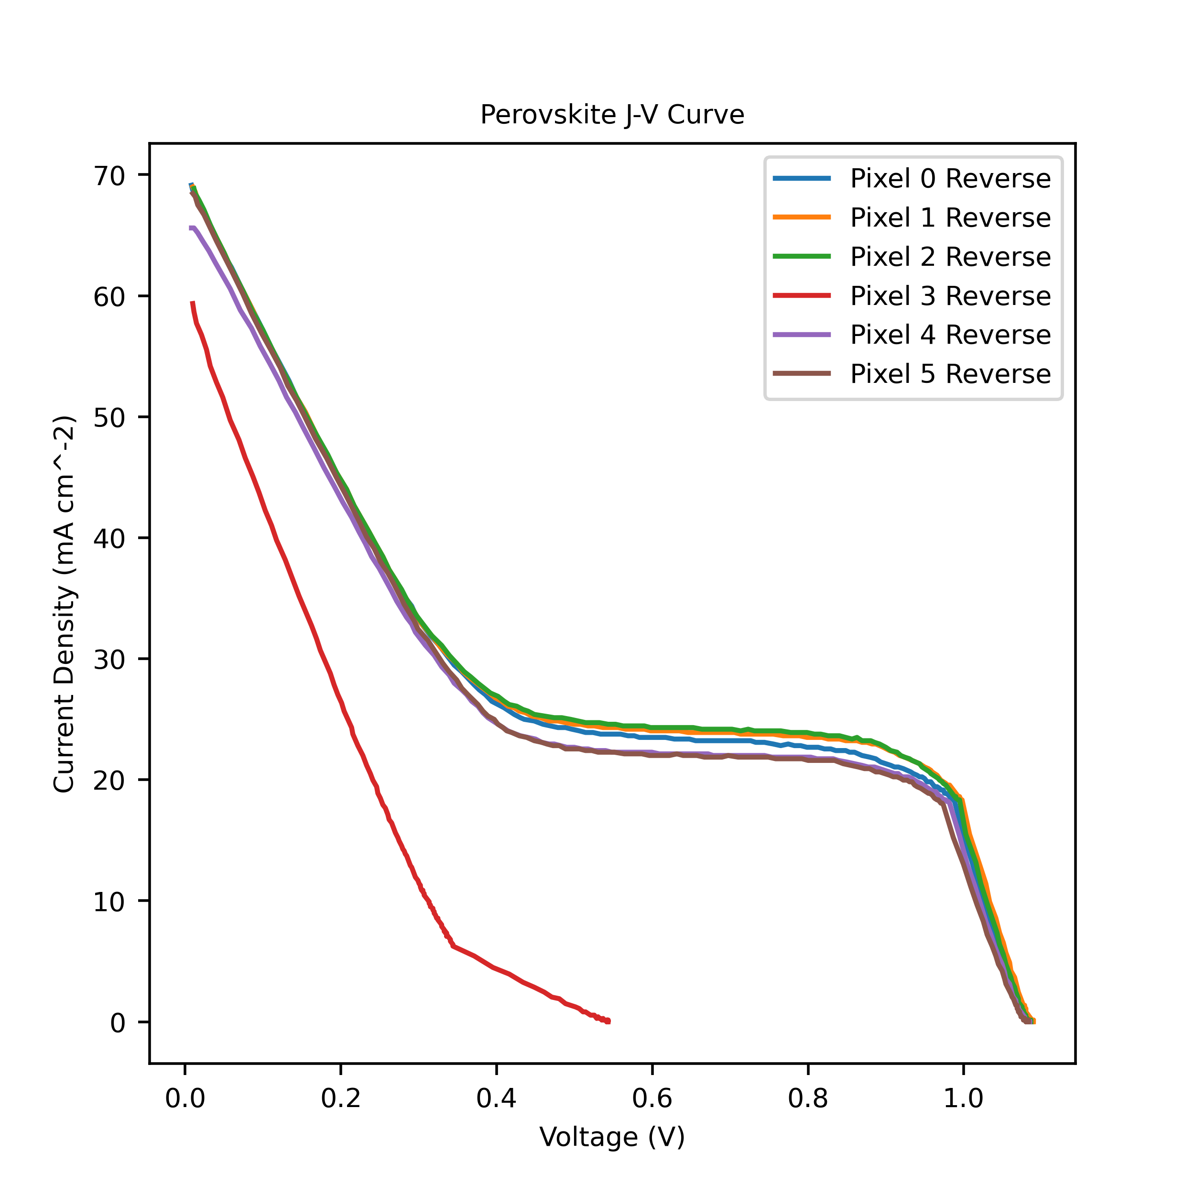
software/curves/2. Round Two/Test_Sim_400Shunt/Test_Sim_400Shunt_plotted_Reverse.png
