Big-Red-Sat/Perovskite-Curve-Tracer/software/curves/Other/Test_New_2/Test_New_2_plotted_Reverse.png

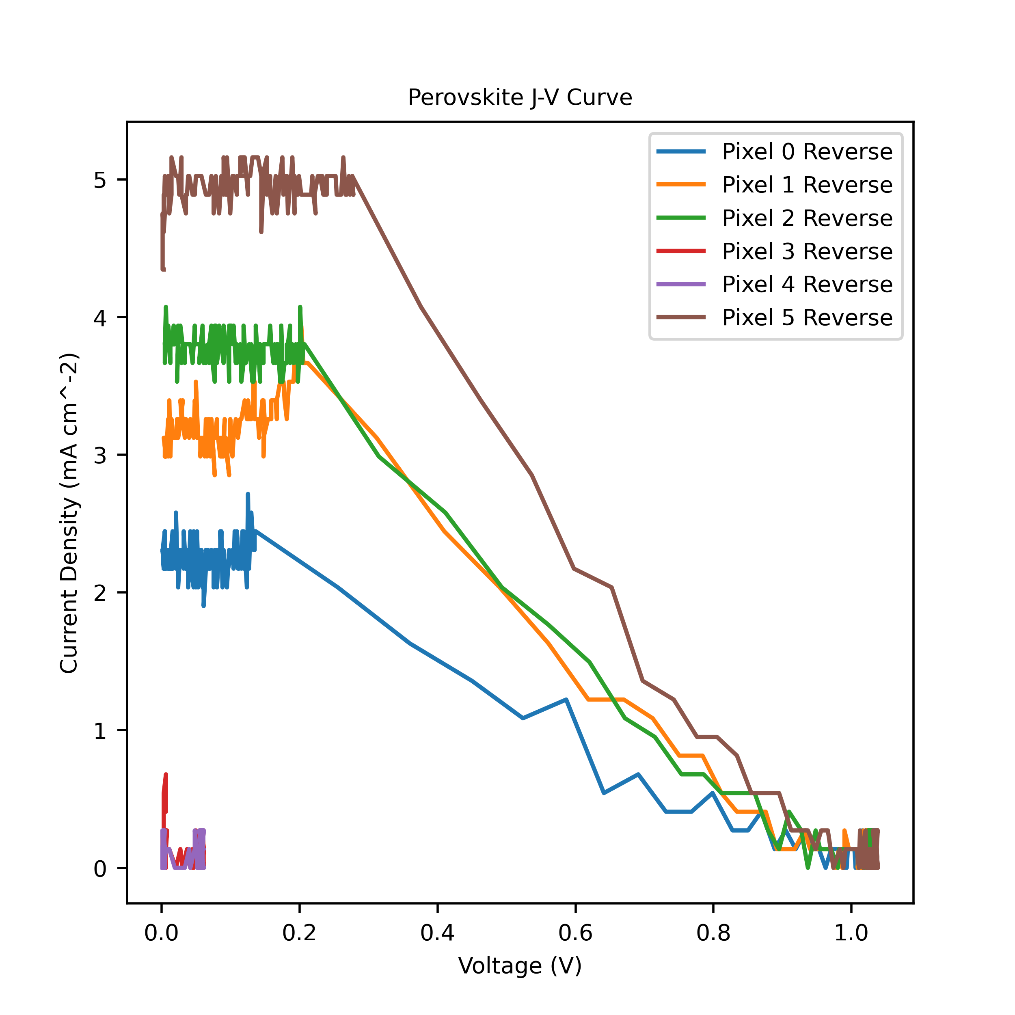
software/curves/Other/Test_New_2/Test_New_2_plotted_Reverse.png
