Big-Red-Sat/Perovskite-Curve-Tracer/software/curves/Other/Test_New_CT/Test_New_CT_plotted_Forward.png

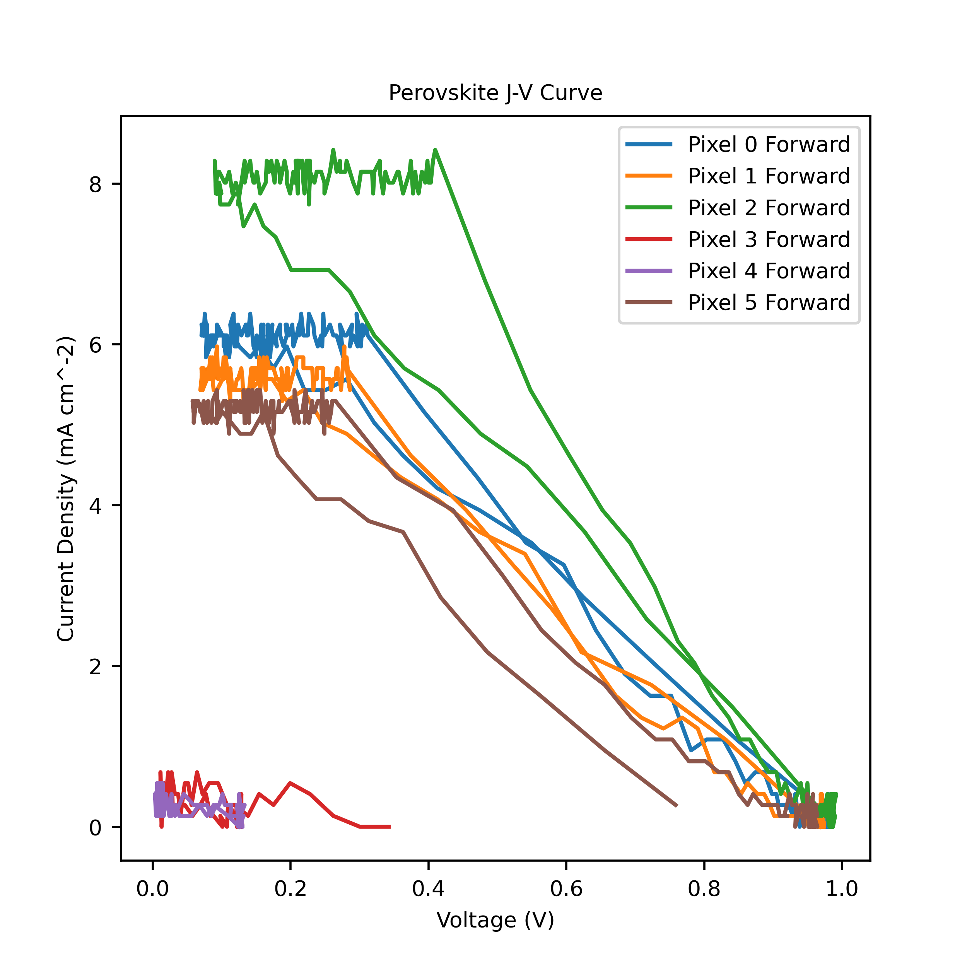
software/curves/Other/Test_New_CT/Test_New_CT_plotted_Forward.png
