Big-Red-Sat/Perovskite-Curve-Tracer/software/curves/X031_ShuntTest_500_LongSettle/X031_ShuntTest_500_LongSettle_plotted_Reverse.png

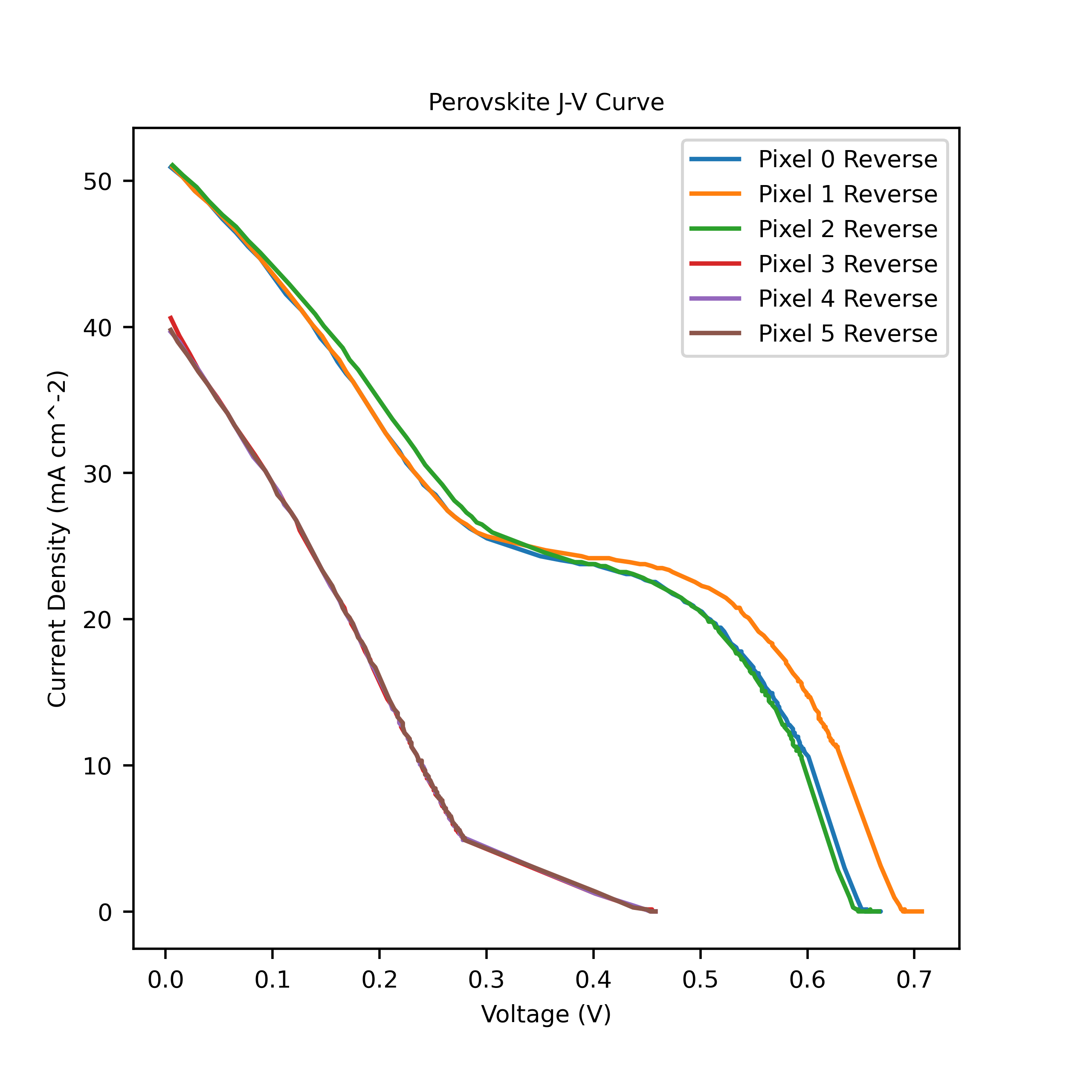
software/curves/X031_ShuntTest_500_LongSettle/X031_ShuntTest_500_LongSettle_plotted_Reverse.png
