Big-Red-Sat/Perovskite-Curve-Tracer/software/curves/1. Round One/1776 Degradation/1776 perovskite.jpg

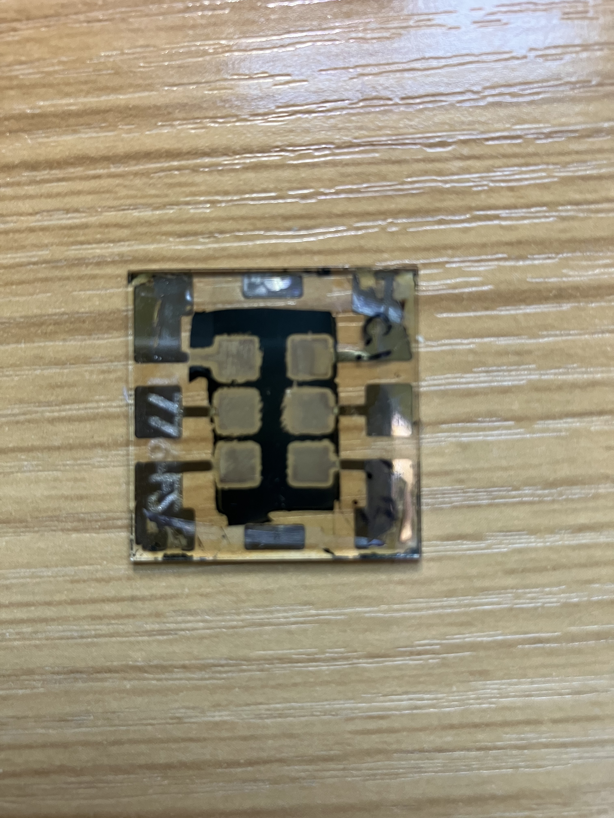
software/curves/1. Round One/1776 Degradation/1776 perovskite.jpg
